vllogic/dalishen_pi_h7p20/docs/reference_schs/HME-H7P0P20N0L176-M2H1_Eth_EVB_1_4原理图.pdf

## input voltage range

5V-14V | P12V

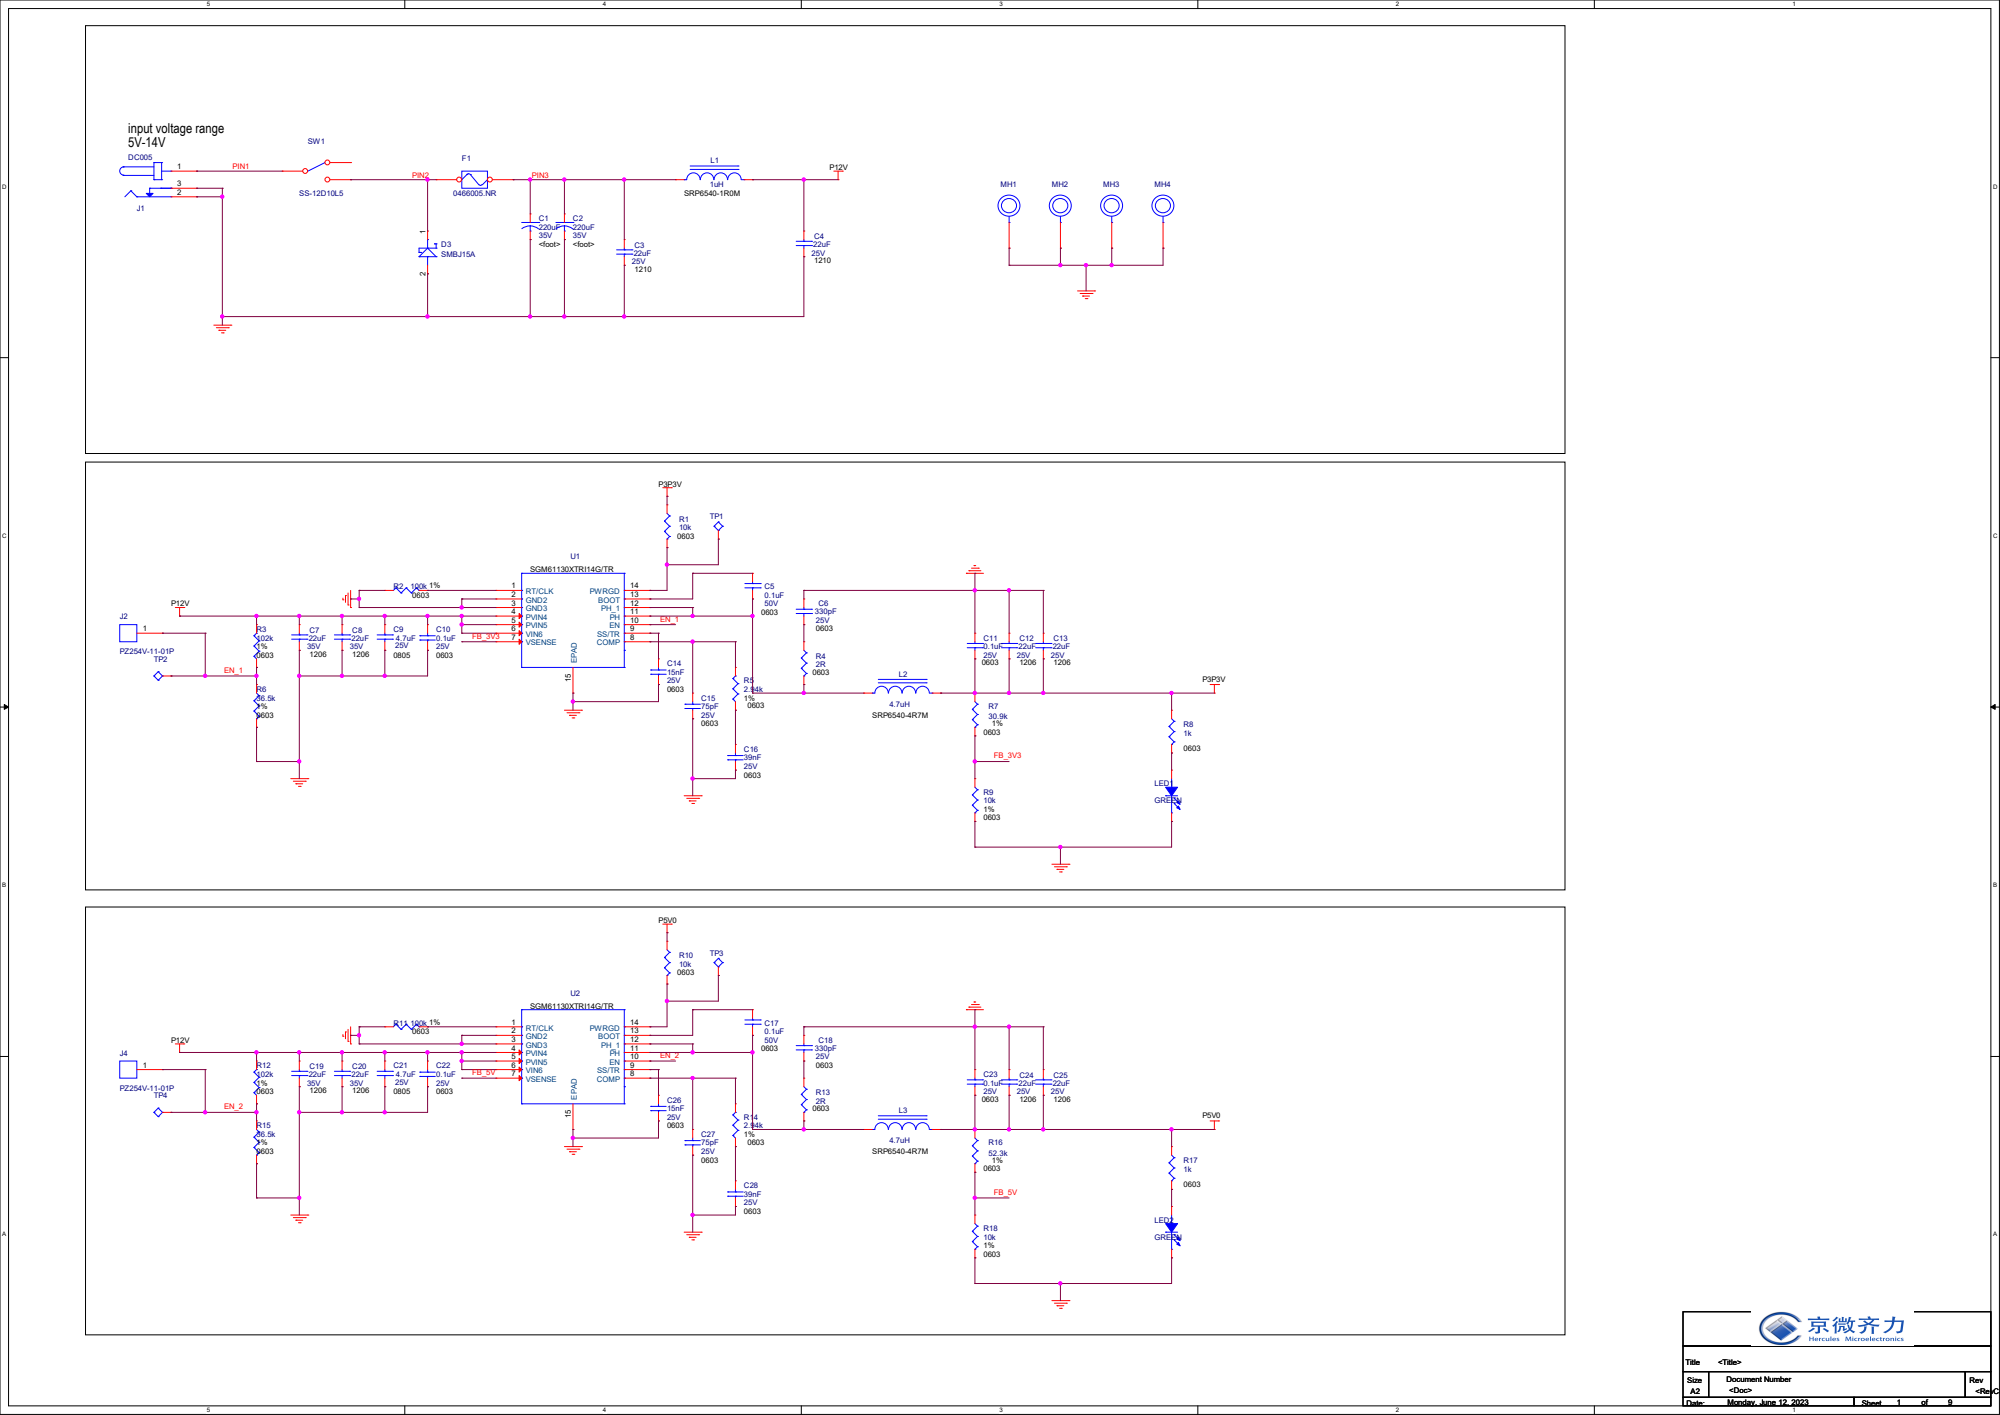
[picture p29: page 1]

# RXC_B RXDV_B RXD_B0 RXD_B3 GTXCLK_B

# TXD_B0 TXD_B1 TXD_B2 TXD_B3 RXD_B1 RXD_B2

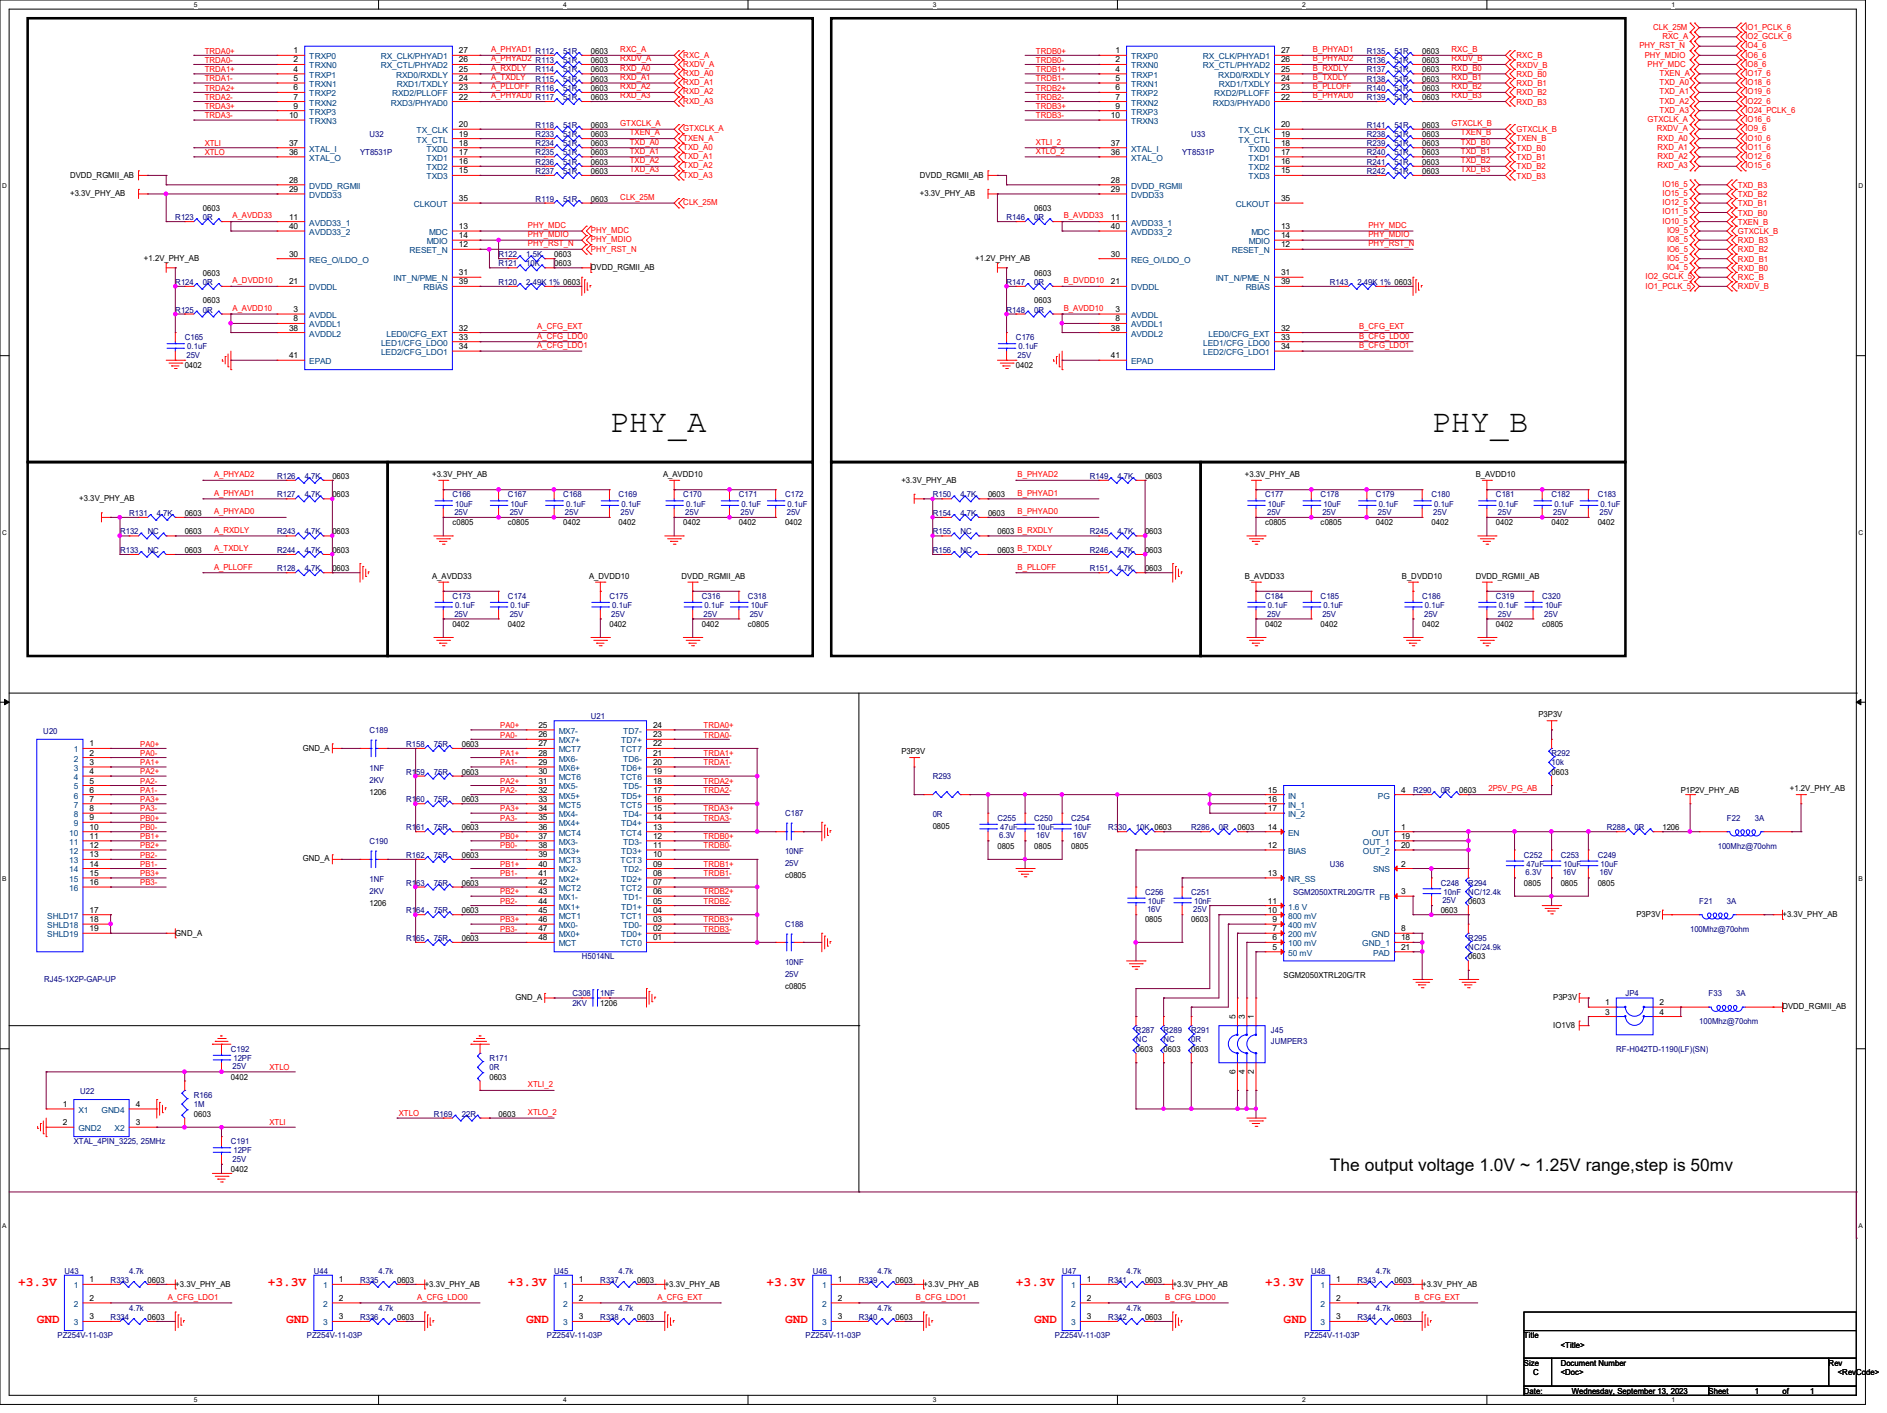
[picture p30: page 2]

The output voltage 1.0V ~ 1.25V range,step is 50mv

D D

# VCC5V_3

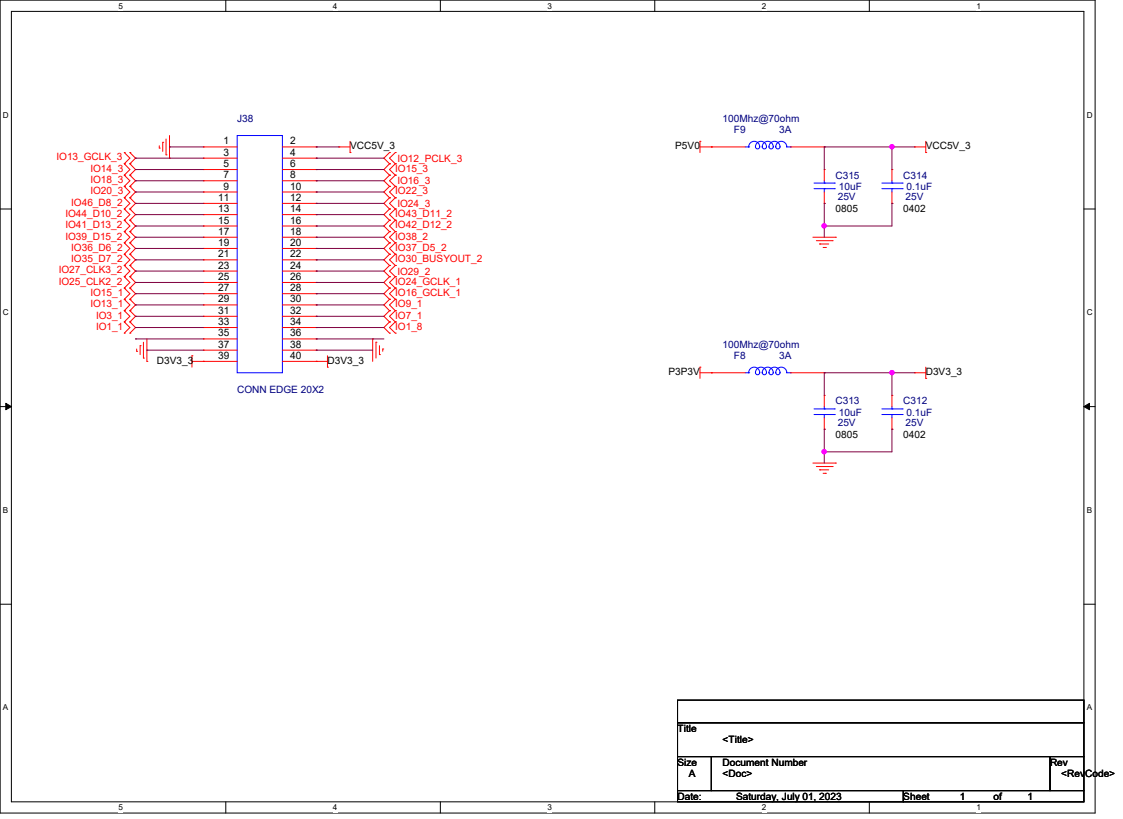
[picture p31: page 3]
VCC5V_3; IO16_GCLK_1; IO25_CLK2_2; IO30_BUSYOUT_2; IO13_GCLK_3; IO12_PCLK_3; IO27_CLK3_2; IO24_GCLK_1; Title; Size; Document Number; Rev; Date:; Sheet; <Doc>; <RevCode>; <Title>; Saturday, July 01, 2023; 100Mhz@70ohm 3A; CONN EDGE 20X2

DC005

# input voltage range

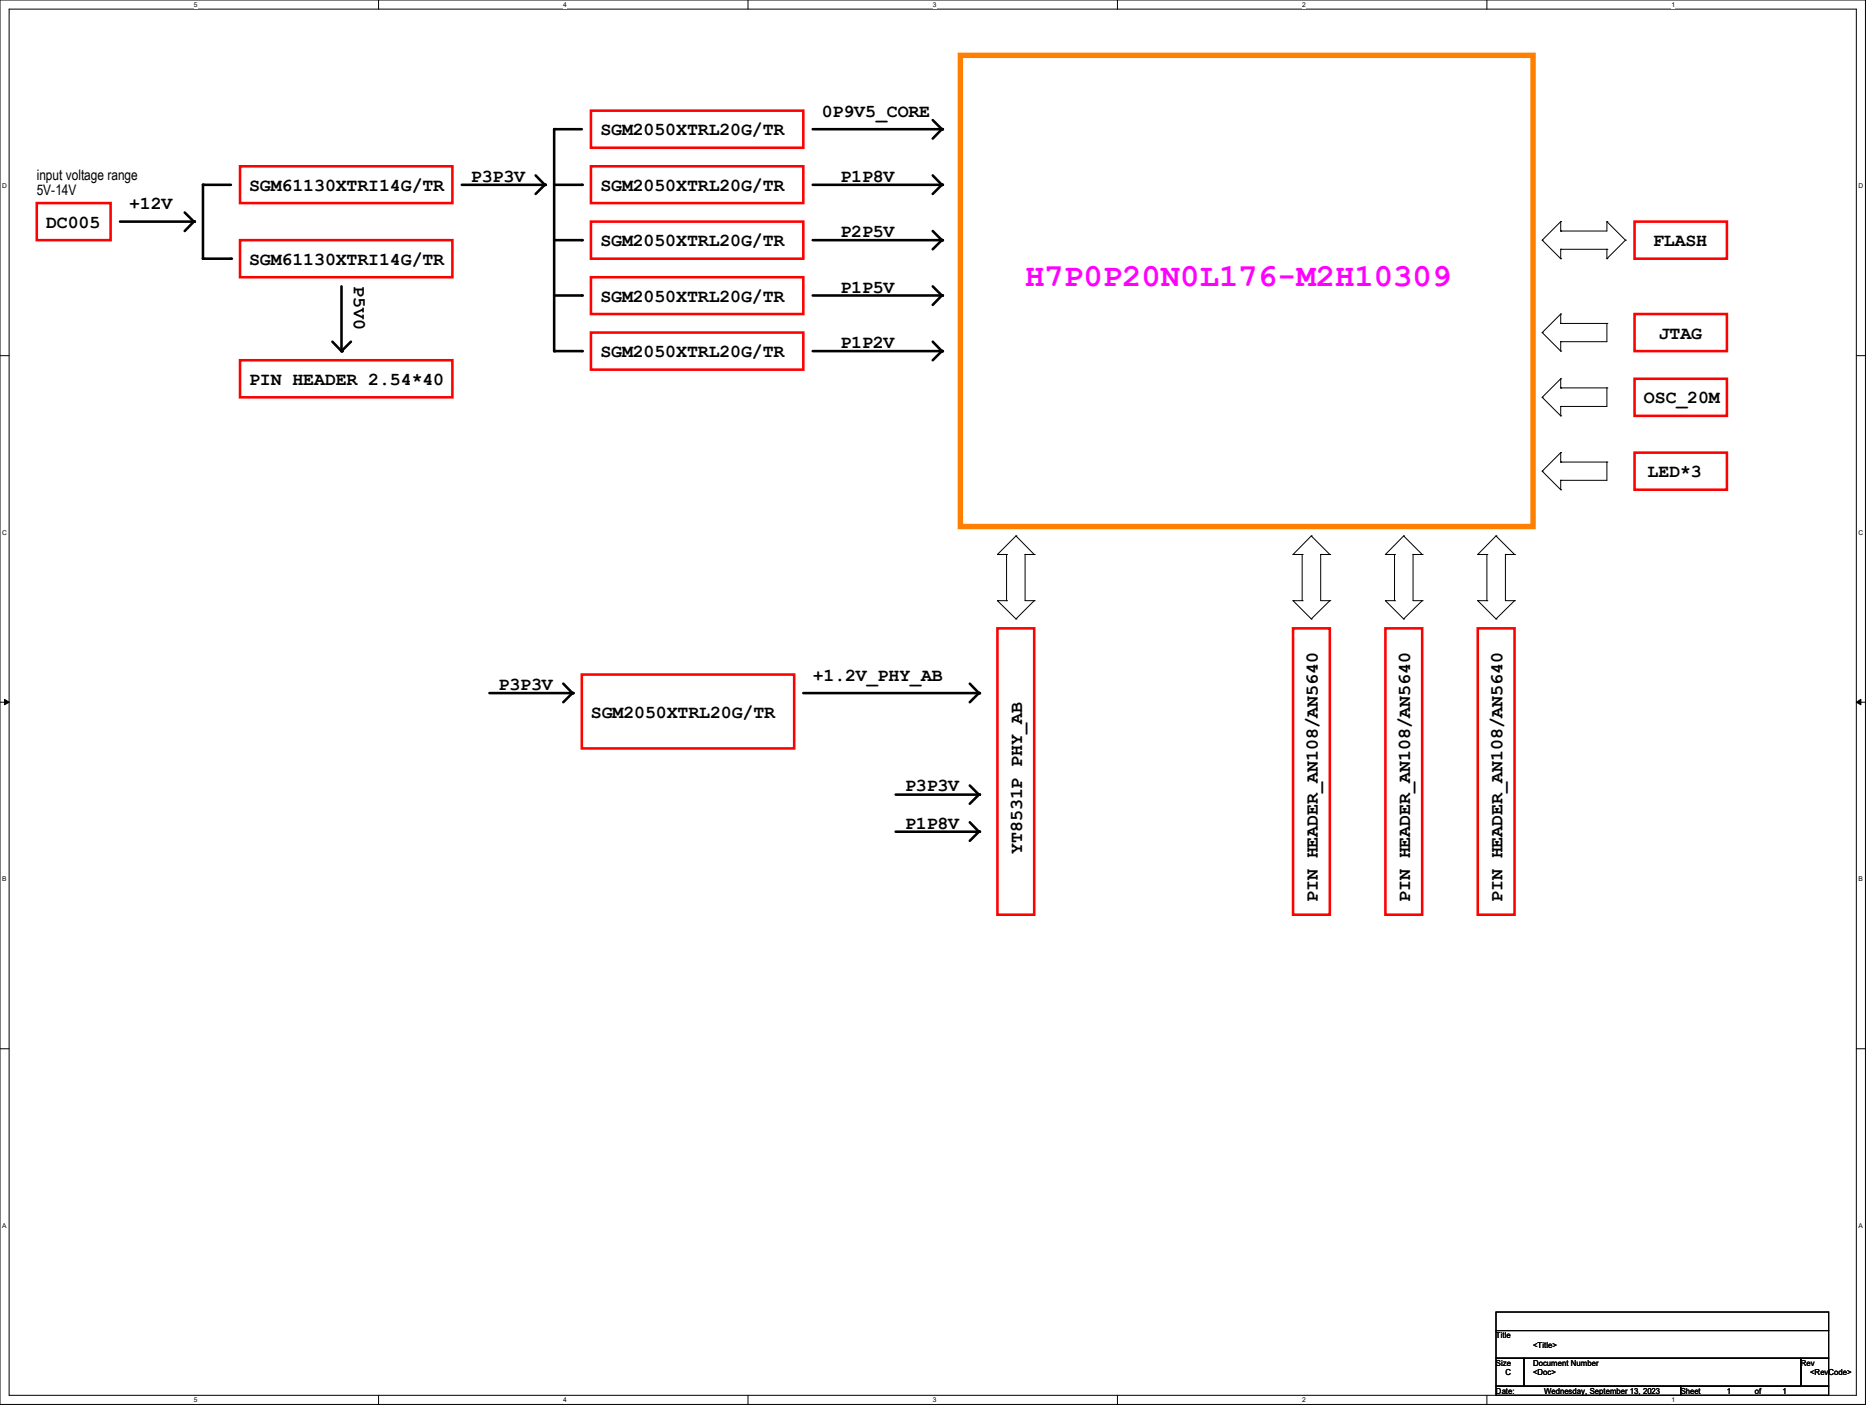
[picture p32: page 4]
SGM61130XTRI14G/TR; LED*3; FLASH; OSC_20M; JTAG YT8531P PHY_AB; PIN HEADER_AN108/AN5640; SGM2050XTRL20G/TR; 0P9V5_CORE; PIN HEADER 2.54*40; +1.2V_PHY_AB; Title Size; Document Number; Rev Date:; Sheet; of <Doc>; <RevCode>; <Title> C; Wednesday, September 13, 2023; 1 Title Size

### The output voltage 0.8V ~ 1.0V range,step is 50mv

# 2 S D3 R331

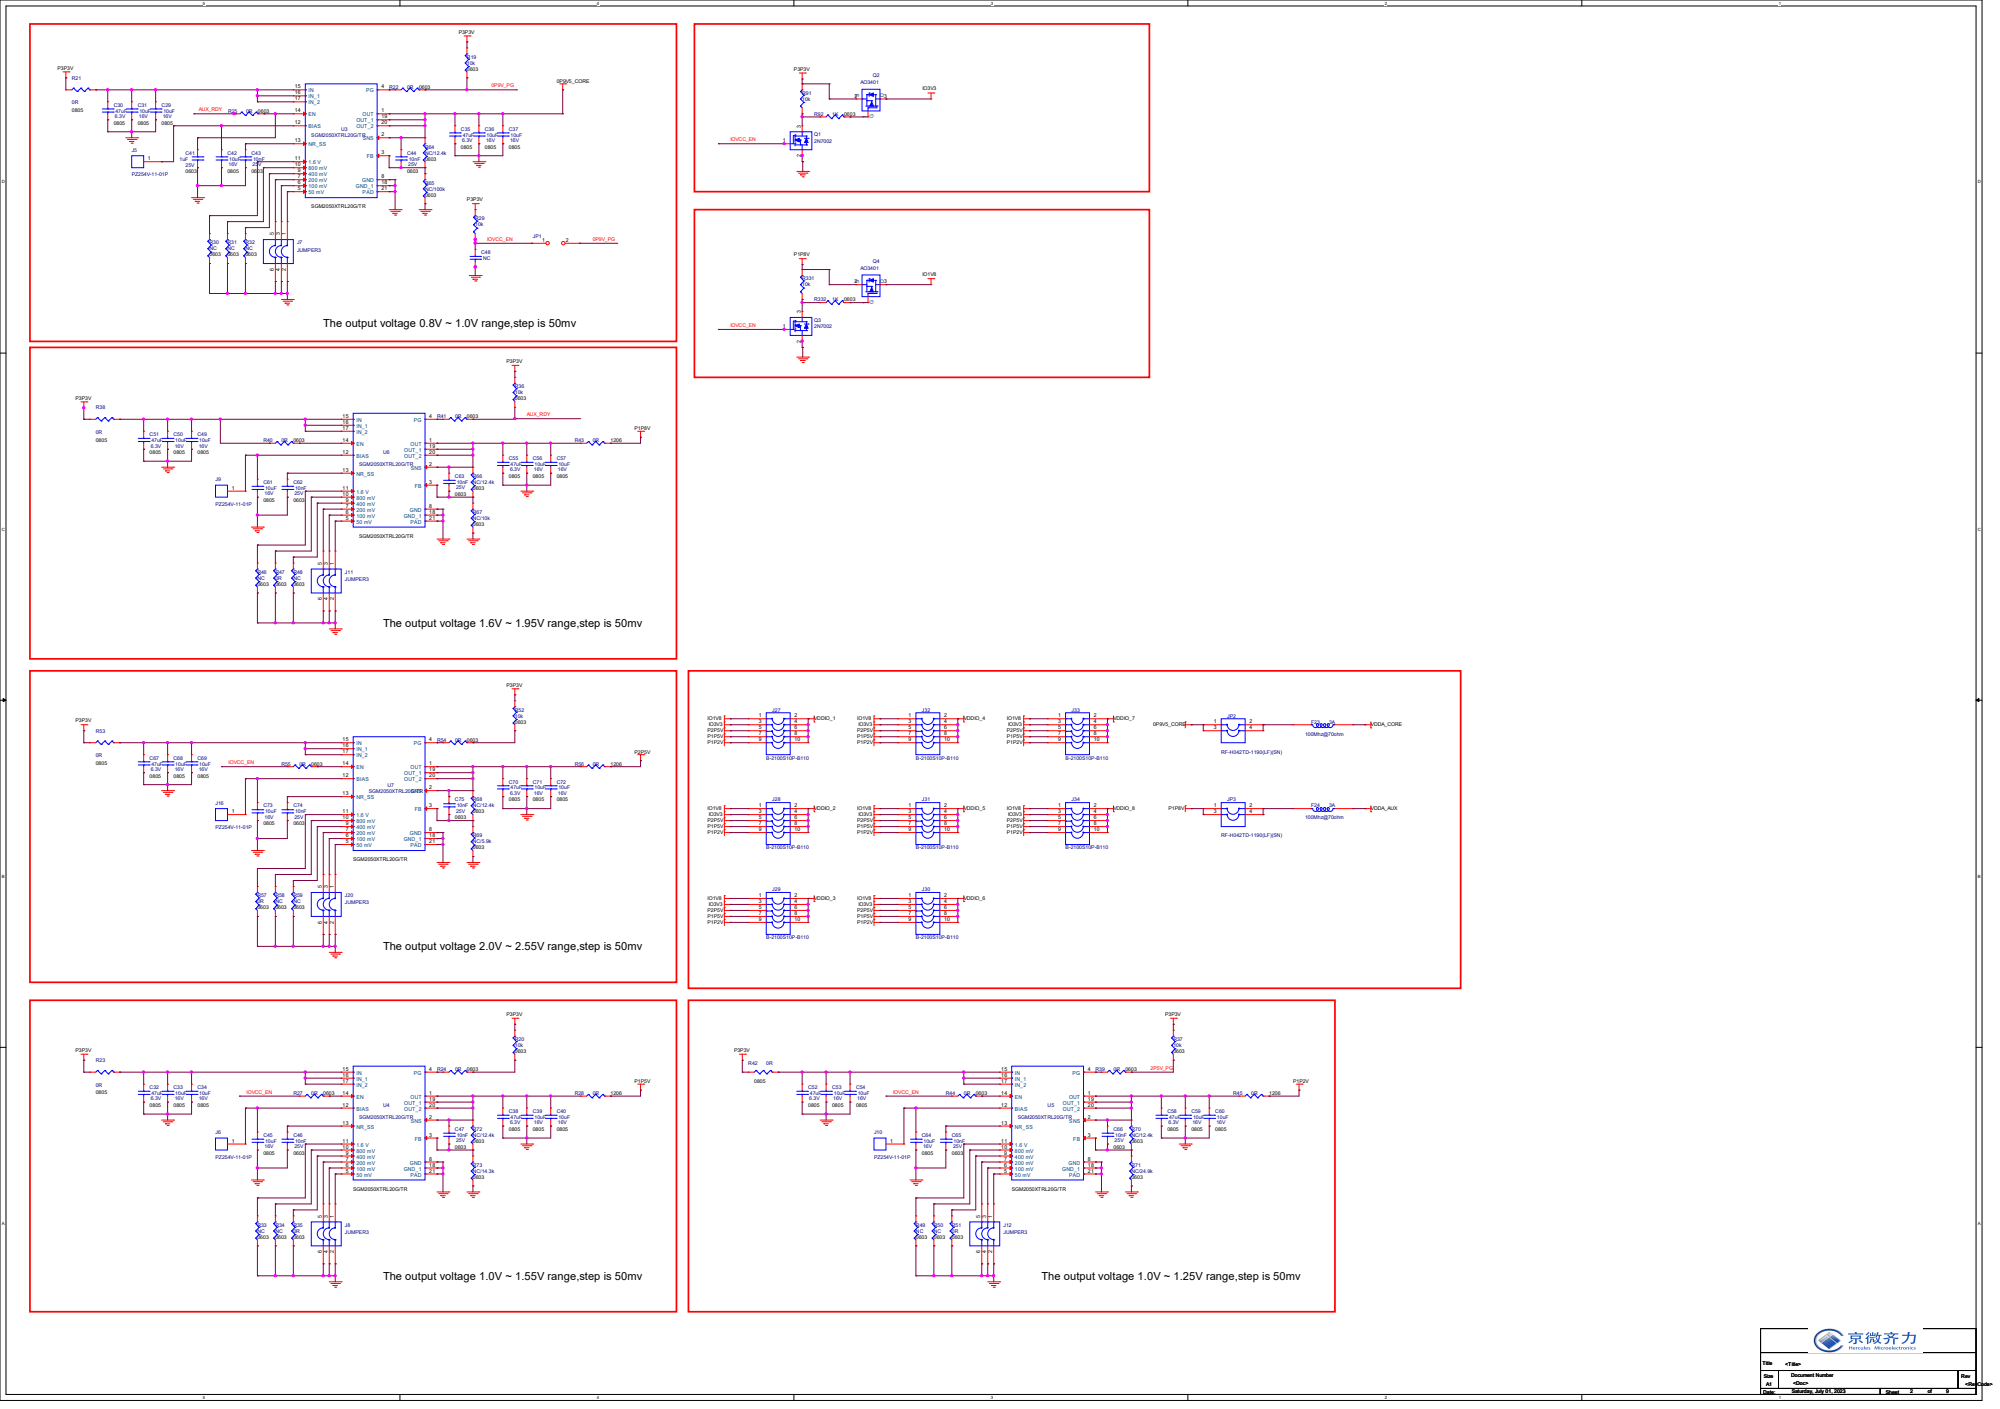
[picture p33: page 5]

The output voltage 1.6V ~ 1.95V range,step is 50mv

The output voltage 2.0V ~ 2.55V range,step is 50mv

D D

VDDA_AUX | VDDA_CORE

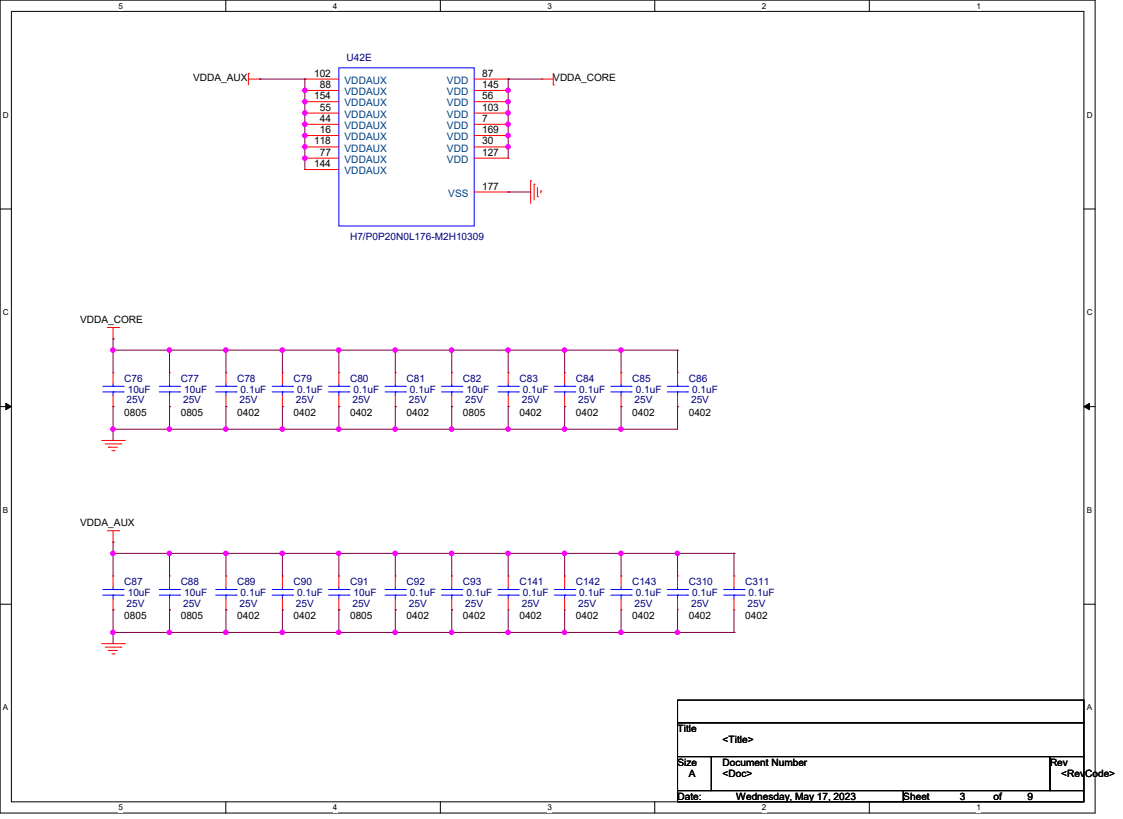
[picture p34: page 6]

# VDDIO1 VDDIO2 VDDIO_1

# BANK_1 BANK_2 U42A H7/P0P20N0L176-M2H10309

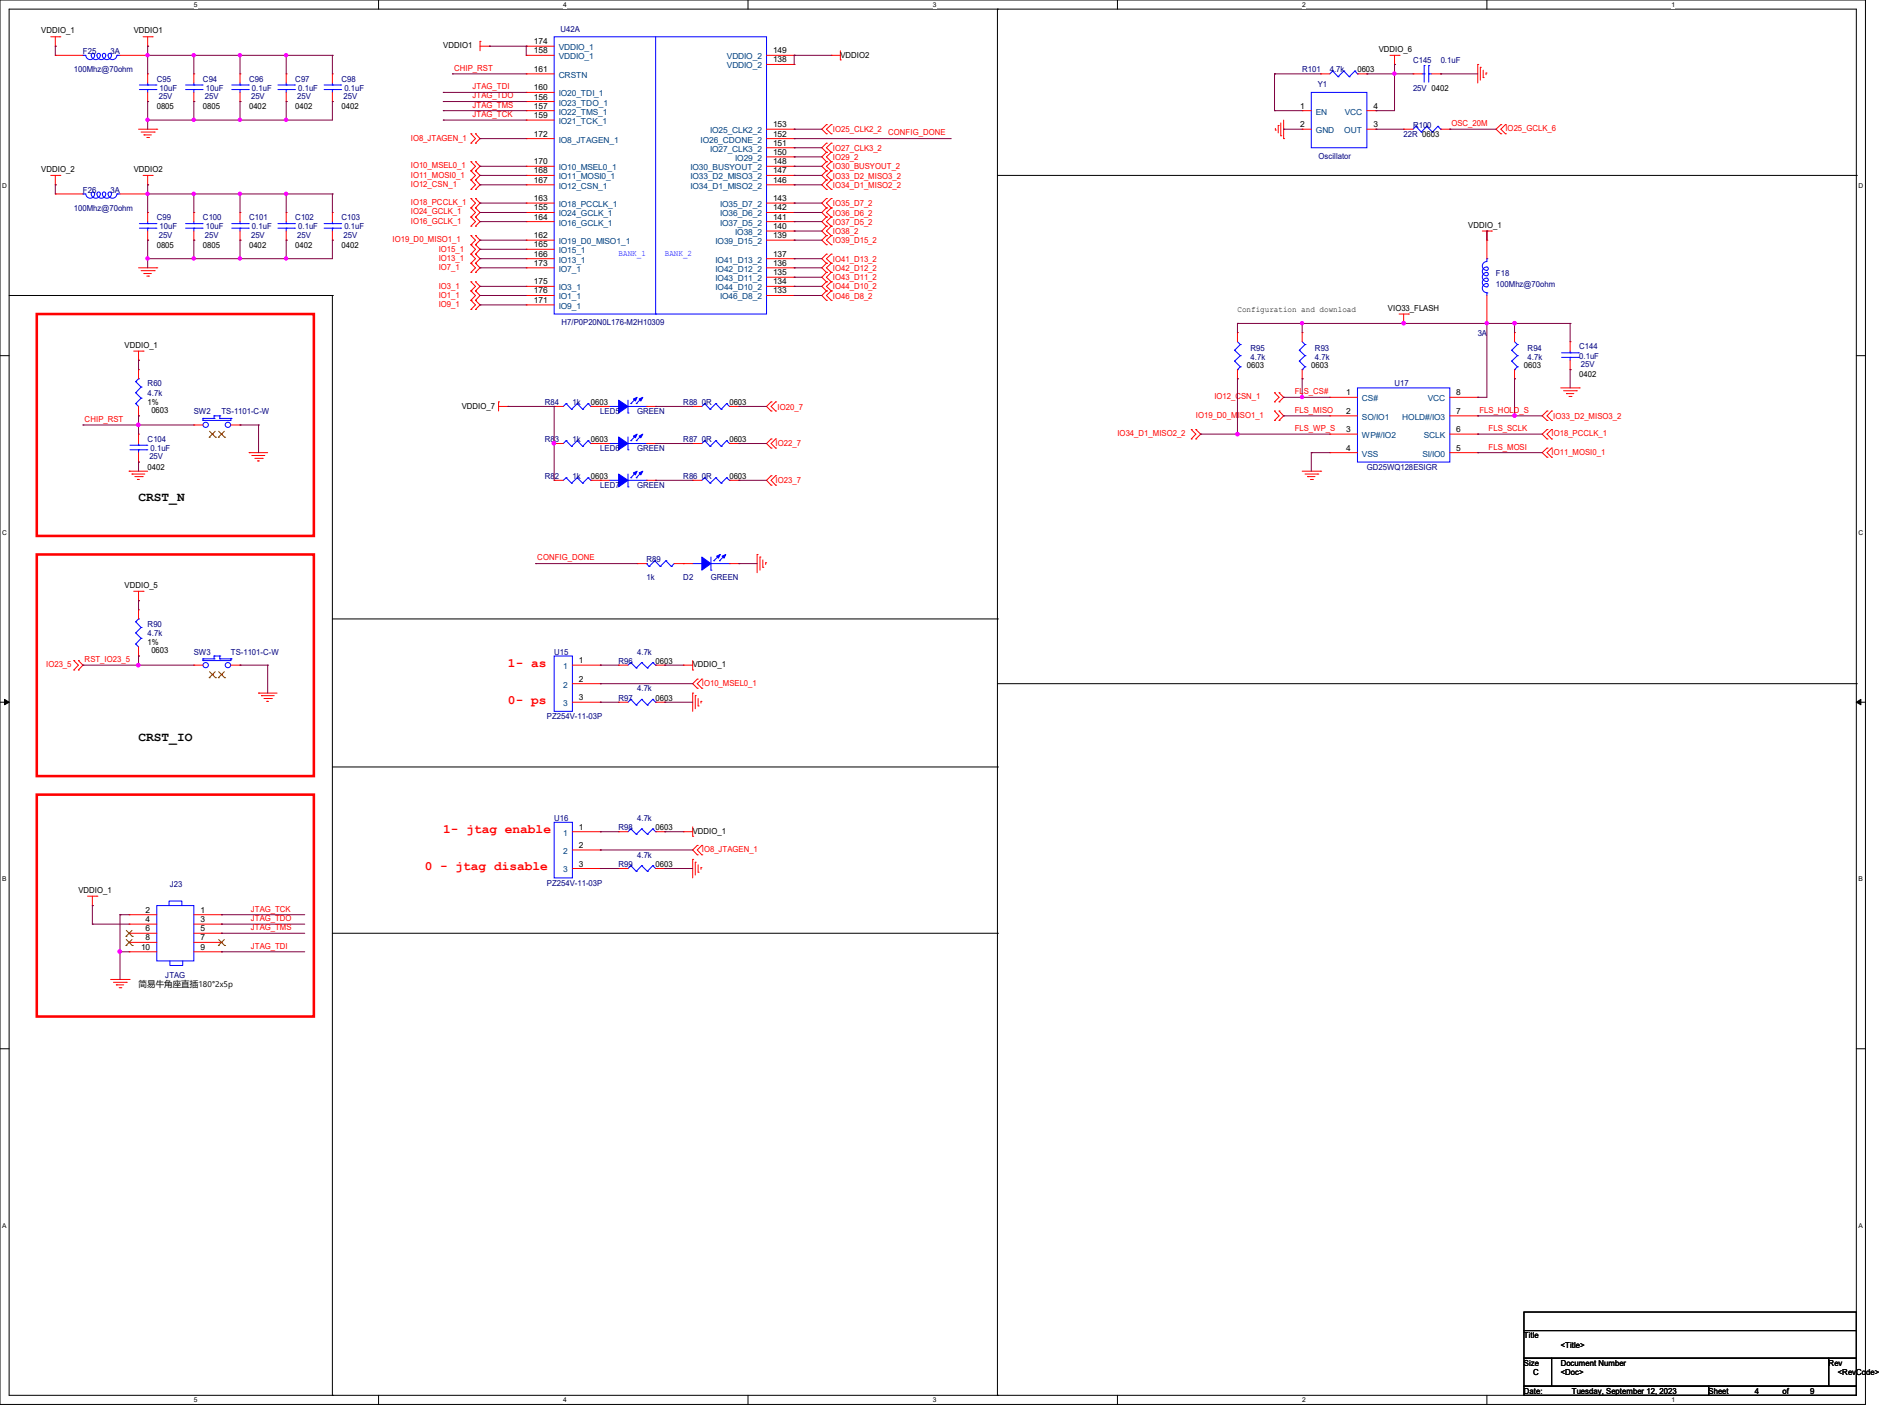
[picture p35: page 7]

VDDIO_1 | 100Mhz@70ohm

# VDDIO4 VDDIO3 VDDIO6 VDDIO5 VDDIO8 VDDIO7

# VDDIO_4 VDDIO_3 VDDIO_6 VDDIO_5 VDDIO_8 VDDIO_7

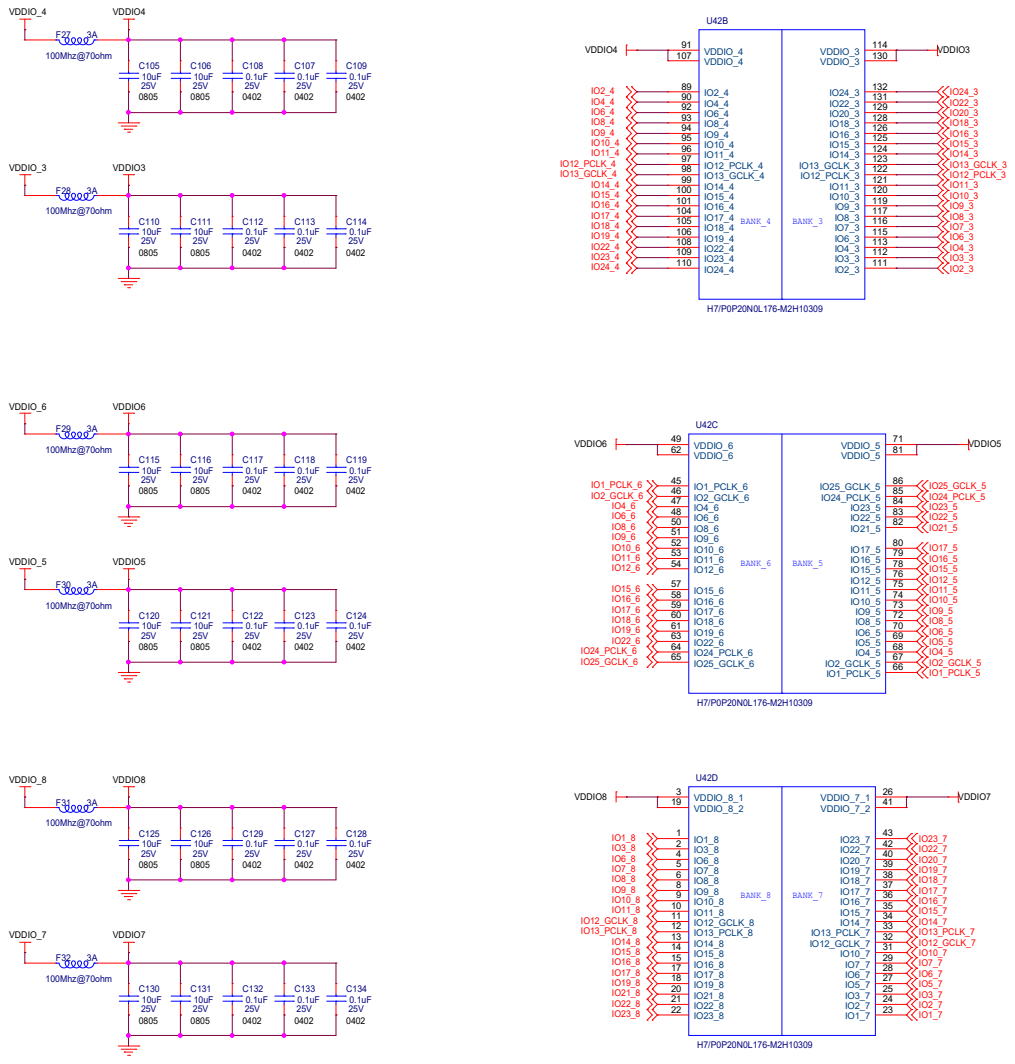
[picture p36: page 8]

D D

P5V0 | VCC5V_2

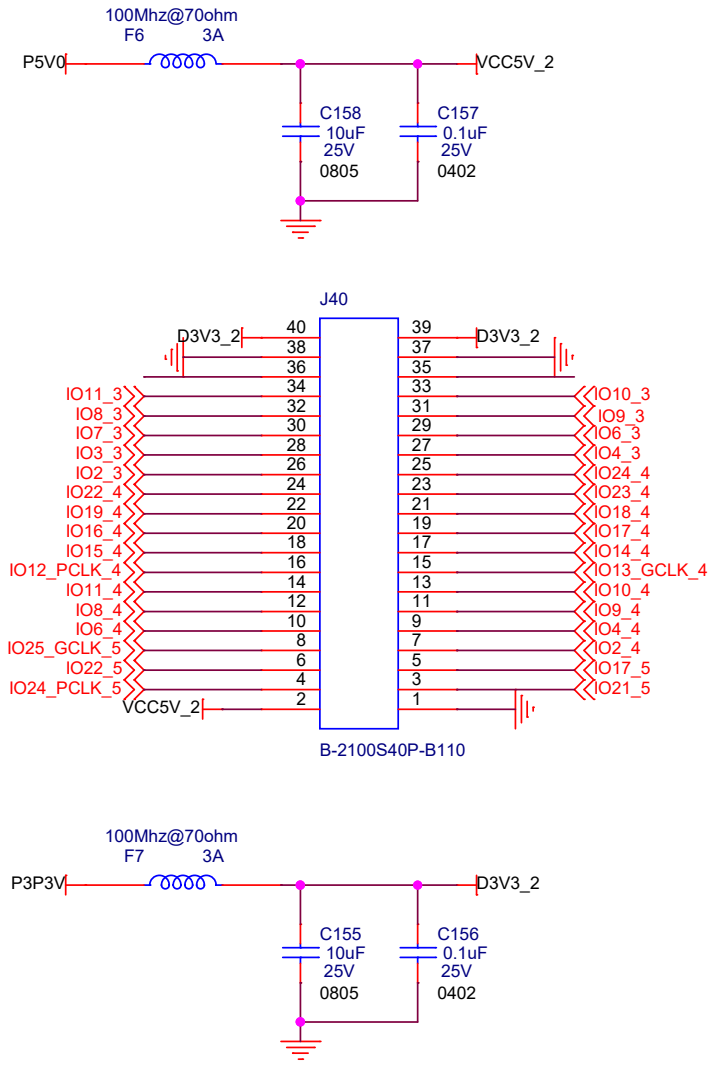
[picture p37: page 9]
VCC5V_2; IO13_GCLK_4; IO24_PCLK_5; IO25_GCLK_5; IO12_PCLK_4; Title; Size; Document Number; Rev; Date:; Sheet; <Doc>; <RevCode>; <Title>; Thursday, June 29, 2023; 100Mhz@70ohm 3A

# 3:LCD_R0/P1_DATA13/OS1/AD1DB11/VW_I2C_SCLK

# 1:GND

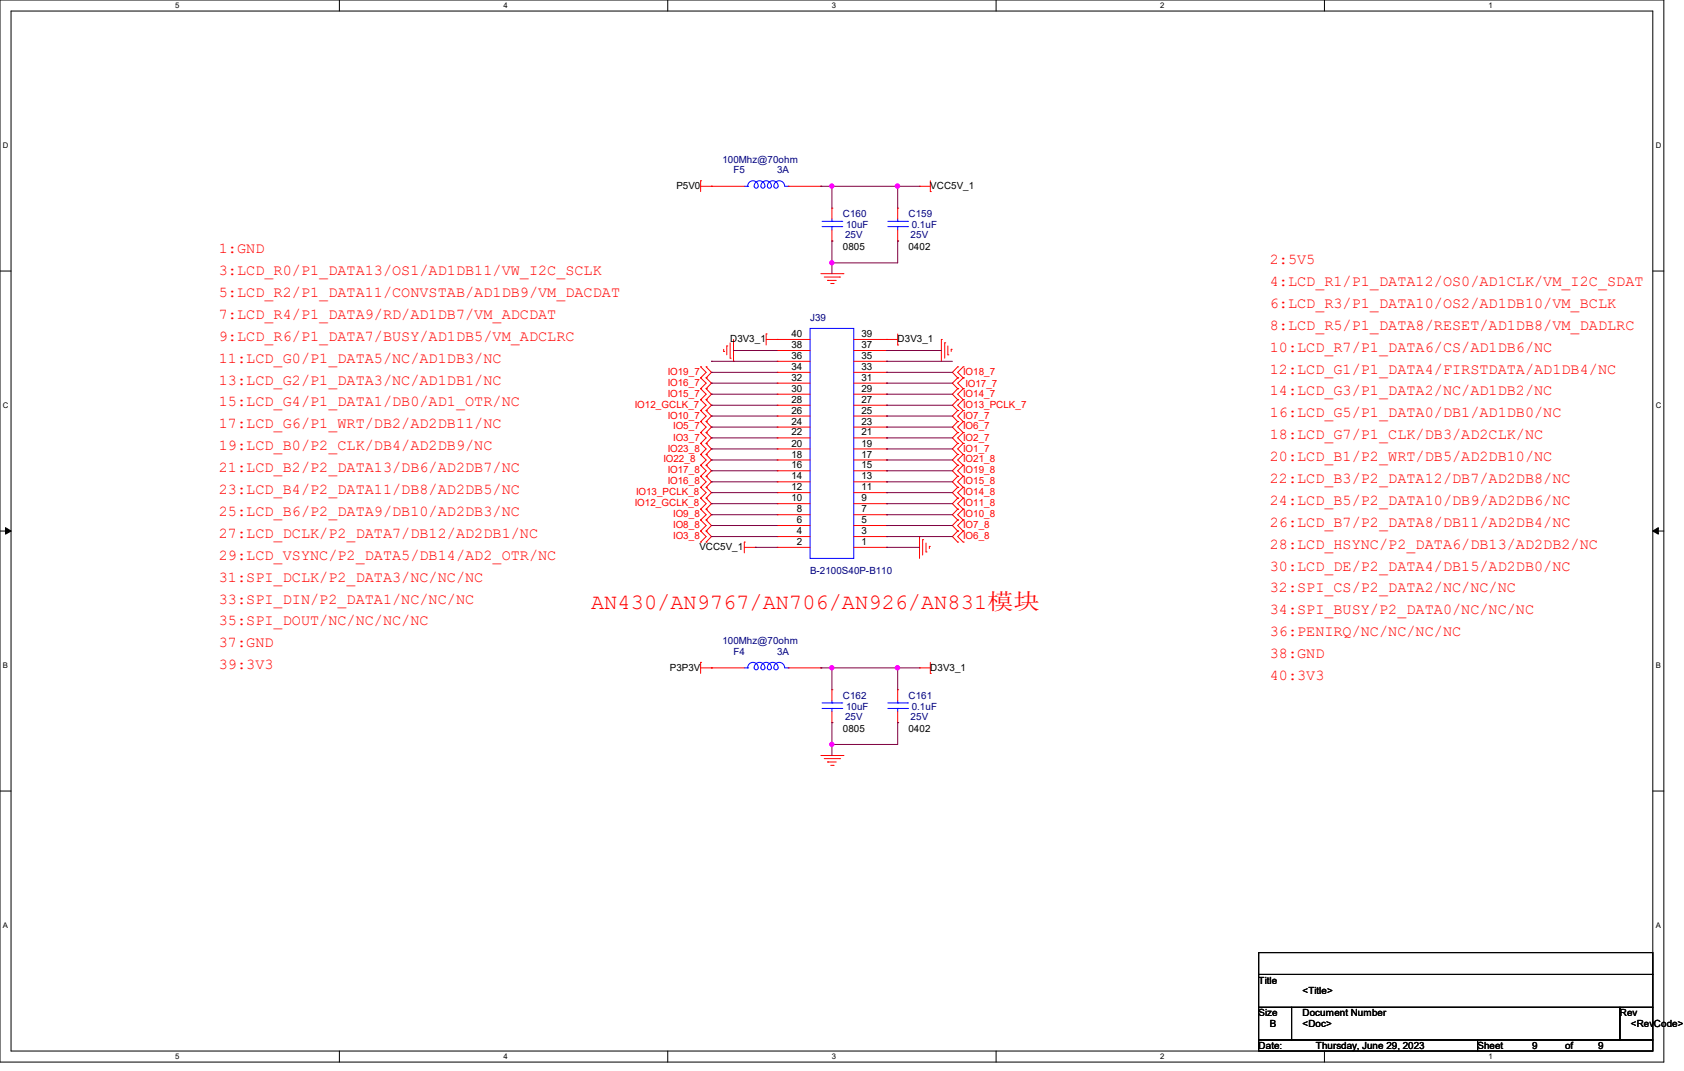
[picture p38: page 10]
11:LCD_G0/P1_DATA5/NC/AD1DB3/NC; 9:LCD_R6/P1_DATA7/BUSY/AD1DB5/VM_ADCLRC; 7:LCD_R4/P1_DATA9/RD/AD1DB7/VM_ADCDAT; 5:LCD_R2/P1_DATA11/CONVSTAB/AD1DB9/VM_DACDAT; 19:LCD_B0/P2_CLK/DB4/AD2DB9/NC; 17:LCD_G6/P1_WRT/DB2/AD2DB11/NC; 15:LCD_G4/P1_DATA1/DB0/AD1_OTR/NC; 13:LCD_G2/P1_DATA3/NC/AD1DB1/NC; 27:LCD_DCLK/P2_DATA7/DB12/AD2DB1/NC; 25:LCD_B6/P2_DATA9/DB10/AD2DB3/NC; 23:LCD_B4/P2_DATA11/DB8/AD2DB5/NC; 21:LCD_B2/P2_DATA13/DB6/AD2DB7/NC; 35:SPI_DOUT/NC/NC/NC/NC; 33:SPI_DIN/P2_DATA1/NC/NC/NC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
