vllogic/dalishen_pi_h7p20/docs/reference_schs/MLK-S301-20230721.pdf

# 2 S D3 C⁶ 22uF/25V

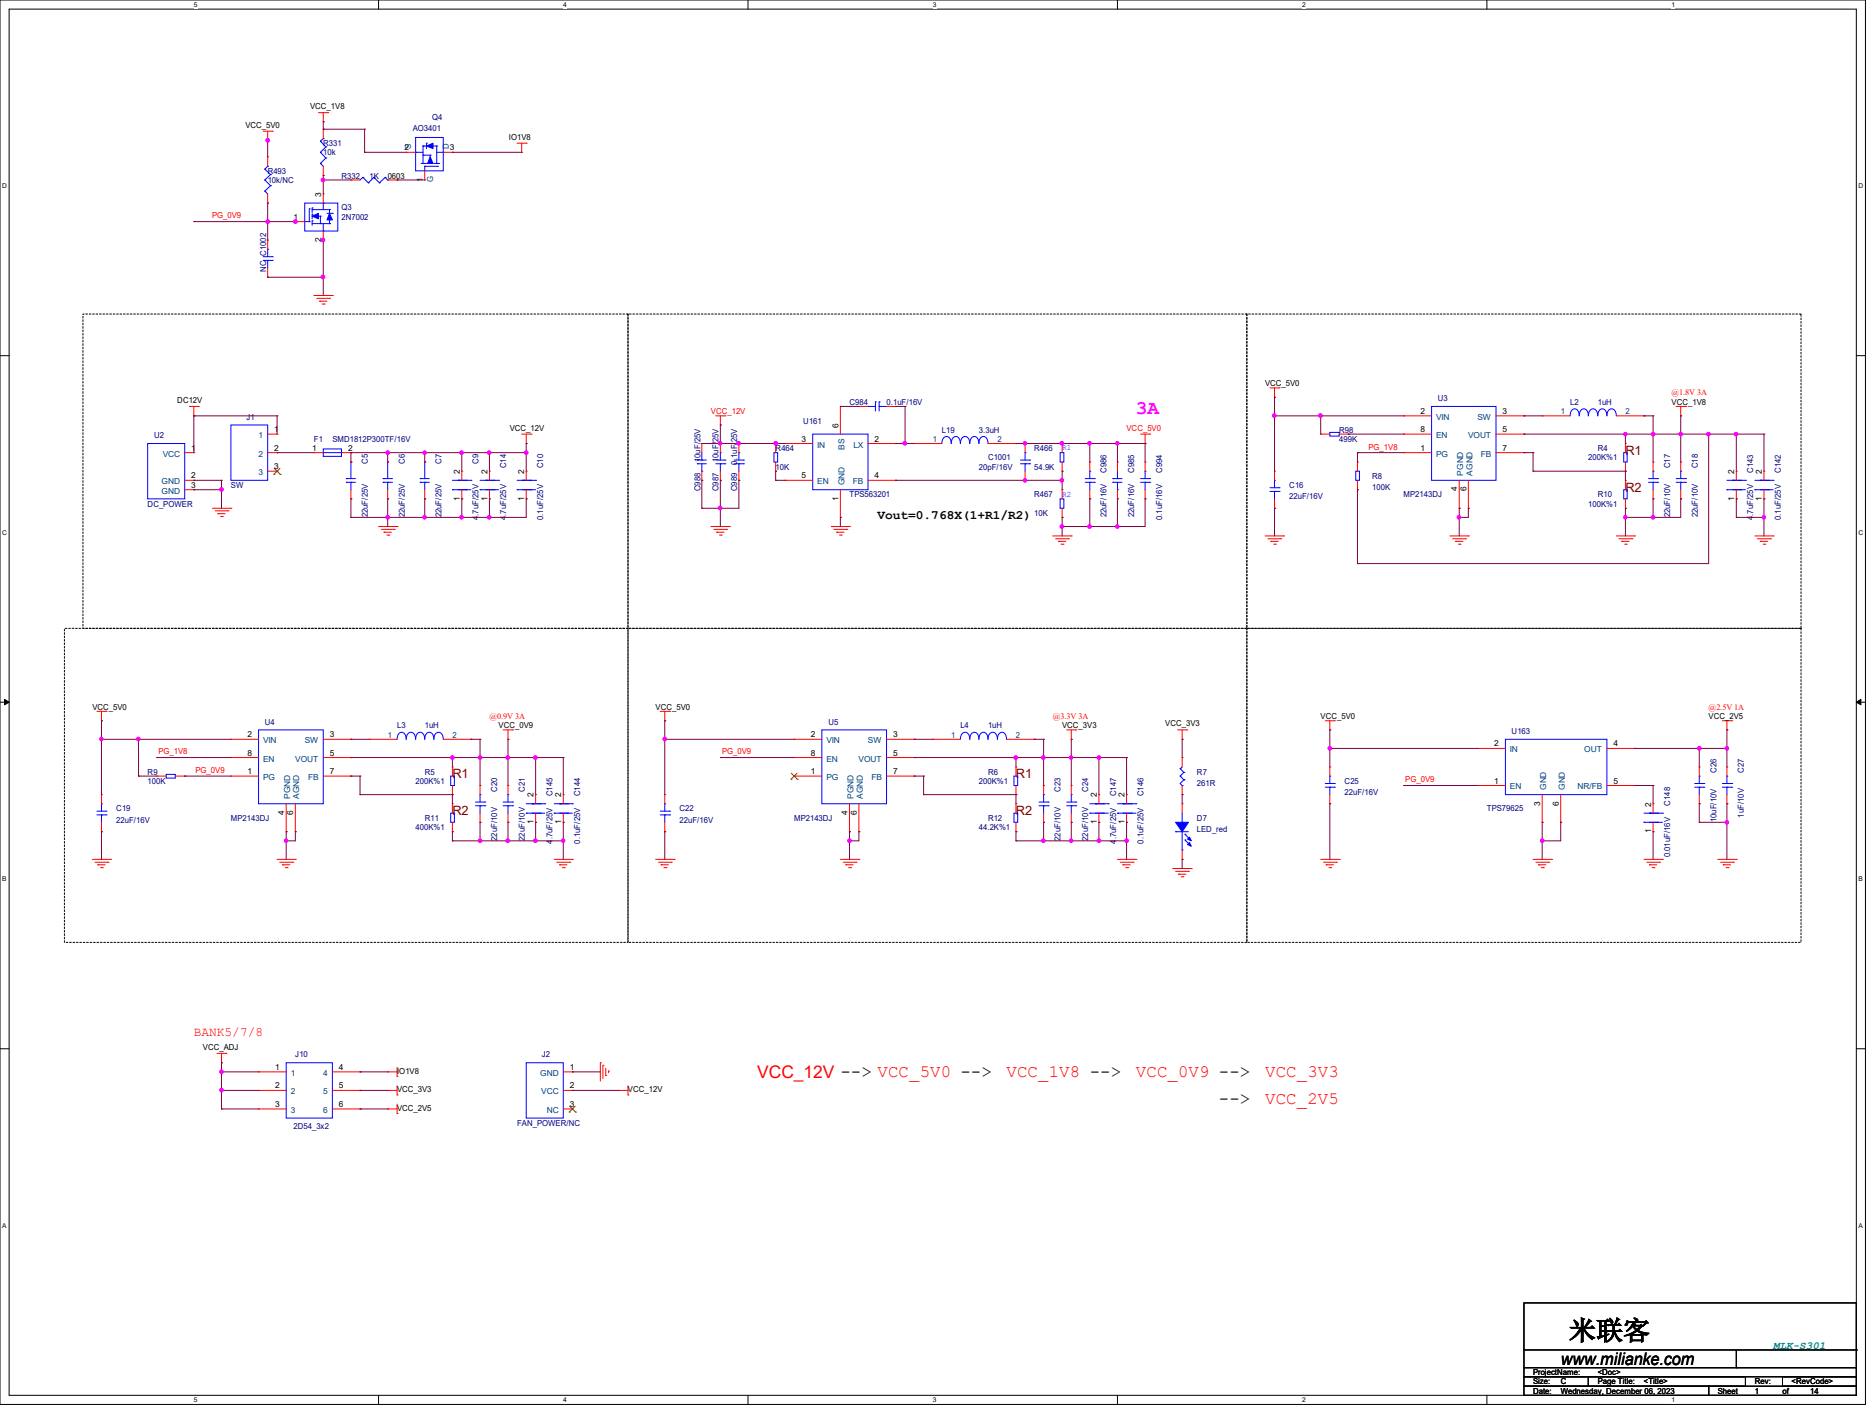
[picture p39: page 1]

3 OUT 4 NR/FB 5 GND

VDDA_AUX | VDDA_CORE
VCC_1V8 | VCC_0V9

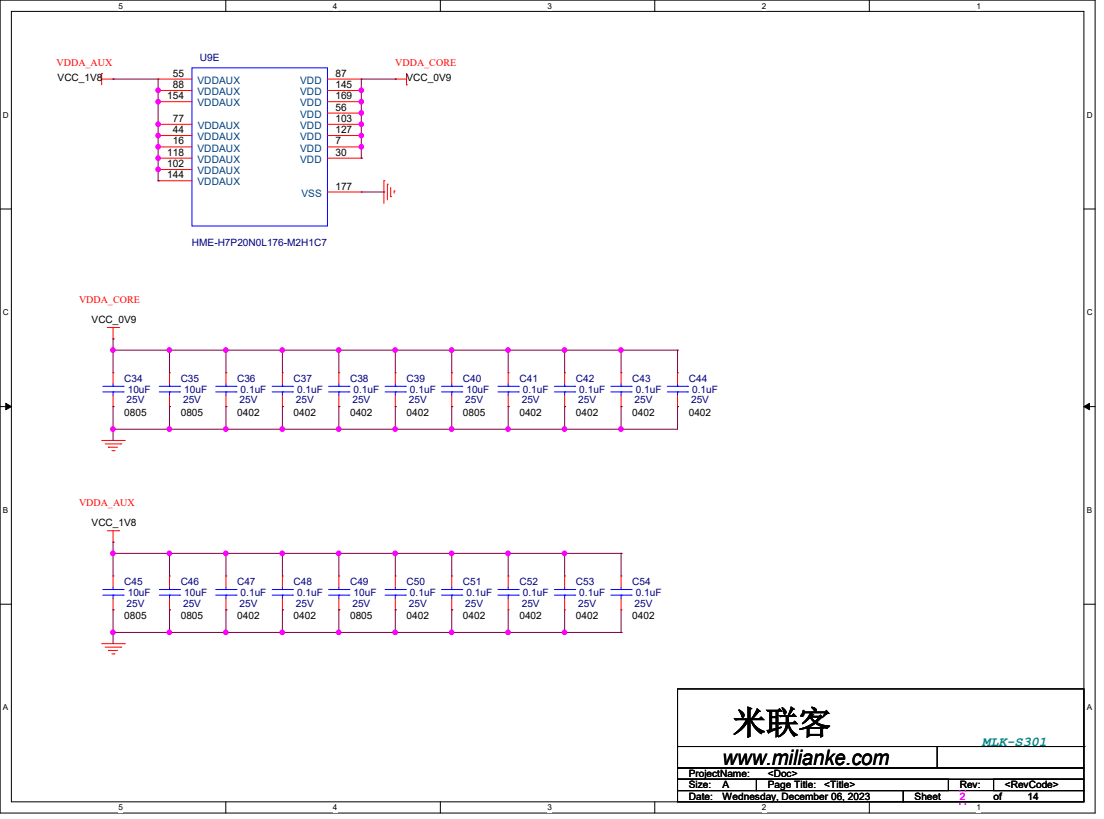
[picture p40: page 2]

### VDDIO_1

### VDDIO_2

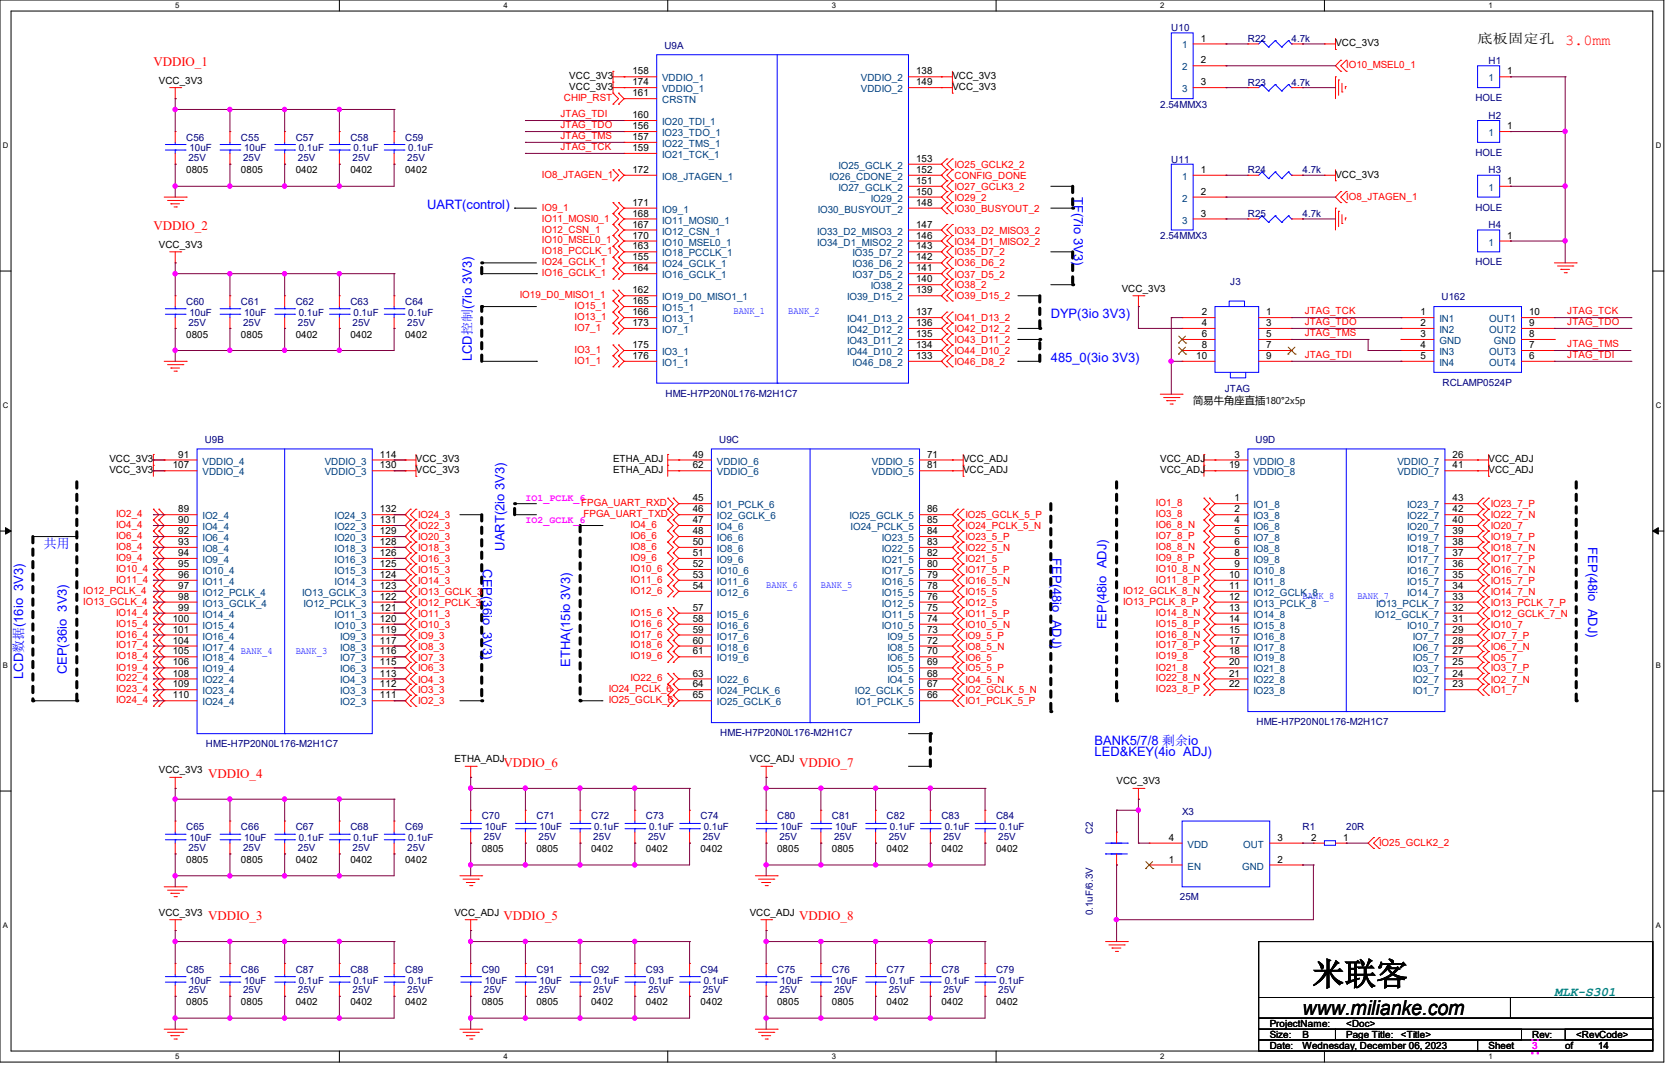
[picture p41: page 3]

底板固定孔 3.0mm FEP(48io ADJ)FEP⁽⁴⁸io ADJ⁾ FEP(48io ADJ)
U9A HME-H7P20N0L176-M2H1C7

## VCC_3V3

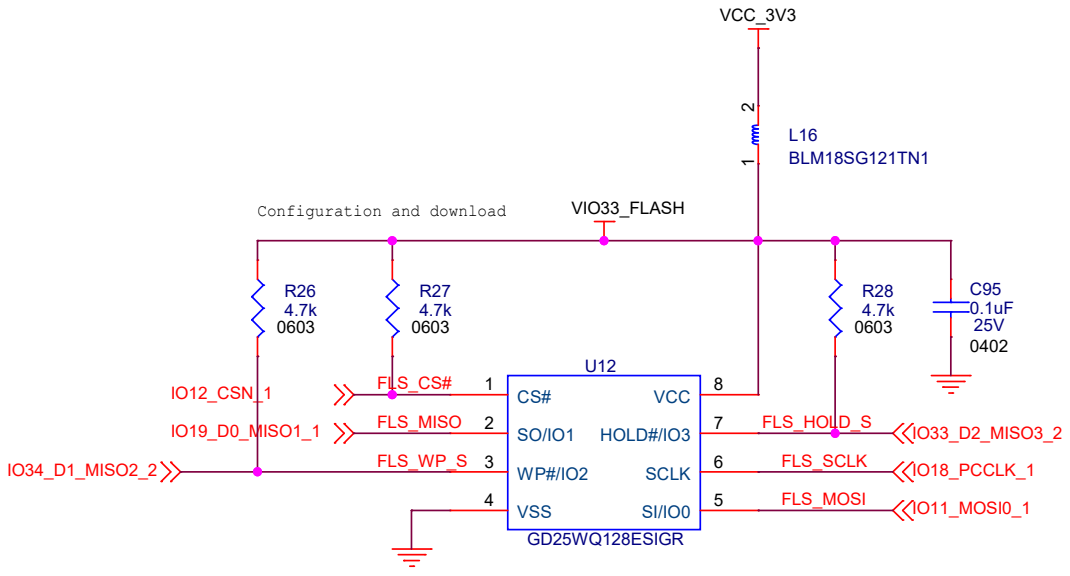
[picture p42: page 4]
MLK-S301; VIO33_FLASH; IO33_D2_MISO3_2; IO34_D1_MISO2_2; IO11_MOSI0_1; IO12_CSN_1; IO18_PCCLK_1; IO19_D0_MISO1_1; Date:; Sheet Wednesday, December 06, 2023; Wednesday, December 06, 2023; L16 1BLM18SG121TN1; GD25WQ128ESIGR; VSS 4; SCLK 6; HOLD#/IO3 7; VCC 8; FLS_WP_S; FLS_MISO; FLS_HOLD_S; FLS_SCLK; FLS_CS#; FLS_MOSI

Configuration and download

米联客
www.milianke.com

## VCC_3V3 VCC_3V3

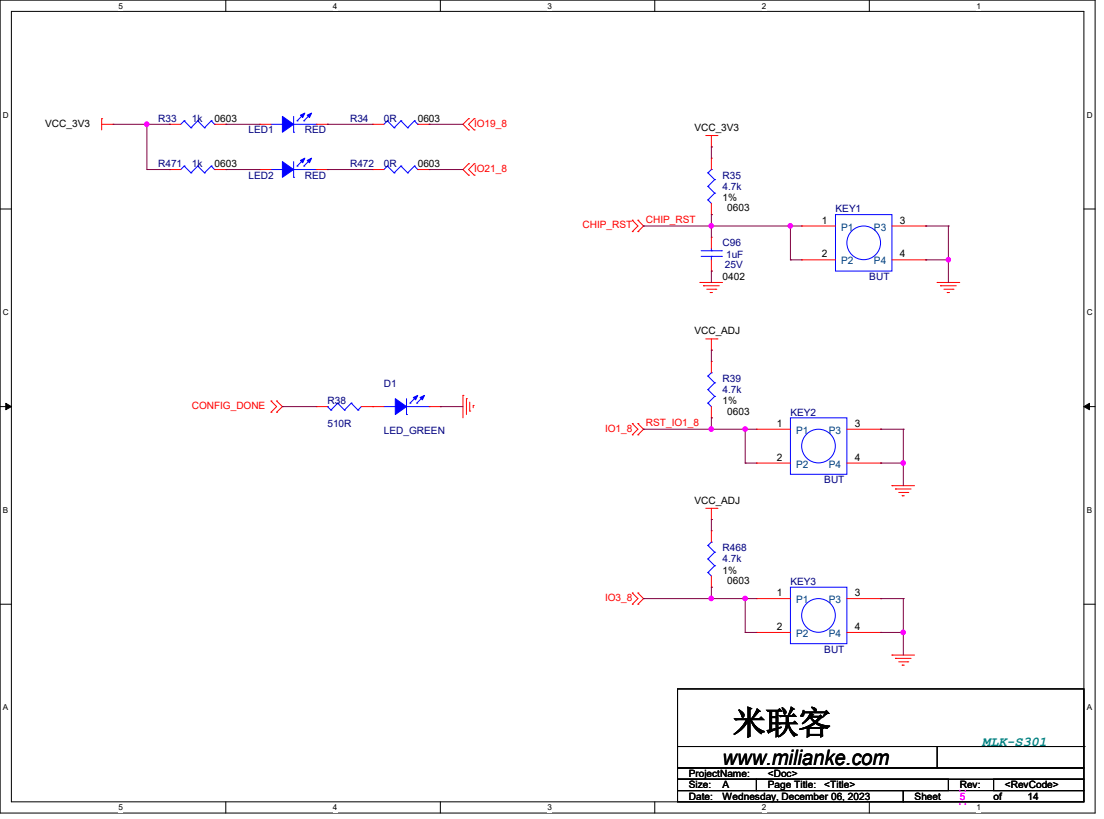
[picture p43: page 5]

## VBUS0_3V3

C97 | 100nF/25V

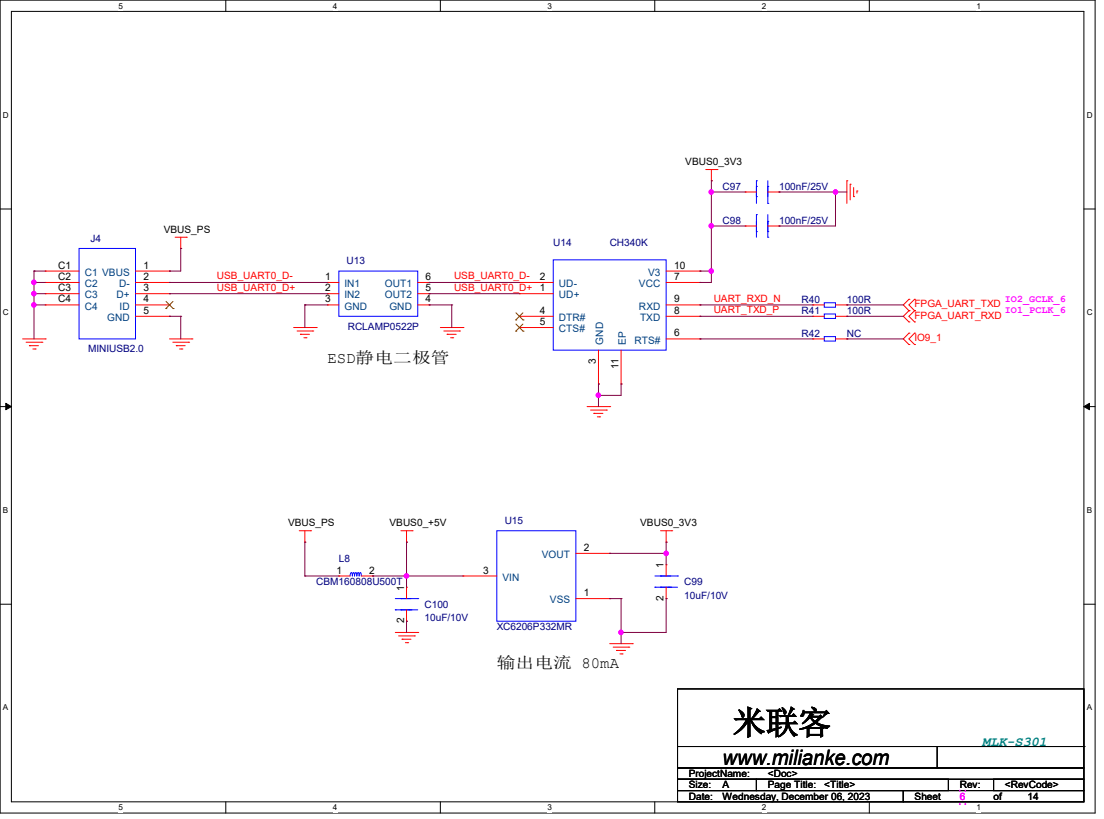
[picture p44: page 6]

HDI0+ 2 | HDI0- 3 | HDI1+ 4 | HDI1- 7 | HDI2+ 5 | HDI2- 6 | HDIO3+ 8 | HDIO3- 9 | TCT 1 | GND 10
VDD 4 | EN 1 | OUT | 3 GND | 2 C¹⁰⁴ 0.1uF/16V

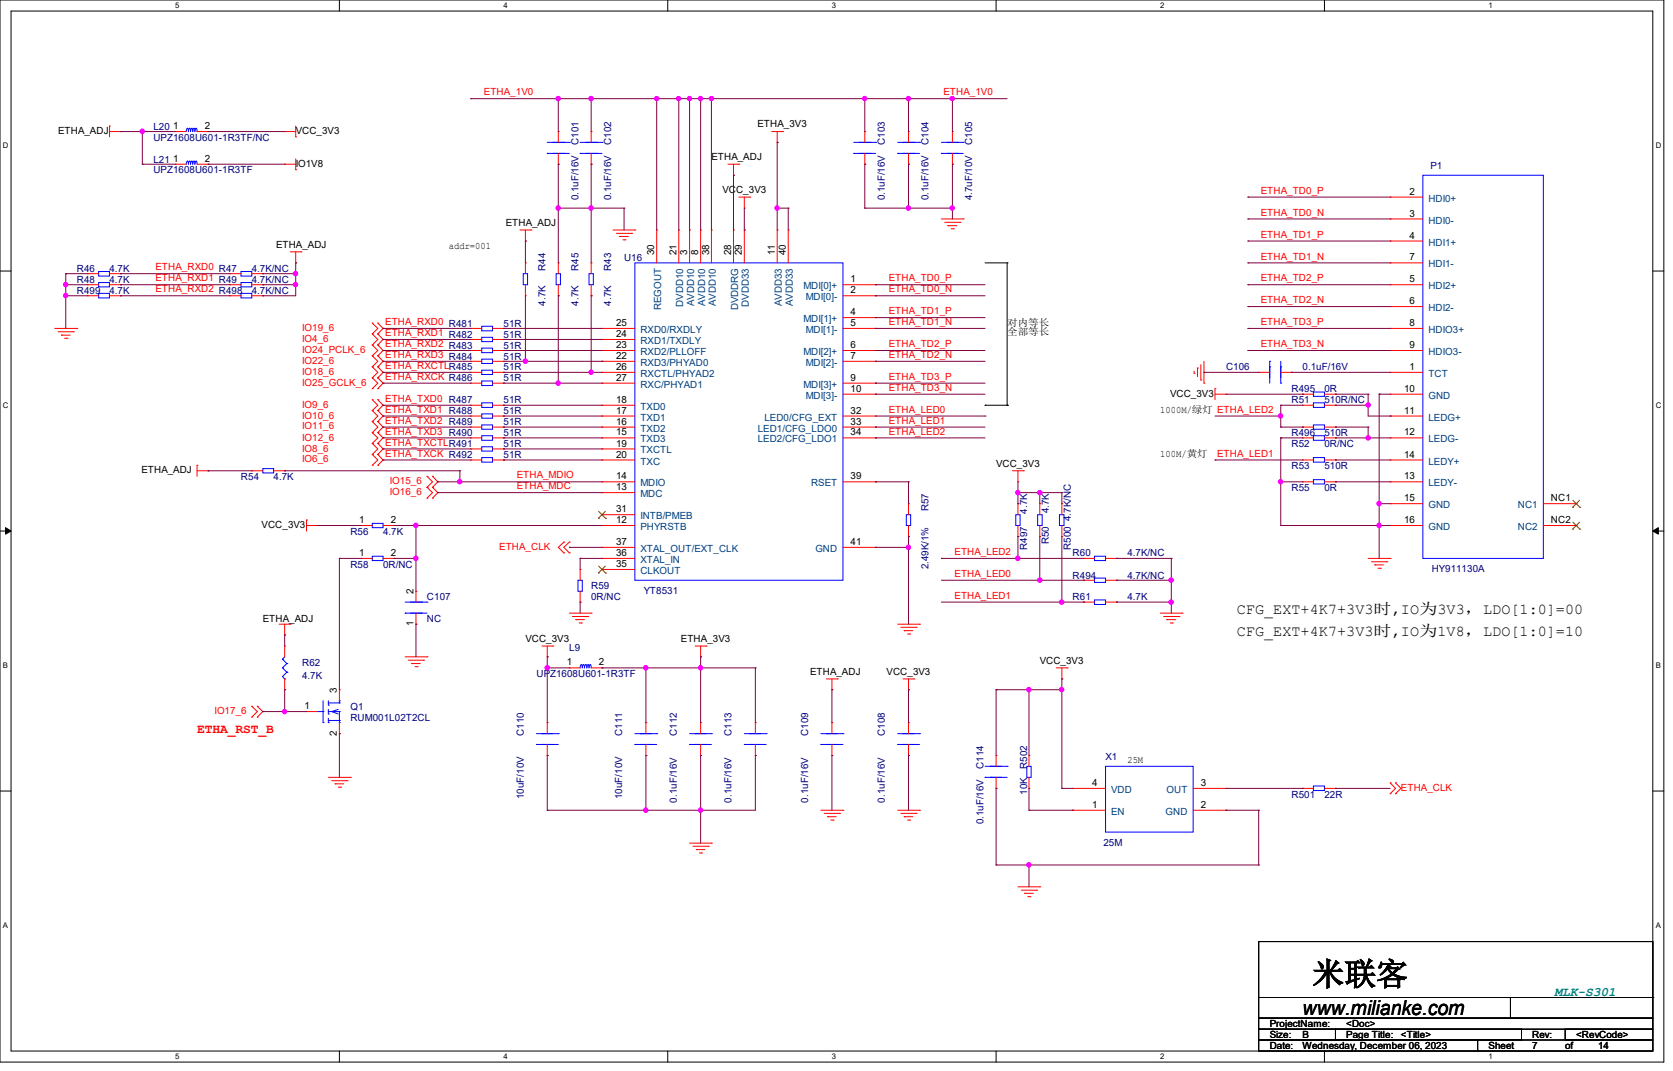
[picture p45: page 7]

### FEP(伪差分)

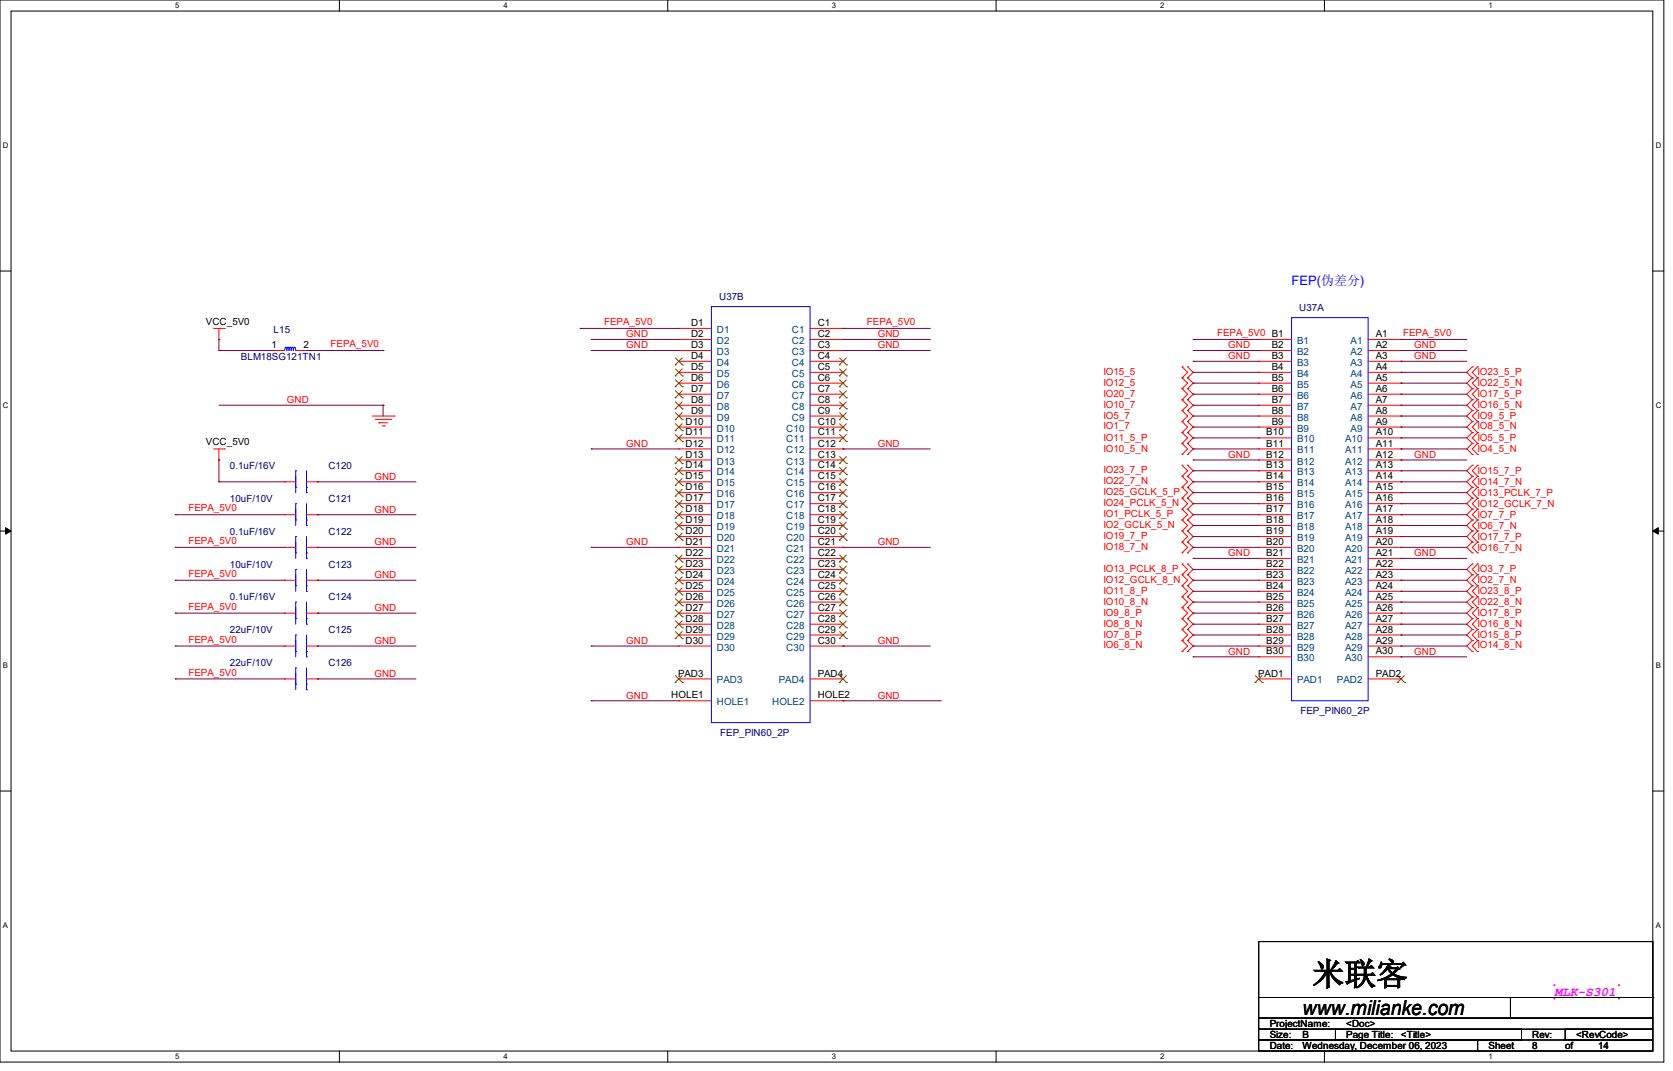
[picture p46: page 8]

GND GND

U19 RCLAMP0524P D1+ 1 | D1- 2 | GND 3 | D2+ 4 | D2- 5 | NC_6 | 6 NC_7 | 7 GND | 8 NC_9 | 9 NC_10 | 10 U21 RCLAMP0524P D1+ 1 | D1- 2 | GND 3 | D2+ 4 | D2- 5 | NC_6 | 6 NC_7 | 7 GND | 8 NC_9 | 9 NC_10 | 10 U23 RCLAMP0524P D1+ 1 | D1- 2 | GND 3 | D2+ 4 | D2- 5 | NC_6 | 6 NC_7 | 7 GND | 8 NC_9 | 9 NC_10 | 10

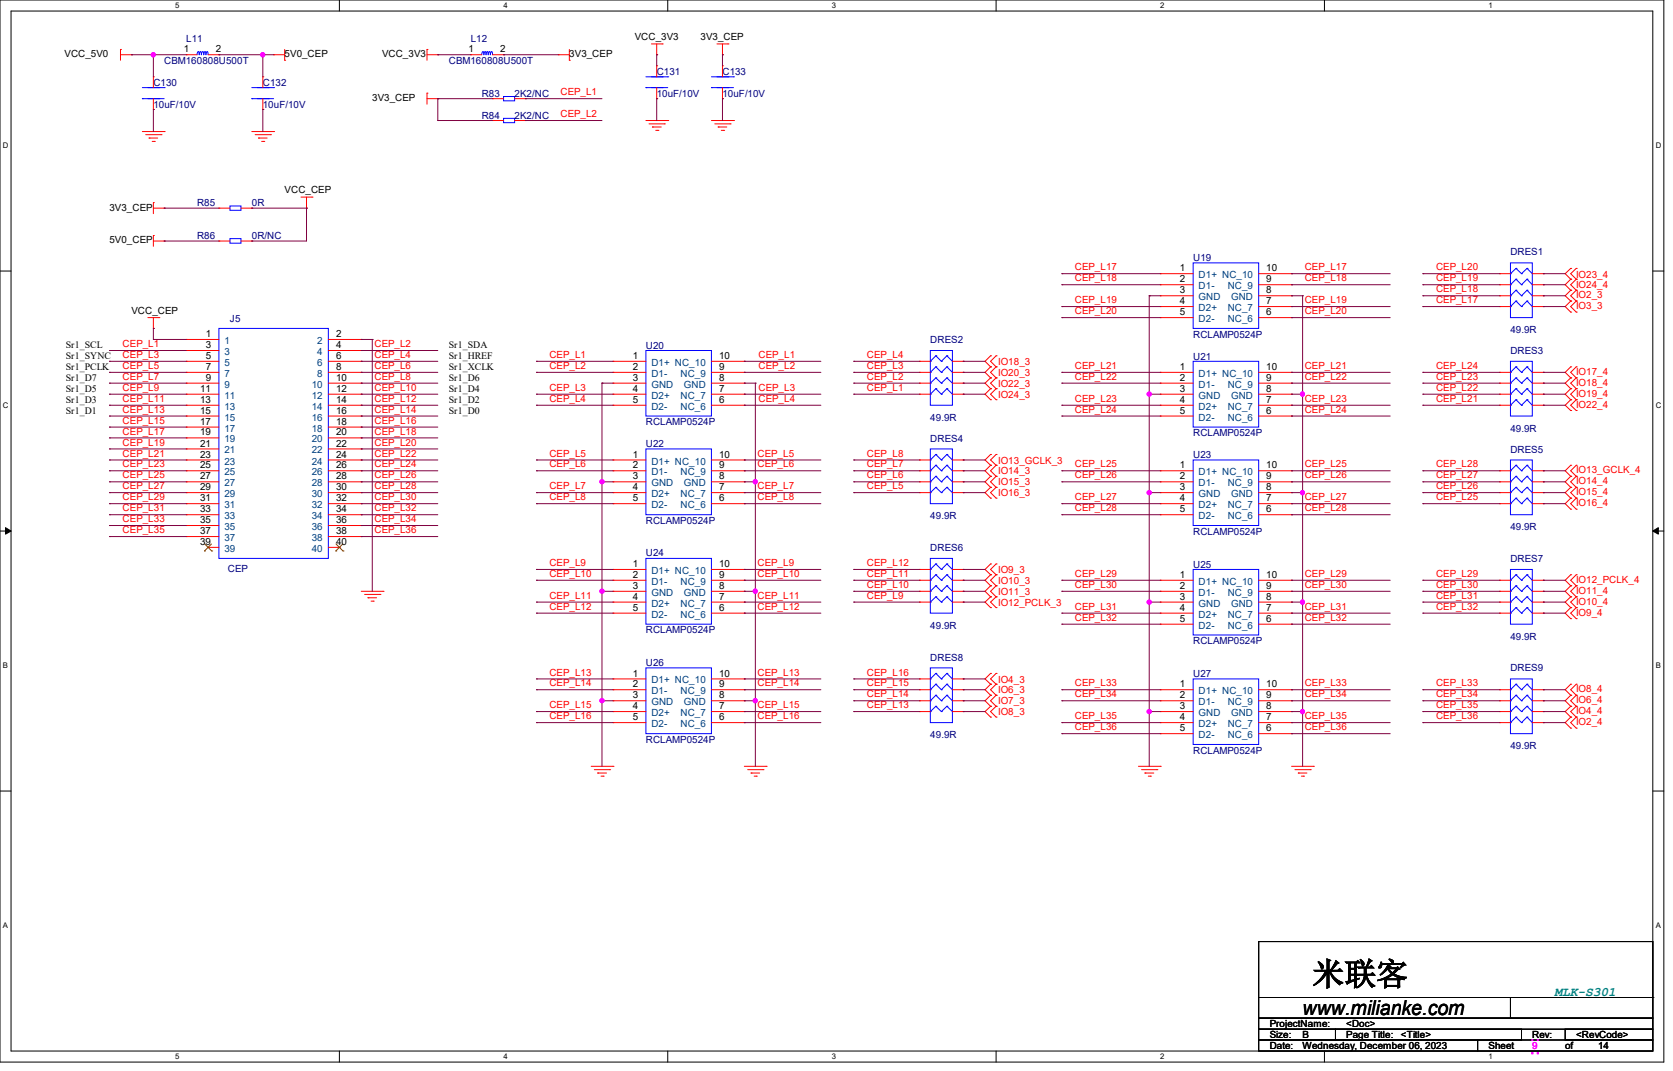
[picture p47: page 9]

VCC_5V0 | BL_VDD

## IO13_1

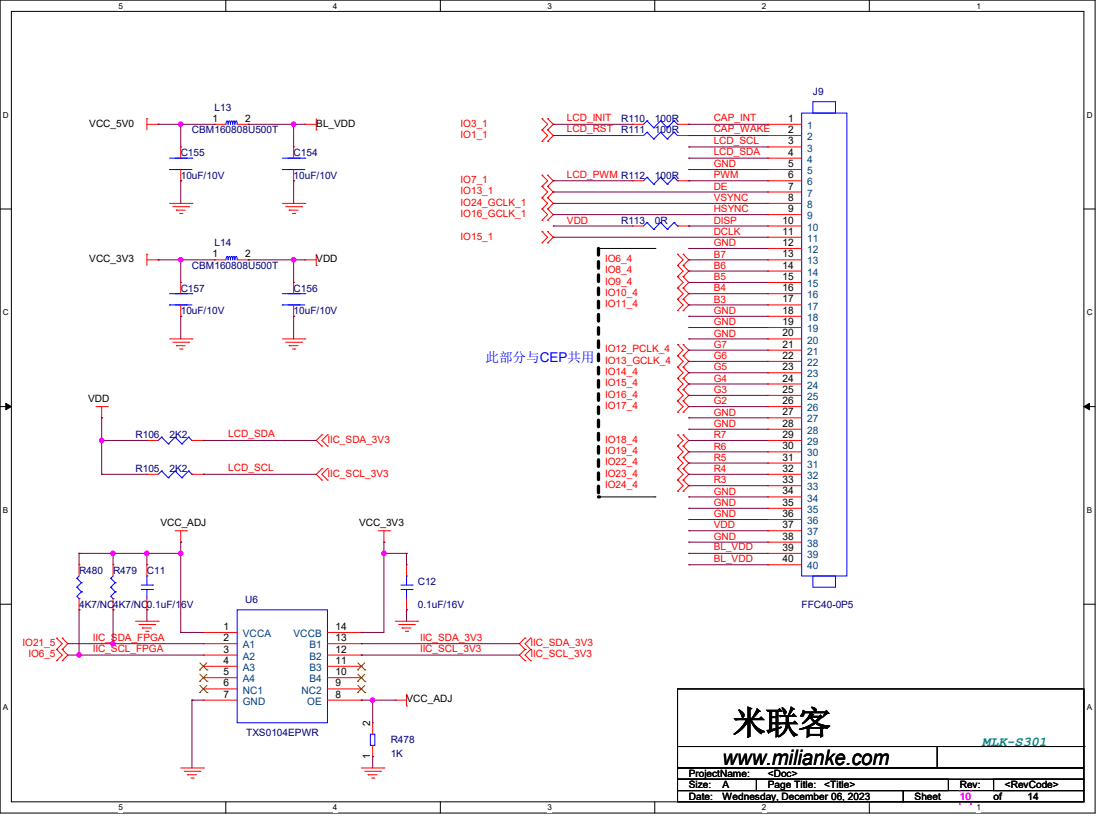
[picture p48: page 10]

## VCC_3V3 VCC_3V3

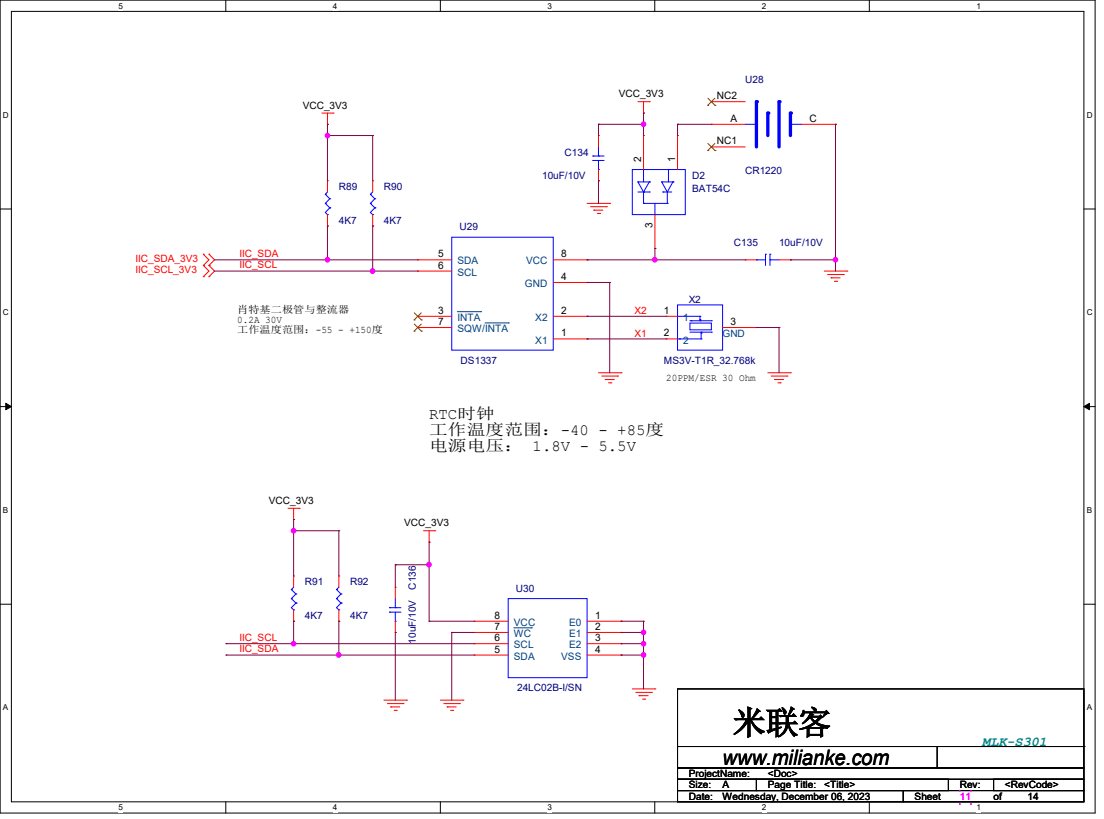
[picture p49: page 11]

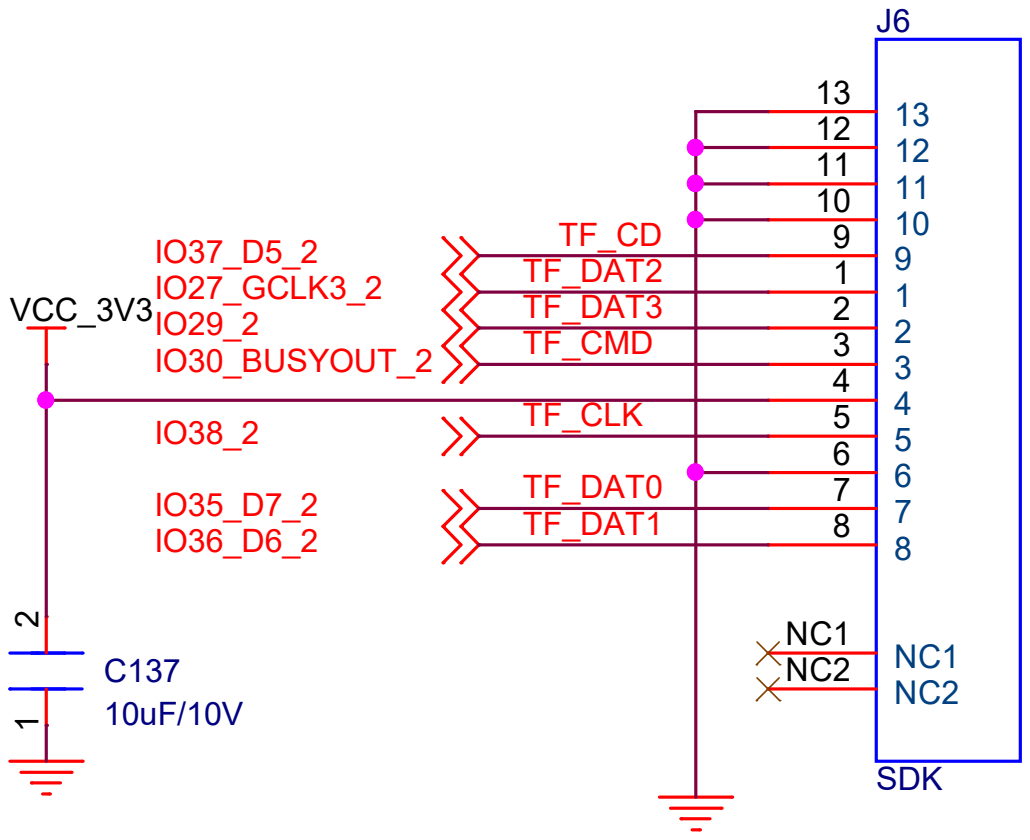
[picture p50: page 12]
MLK-S301; VCC_3V3IO27_GCLK3_2 IO29_2 IO30_BUSYOUT_2; Date:; Sheet Wednesday, December 06, 2023; Wednesday, December 06, 2023; SDK; TF_CD TF_DAT2 TF_DAT3 TF_CMD; TF_CLK; TF_DAT0 TF_DAT1

米联客
www.milianke.com

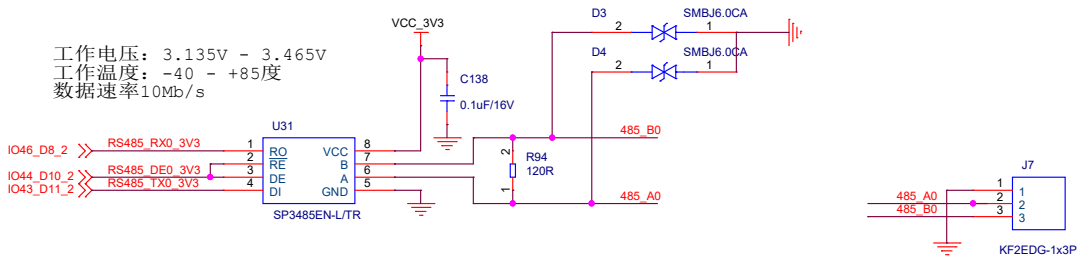
[picture p51: page 13]
工作电压：3.135V - 3.465V 工作温度：-40 - +85度 数据速率10Mb/s; MLK-S301; VCC_3V3; Date:; Sheet Wednesday, December 06, 2023; Wednesday, December 06, 2023; SMBJ6.0CA; KF2EDG-1x3P; GND 5 A; 7 VCC 8

米联客
www.milianke.com

## f g b

e

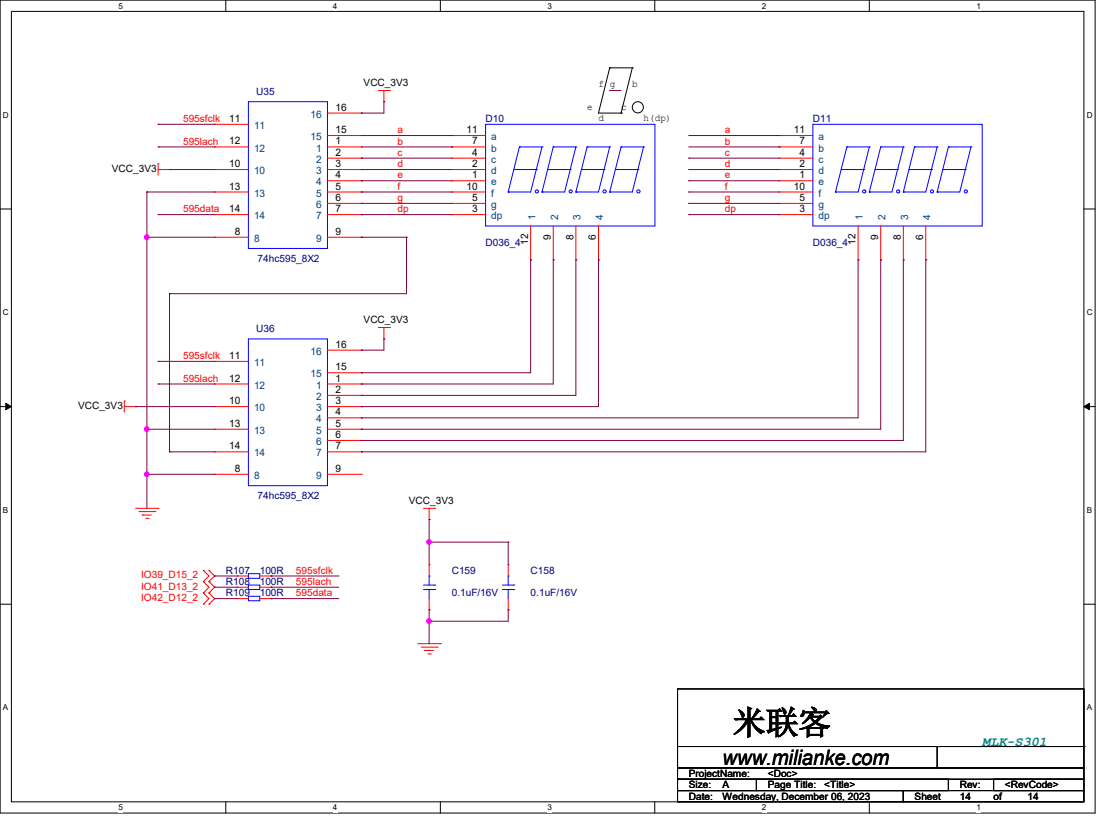
[picture p52: page 14]
