vllogic/dalishen_pi_h7p20/docs/reference_schs/ataradov.usb-sniffer.pdf

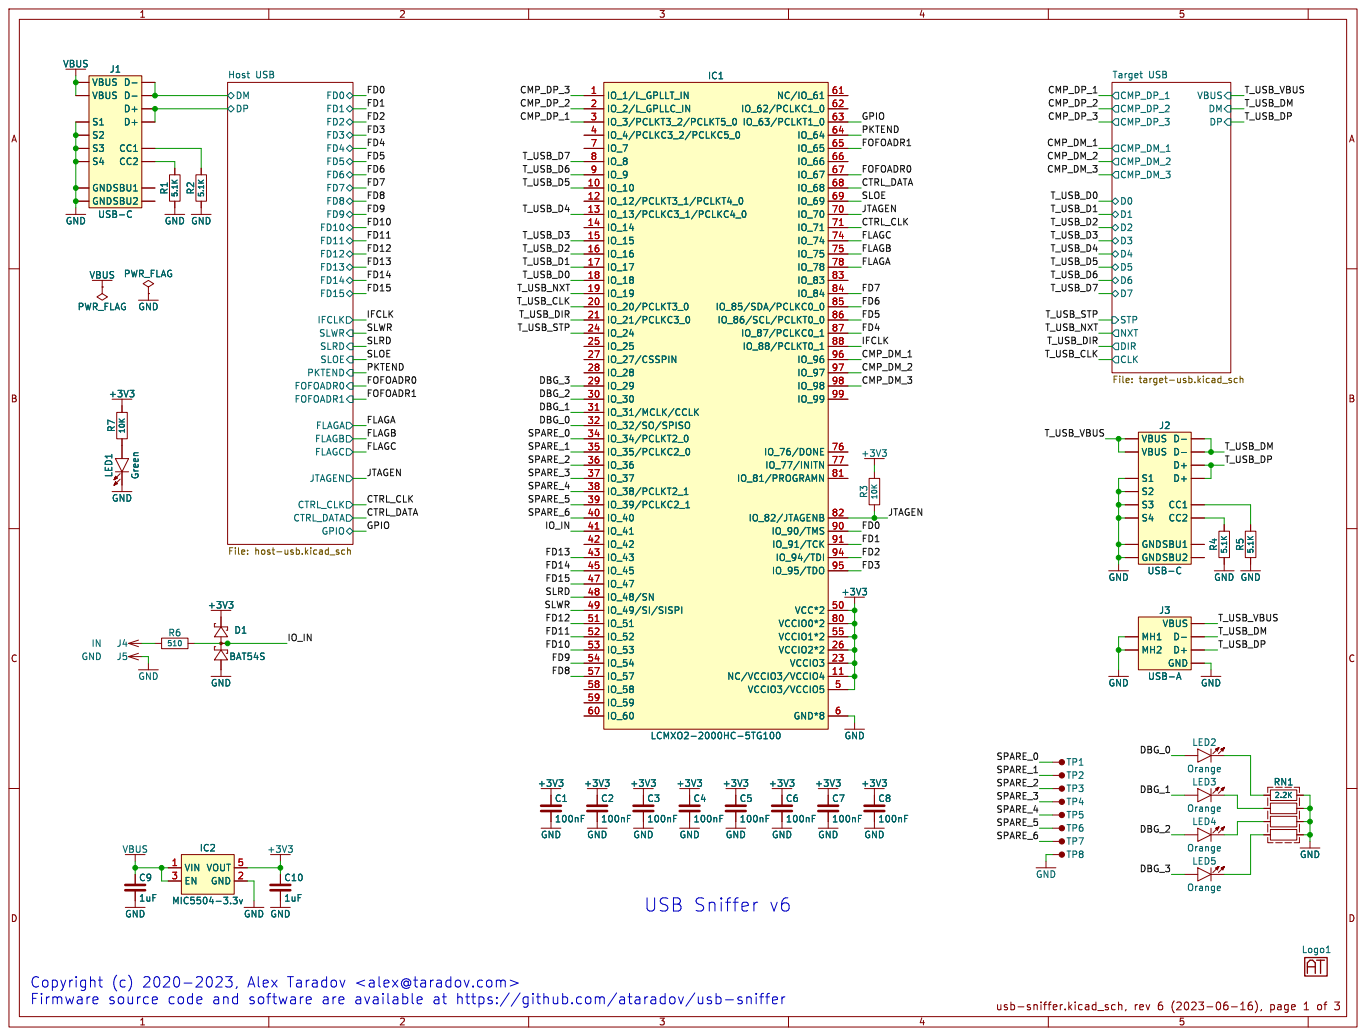
[picture p58: page 1]

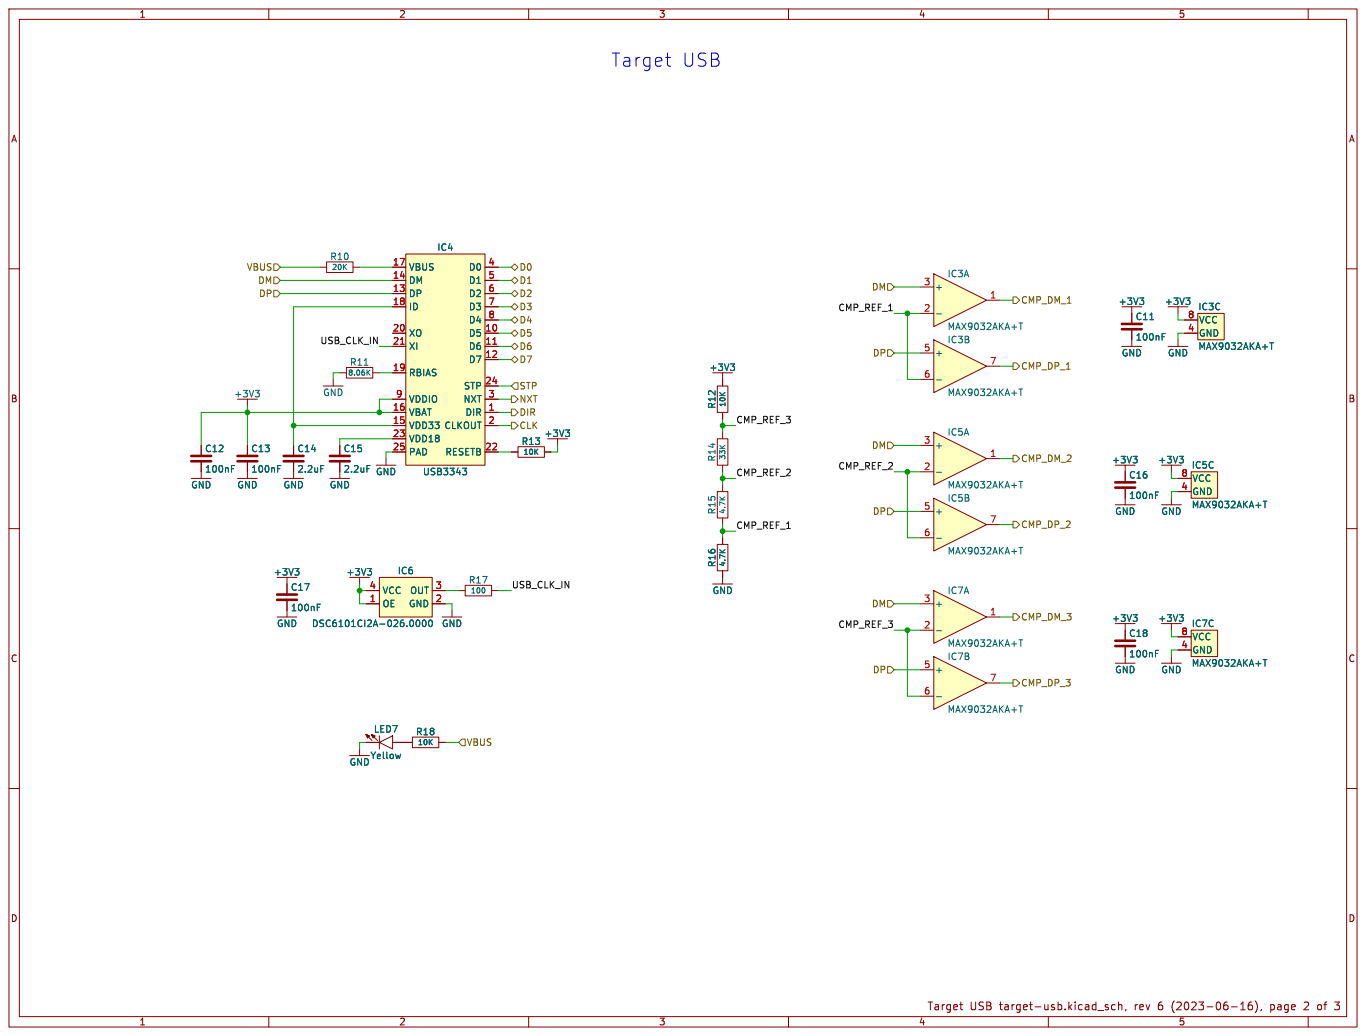
[picture p59: page 2]

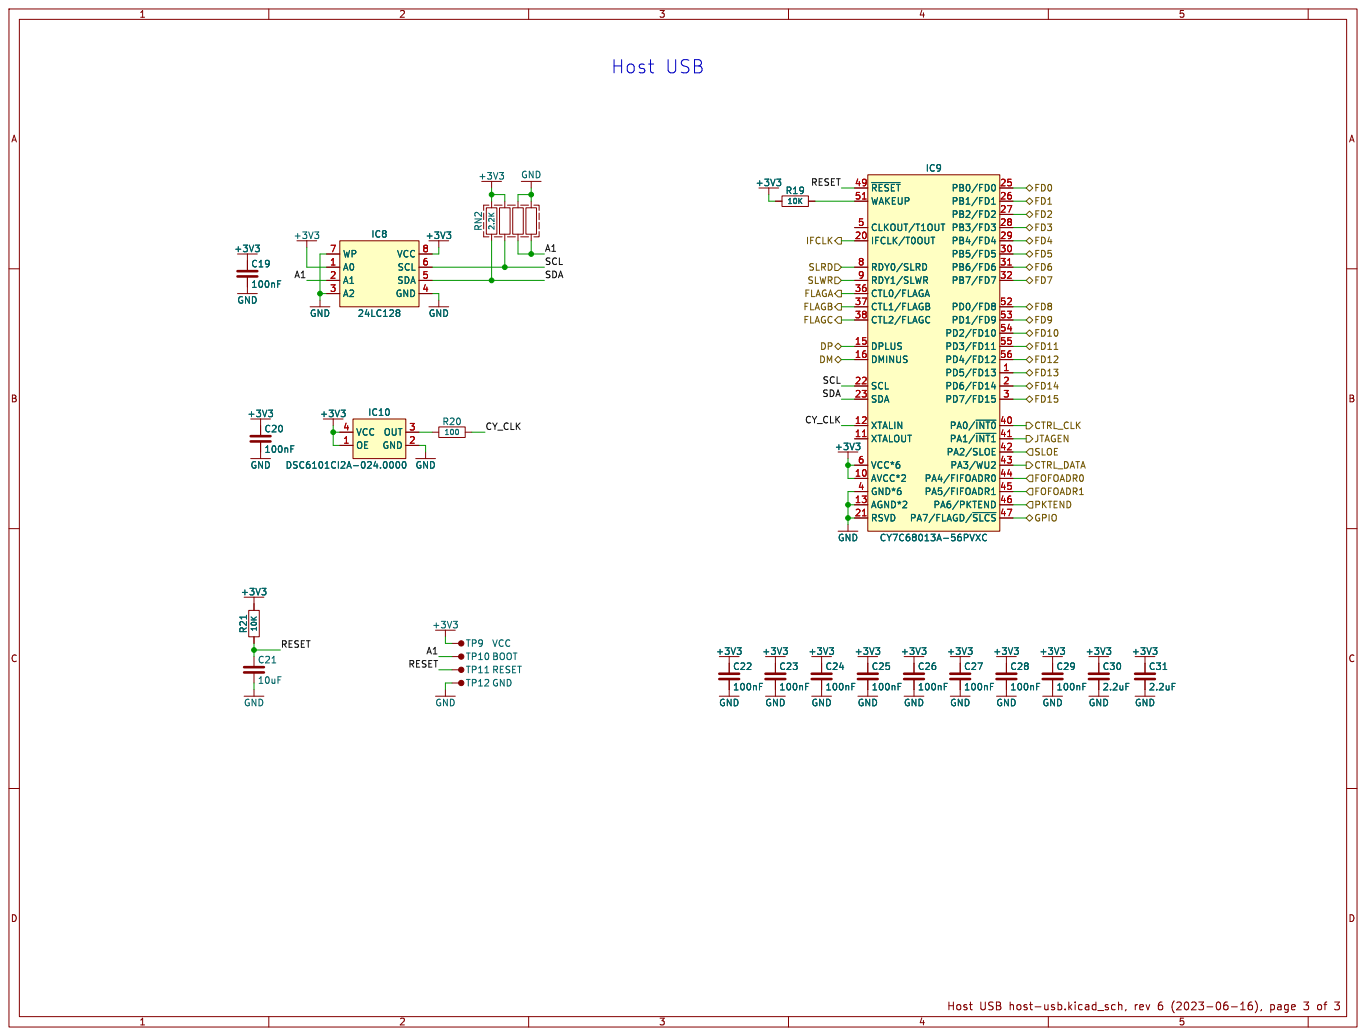
[picture p60: page 3]
