vllogic/dalishen_pi_h7p20/hardware/usb_sniffer_h7p20/production_files.2025620/usb_sniffer_h7p20.pdf

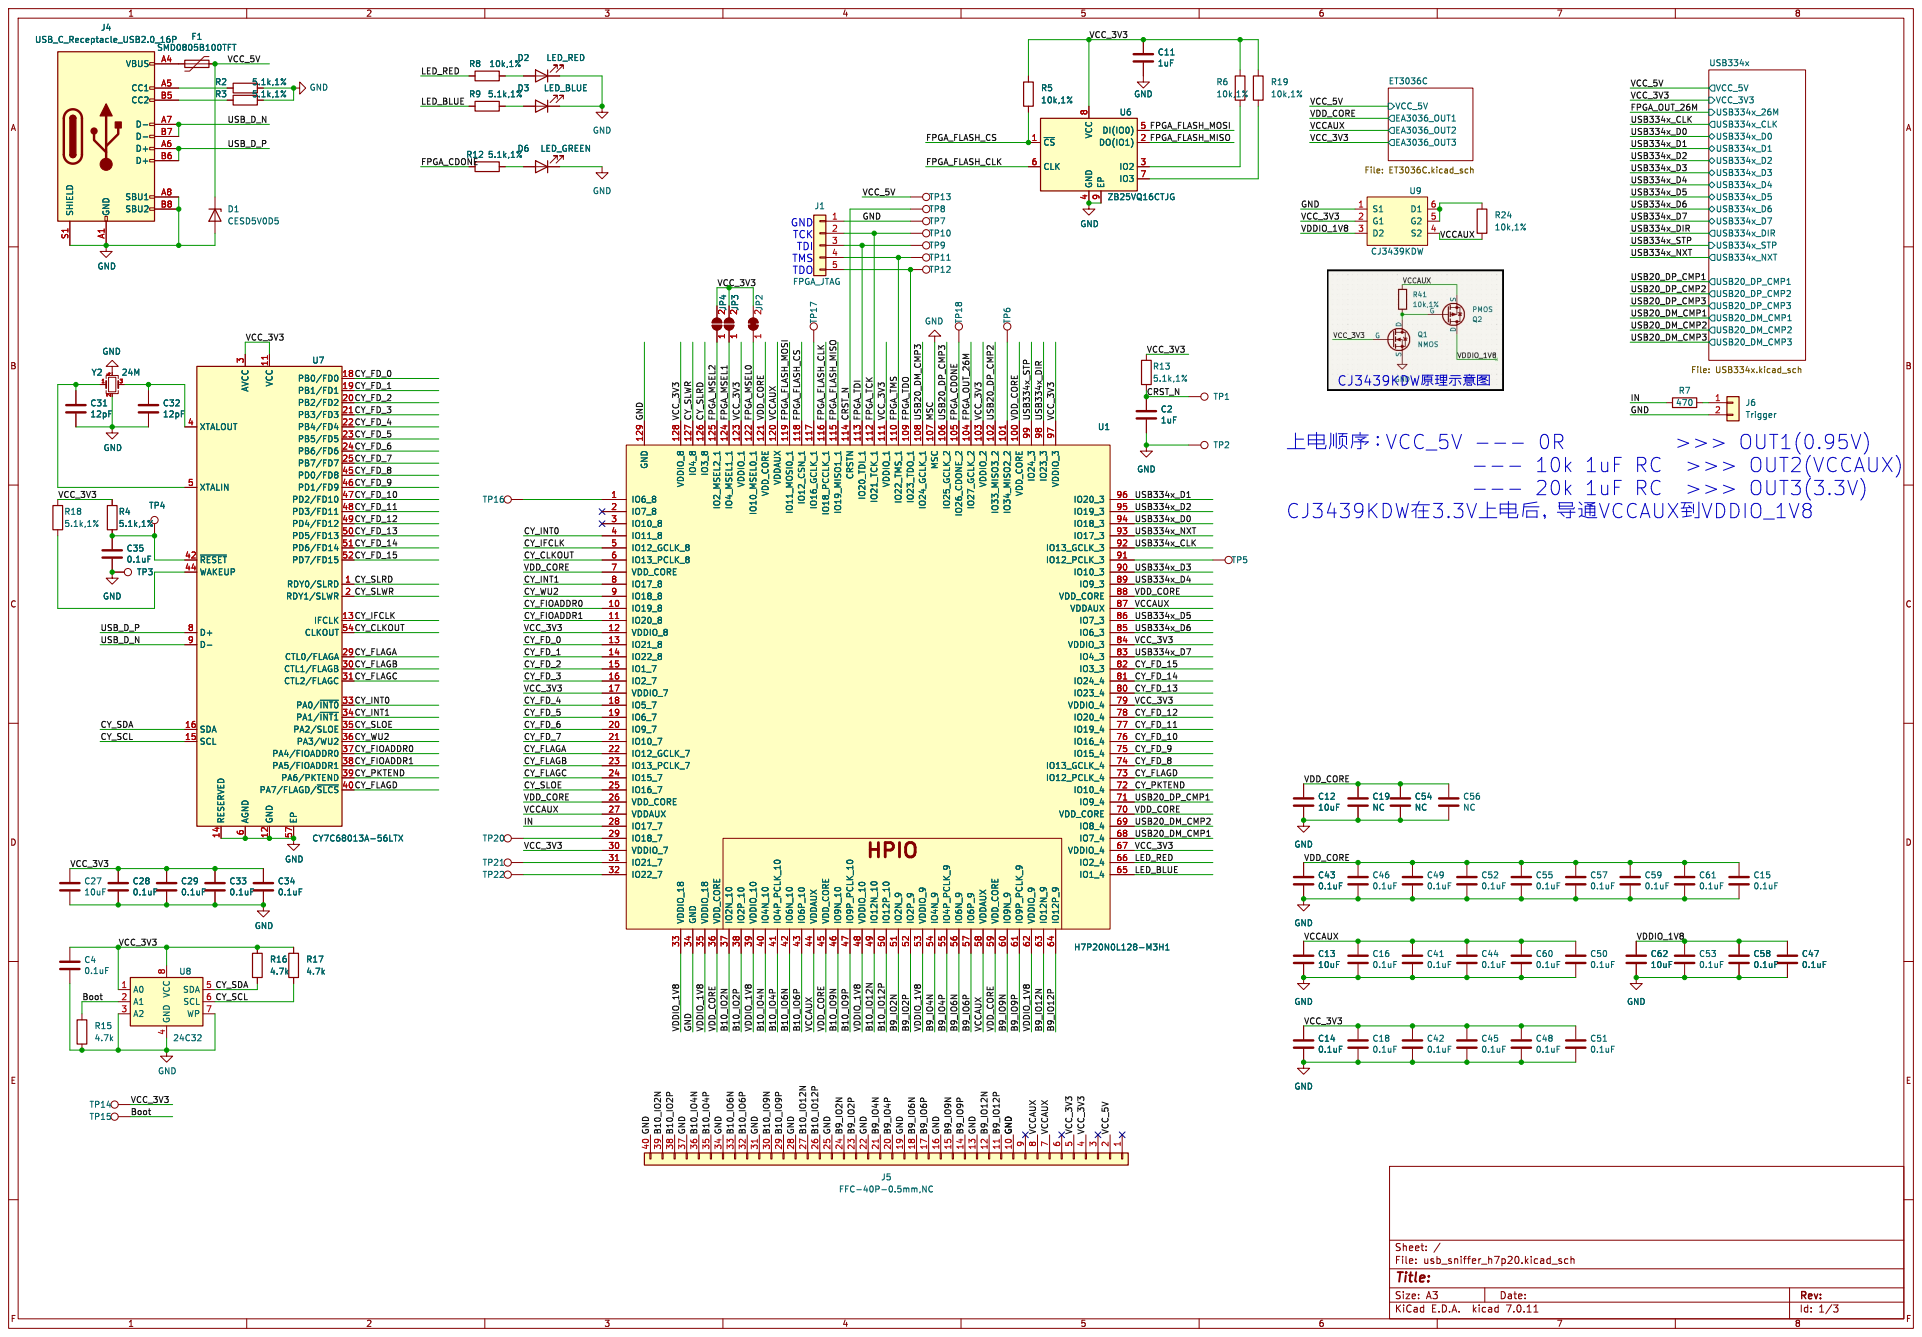
[picture p61: page 1]

3 CTL1/FLAGB 30 CTL2/FLAGC 31 PA0/~{INT0}33 PA1/~{INT1}34 PA2/SLOE 35 PA3/WU2 36 PA4/FIOADDR0 37 PA5/FIOADDR1 38 PA6/PKTEND 39 XTALOUT 4 PA7/FLAGD/~{SLCS} 40 ~{RESET} 42 WAKEUP 44 PD0/FD8 45 PD1/FD9 46 PD2/FD10 47 PD3/FD11 48 PD4/FD12 49 XTALIN 5 PD5/FD13 50 PD6/FD14 51 PD7/FD15 52 CLKOUT 54 EP 57 AGND

4 SDA 5 SCL 6 WP 7 VCC

Id: 1/3 Title: File: usb_sniffer_h7p20.kicad_sch Sheet: /

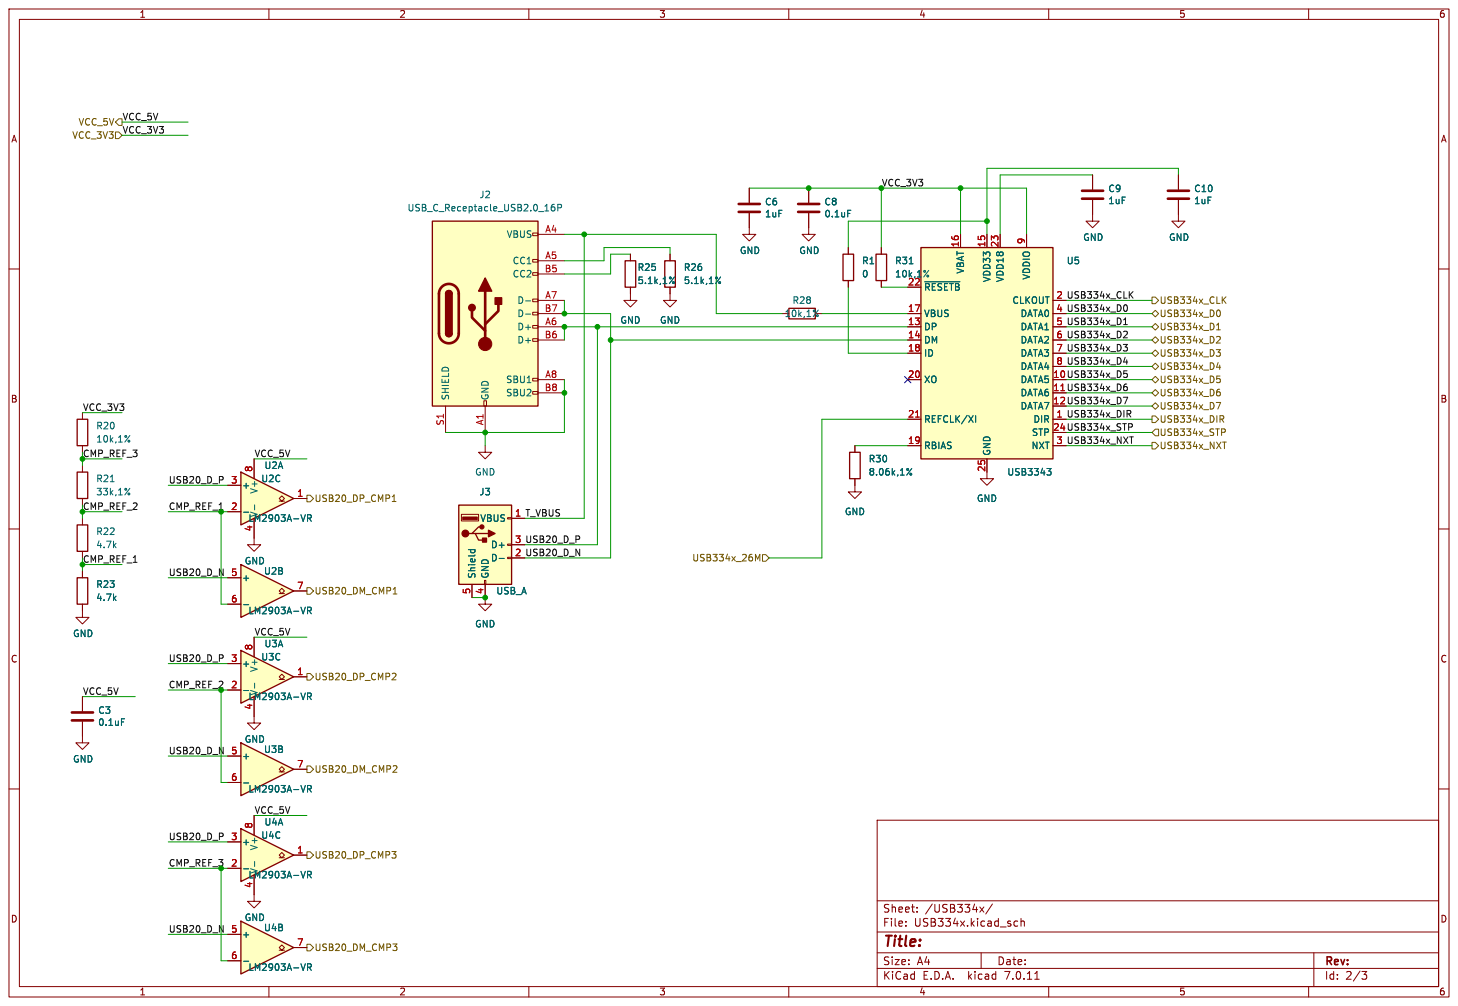
[picture p62: page 2]

Id: 2/3 Title: File: USB334x.kicad_sch Sheet: /USB334x/ R30

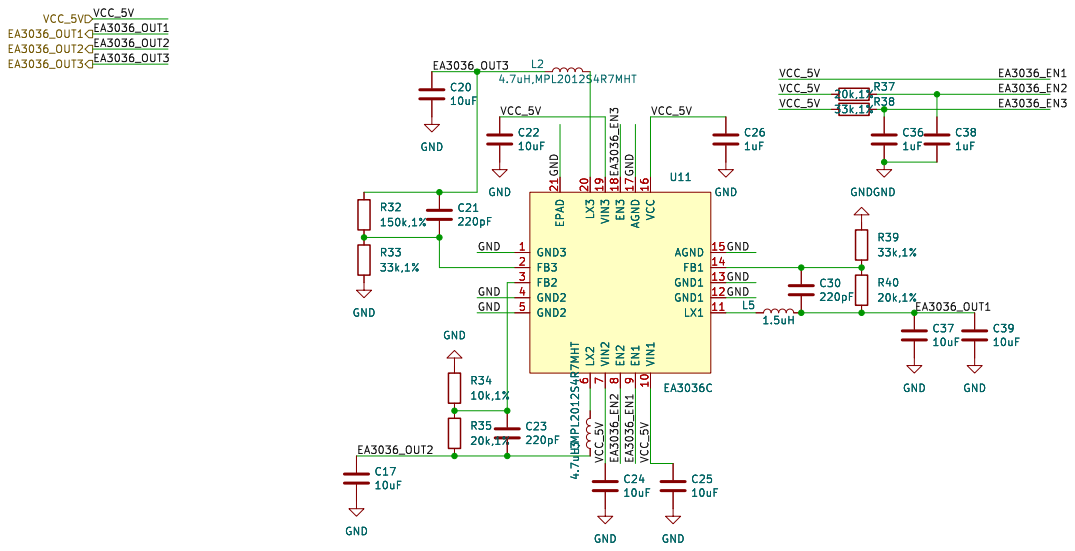
[picture p63: page 3]

Id: 3/3 Title: File: ET3036C.kicad_sch Sheet: /ET3036C/ GND
