vllogic/dalishen_pi_h7p20/examples/dalishen_pi_h7p20.arm_rgmii/fpga/ip_core/ethernet_mac_v3/src/P0_P2/hme_ip_eth_mac_top_ahb_f_1k_v3.v

//================================================================================
// Copyright (c) 2013 Capital-micro, Inc.(Beijing)  All rights reserved.
//
// Capital-micro, Inc.(Beijing) Confidential.
//
// No part of this code may be reproduced, distributed, transmitted,
// transcribed, stored in a retrieval system, or translated into any
// human or computer language, in any form or by any means, electronic,
// mechanical, magnetic, manual, or otherwise, without the express
// written permission of Capital-micro, Inc.
//
//================================================================================
// Module Description: Top Module of Ethernet MAC IP core
//================================================================================
// Revision History :
//     V1.0   2013-03-18  FPGA IP Grp, first created
//     V2.0   2014-04-25  FPGA IP Grp, support EMIF/AHB bus, modify TX/RX
//     memory management 
//     V3.0   2014-12-18  FPGA IP Grp, add eth_mac_core_f_1k.v to support
//     1000M mode
//================================================================================
module hme_ip_eth_mac_top_ahb_f_1k_v3 (
    clk_tx_i,
    clk_rx_i,
    clk_app_i,
    rst_clk_tx_n,
    rst_clk_rx_n,
    rst_clk_app_n,
    
	gmii_mdc_o,
    gmii_mdi_i,
    gmii_mdo_o,
    gmii_mdo_o_e,
    phy_txen_o,
    phy_txer_o,
    phy_txd_o,
    phy_crs_i,
    phy_col_i,
    phy_rxdv_i,
    phy_rxer_i,
    phy_rxd_i,
//----- interface to directly access internal data path -----
    tx_valid_i,
    tx_data_i,
    tx_start_i,
    tx_end_i,
    tx_bytesel_i,
    tx_ready_o,
    tx_status_o,
    tx_status_valid_o,
    rx_valid_o,
    rx_data_o,
    rx_start_o,
    rx_end_o,
    rx_bytesel_o,
    rx_status_o,   
//-------------------------- end ----------------------------	
    s_ahb_sel,
    s_ahb_addr,
    s_ahb_write,
    s_ahb_trans,
    s_ahb_wdata,
    s_ahb_readyout,
    s_ahb_rdata,	

	irq
);

parameter BASE_ADDR = 32'ha000_0000;
parameter DATA_ACCESS_USE_MCU = 1; 
//---------------------------------------------------------------
// system interface
//---------------------------------------------------------------
input                  clk_tx_i;              // GMII/MII transmit reference
                                              // from PHY (2.5/25/125)Mhz.
input                  clk_rx_i;              // GMII/MII receive clock 
                                              // from PHY (2.5/25/125)Mhz.
input                  rst_clk_tx_n;          // Active Low reset synch to clk_tx_i.
input                  rst_clk_rx_n;          // Active Low reset synchronous to clk_rx_i.
input                  clk_app_i;             // clock for user application
input                  rst_clk_app_n;         // Active low reset for user application
//---------------------------------------------------------------
// MII Management Interface.
//---------------------------------------------------------------
output           gmii_mdc_o;       // GMII/MII management clock.
input            gmii_mdi_i;       // GMII/MII mgmt data input. 
output           gmii_mdo_o;       // GMII/MII mgmt data output.
output           gmii_mdo_o_e;     // GMII/MII mgmt data o/p enable.

//---------------------------------------------------------------
// Transmit PHY Interface.
//---------------------------------------------------------------
output           phy_txen_o;        // Transmit data Enable - GMII/MII, 
output           phy_txer_o;        // Transmit Error - GMII.
output [7:0]     phy_txd_o;         // Transmit Data[7:0] - GMII
                                    // Transmit Data[3:0] - MII.
//---------------------------------------------------------------
// PHY Receive Interface 
//---------------------------------------------------------------
input            phy_rxdv_i;        // Receive data valid signal - GMII/MII.
input            phy_rxer_i;        // Receive error-GMII/MII.
input  [7:0]     phy_rxd_i;         // Receive Data [7:0] in GMII.
                                    // Receive Data [3:0] in MII.
input            phy_crs_i;         // Carrier Sense in GMII/MII
input            phy_col_i;         // Collision Detect in GMII/MII.

//---------------------------------------------------------------
// Interface for directly accessing data path
//---------------------------------------------------------------
input            tx_valid_i;
input  [31:0]    tx_data_i;
input            tx_start_i;
input            tx_end_i;
input  [1:0]     tx_bytesel_i;
output           tx_ready_o;
output [7:0]     tx_status_o;
output           tx_status_valid_o;
output           rx_valid_o;
output [31:0]    rx_data_o;
output           rx_start_o;
output           rx_end_o;
output [1:0]     rx_bytesel_o;
output [7:0]     rx_status_o;

//---------------------------------------------------------------
// ARM Cortex-M3 AHB Bus
//---------------------------------------------------------------
input         s_ahb_sel;
input  [31:0] s_ahb_addr;
input         s_ahb_write;
input  [1:0]  s_ahb_trans;
input  [31:0] s_ahb_wdata;
output        s_ahb_readyout;
output [31:0] s_ahb_rdata;
output        irq;

`pragma protect begin_protected
`pragma protect version=4
`pragma protect vendor="Hercules Microelectronics"
`pragma protect email="supports@hercules-micro.com"
`pragma protect data_method="AES128-CBC"
`pragma protect data_encode="Base64"
`pragma protect key_method="RSA"
`pragma protect key_encode="Base64"
`pragma protect data_line_size=96
`pragma protect key_block
cLKDOzILQ/y7Xm1Ot833DGev2X5hbfdXtTh89L2TNZjmVfRWuZQ049VTaKKVTSw7NfQZdjL96+M3ttZ2/LueWtBbwjtERh2EvFO0Lv+O3Xhgqlt6AY7eu6XsHIWZ3YmQCQHEUNVQSeApMk8PhfB1pM1miy7c6PslTHh2e3+OoIc=
`pragma protect data_block
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
`pragma protect end_protected
endmodule
