vllogic/dalishen_pi_h7p20/examples/dalishen_pi_h7p20.arm_rgmii/fpga/ip_core/ethernet_mac_v3/src/P0_P2/hme_ip_ahb2mci_ahb_v3.v

//================================================================================
// Copyright (c) 2013 Capital-micro, Inc.(Beijing)  All rights reserved.
//
// Capital-micro, Inc.(Beijing) Confidential.
//
// No part of this code may be reproduced, distributed, transmitted,
// transcribed, stored in a retrieval system, or translated into any
// human or computer language, in any form or by any means, electronic,
// mechanical, magnetic, manual, or otherwise, without the express
// written permission of Capital-micro, Inc.
//
//================================================================================
// Module Description: 
// This is address mapping module for Ethernet MAC IP control interface
// 1. Address mapping for MAC control interface(MCI)
// 2. Address mapping for MAC transmit/receive memory access (Optional)
// 3. Address mapping for MAC transmit/receive memory control (Optional)
//================================================================================
// Revision History :
//     V1.0   2013-03-18  FPGA IP Grp, first created
//     V2.0   2014-04-25  FPGA IP Grp, support EMIF/AHB bus, modify TX/RX
//     memory management   
//     V3.0   2014-12-18  FPGA IP Grp, add eth_mac_core_f_1k.v to support
//     1000M mode
//================================================================================

module hme_ip_ahb2mci_ahb_v3 (
   clk_app_i,
   rst_clk_app_n,
	
   fp0_s_ahb_sel,
   fp0_s_ahb_addr,
   fp0_s_ahb_write,
   fp0_s_ahb_trans,
   fp0_s_ahb_wdata,
   fp0_s_ahb_readyout,
   fp0_s_ahb_rdata,

   irq,            //interrupt
   // MAC Control Interface(MCI)
   mci_val_o,
   mci_addr_o,
   mci_rdwrn_o,
   mci_wdata_o,
   mci_be_o,
   mci_ack_i,
   mci_rdata_i,
   mci_intr_i,
   
   //interface with tr_mem_ctrl      
   rx_len,
   rx_stat,

   clr_rx_mem_empty_stat,
   rx_mem_rd_data,
   rx_mem_rd_ack,
   tx_stat,
   tx_stat_val_i,
   

   tx_mem_0_clr,
   tx_mem_1_clr,

   mci_ctrl,
   tx_mem_wr,
   tx_mem_wr_addr,
   tx_mem_wr_data,
   
   rcv_new_frame_en_rx,
   rcv_new_frame_en_clr_app,
   rx_mem_rd,
   rx_mem_rd_addr,
   frame_rd_over_en_pedge
);

`pragma protect begin_protected
`pragma protect version=4
`pragma protect vendor="Hercules Microelectronics"
`pragma protect email="supports@hercules-micro.com"
`pragma protect data_method="AES128-CBC"
`pragma protect data_encode="Base64"
`pragma protect key_method="RSA"
`pragma protect key_encode="Base64"
`pragma protect data_line_size=96
`pragma protect key_block
C6aFK2zKQeXwDCX2qf2ZjU/7YrGHyvMzm9DNW1Nh0x+Y+FSps+S5Z0bQy6HvABMh5epxuDJVaxc6OUEcl+WH008rVqeslRKB7/lvkQjRreS6uVPLKzUaHnvlG1EfSP5af/Azg4tOUYcDhh3xVQuPYr608u4a97Xp7nZ8y2K9gNw=
`pragma protect data_block
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
`pragma protect end_protected

endmodule
