vllogic/dalishen_pi_h7p20/examples/dalishen_pi_h7p20.arm_rgmii/fpga/ip_core/ethernet_mac_v3/src/eth_mac_core_f.v

//protect_encode_begin
`pragma protect begin_protected
`pragma protect version=1
`pragma protect data_block
ajgefg!EX`NPEFM`NJTTBNQMFT
!!!avoefg!EX`NPEFM`NJTTBNQMFT
afoejg
ajgefg!VTF`EQSBN`NPEFM
!!!avoefg!VTF`EQSBN`NPEFM
afoejg
ajgefg!VTF`EXNN
!!!avoefg!VTF`EXNN
afoejg
ajgefg!DPEFDPW
!!!avoefg!DPEFDPW
afoejg
ajgefg!SDF`TJN
!!!avoefg!SDF`TJN
afoejg
ajgefg!VTF`GPVOEBUJPO
!!!avoefg!VTF`GPVOEBUJPO
afoejg
ajgefg!DNF`HNBD`GBTU`TJN
!!!avoefg!DNF`HNBD`GBTU`TJN
afoejg
ajgefg!HNBD
!!!avoefg!HNBD
afoejg
ajgefg!HNBD`DPSF
!!!avoefg!HNBD`DPSF
afoejg
ajgefg!HNBD`NUM`TVCTZT
!!!avoefg!HNBD`NUM`TVCTZT
afoejg
ajgefg!HNBD`BIC`TVCTZT
!!!avoefg!HNBD`BIC`TVCTZT
afoejg
ajgefg!HNBD`ENB`TVCTZT
!!!avoefg!HNBD`ENB`TVCTZT
afoejg
ajgefg!HNBD`BYJ`TVCTZT
!!!avoefg!HNBD`BYJ`TVCTZT
afoejg
ajgefg!EBUBXJEUI
!!!avoefg!EBUBXJEUI
afoejg
ajgefg!EBUBXJEUI`43
!!!avoefg!EBUBXJEUI`43
afoejg
ajgefg!EBUBXJEUI`75
!!!avoefg!EBUBXJEUI`75
afoejg
ajgefg!EBUBXJEUI`239
!!!avoefg!EBUBXJEUI`239
afoejg
ajgefg!FOEJBO`OFTT
!!!avoefg!FOEJBO`OFTT
afoejg
ajgefg!EBUB`FOEJBO`OFTT`CPUI
!!!avoefg!EBUB`FOEJBO`OFTT`CPUI
afoejg
ajgefg!EBUB`FOEJBO`OFTT`IJ
!!!avoefg!EBUB`FOEJBO`OFTT`IJ
afoejg
ajgefg!FOEJBO`MP
!!!avoefg!FOEJBO`MP
afoejg
ajgefg!FOEJBO`IJ
!!!avoefg!FOEJBO`IJ
afoejg
ajgefg!BYJ`FOEJBO`IJ
!!!avoefg!BYJ`FOEJBO`IJ
afoejg
ajgefg!BYJ`FOEJBO`MP
!!!avoefg!BYJ`FOEJBO`MP
afoejg
ajgefg!BIC`FOEJBO`IJ
!!!avoefg!BIC`FOEJBO`IJ
afoejg
ajgefg!BIC`FOEJBO`MP
!!!avoefg!BIC`FOEJBO`MP
afoejg
ajgefg!NED`FOEJBO`IJ
!!!avoefg!NED`FOEJBO`IJ
afoejg
ajgefg!NED`FOEJBO`MP
!!!avoefg!NED`FOEJBO`MP
afoejg
ajgefg!EFTD`FOEJBO`OFTT
!!!avoefg!EFTD`FOEJBO`OFTT
afoejg
ajgefg!EFTD`FOEJBO`OFTT`CPUI
!!!avoefg!EFTD`FOEJBO`OFTT`CPUI
afoejg
ajgefg!EFTD`FOEJBO`OFTT`SFW
!!!avoefg!EFTD`FOEJBO`OFTT`SFW
afoejg
ajgefg!DTS`QPSU
!!!avoefg!DTS`QPSU
afoejg
ajgefg!BQC`TMBWF
!!!avoefg!BQC`TMBWF
afoejg
ajgefg!BIC`TMBWF
!!!avoefg!BIC`TMBWF
afoejg
ajgefg!HNBD`BYJ`TMBWF
!!!avoefg!HNBD`BYJ`TMBWF
afoejg
ajgefg!BQC4`TMBWF
!!!avoefg!BQC4`TMBWF
afoejg
ajgefg!DTS`TMW`DML
!!!avoefg!DTS`TMW`DML
afoejg
ajgefg!DTS`EBUBXJEUI
!!!avoefg!DTS`EBUBXJEUI
afoejg
ajgefg!DTS`EBUBXJEUI`43
!!!avoefg!DTS`EBUBXJEUI`43
afoejg
ajgefg!DTS`EBUBXJEUI`75
!!!avoefg!DTS`EBUBXJEUI`75
afoejg
ajgefg!DTS`EBUBXJEUI`239
!!!avoefg!DTS`EBUBXJEUI`239
afoejg
ajgefg!TCE`GD`FO
!!!avoefg!TCE`GD`FO
afoejg
ajgefg!BEE`UYSY`EJT`JP
!!!avoefg!BEE`UYSY`EJT`JP
afoejg
ajgefg!BEE`UYGJGP`GMVTI`JP
!!!avoefg!BEE`UYGJGP`GMVTI`JP
afoejg
ajgefg!HQJP`FO
!!!avoefg!HQJP`FO
afoejg
ajgefg!HJX
!!!avoefg!HJX
afoejg
ajgefg!HPX
!!!avoefg!HPX
afoejg
ajgefg!BYJ`CM
!!!avoefg!BYJ`CM
afoejg
ajgefg!CMX
!!!avoefg!CMX
afoejg
ajgefg!CM43
!!!avoefg!CM43
afoejg
ajgefg!CM75
!!!avoefg!CM75
afoejg
ajgefg!CM239
!!!avoefg!CM239
afoejg
ajgefg!CM367
!!!avoefg!CM367
afoejg
ajgefg!BYJ`HN`TUPSF`BOE`GPSXBSE
!!!avoefg!BYJ`HN`TUPSF`BOE`GPSXBSE
afoejg
ajgefg!BYJ`HN`XSJUF`JOUFSMFBWJOH
!!!avoefg!BYJ`HN`XSJUF`JOUFSMFBWJOH
afoejg
ajgefg!BYJ`HN`XSJUF`SFPSEFSJOH
!!!avoefg!BYJ`HN`XSJUF`SFPSEFSJOH
afoejg
ajgefg!PQ`NPEF
!!!avoefg!PQ`NPEF
afoejg
ajgefg!GEVQMY`POMZ
!!!avoefg!GEVQMY`POMZ
afoejg
ajgefg!N221`POMZ
!!!avoefg!N221`POMZ
afoejg
ajgefg!N2111`POMZ
!!!avoefg!N2111`POMZ
afoejg
ajgefg!VTFS`WFS
!!!avoefg!VTFS`WFS
afoejg
ajgefg!BTZOD`STU
!!!avoefg!BTZOD`STU
afoejg
ajgefg!SYGJGP`TJ[F
!!!avoefg!SYGJGP`TJ[F
afoejg
ajgefg!UYGJGP`TJ[F
!!!avoefg!UYGJGP`TJ[F
afoejg
ajgefg!NBY`GSBNF`JO`UYGJGP
!!!avoefg!NBY`GSBNF`JO`UYGJGP
afoejg
ajgefg!BTZOD`SBN
!!!avoefg!BTZOD`SBN
afoejg
ajgefg!SY`GSBNF`MFO`JG
!!!avoefg!SY`GSBNF`MFO`JG
afoejg
ajgefg!TUT`QUS`XJEUI
!!!avoefg!TUT`QUS`XJEUI
afoejg
ajgefg!NBY`GSBNF`JO`UYGJGP`3
!!!avoefg!NBY`GSBNF`JO`UYGJGP`3
afoejg
ajgefg!SY`GJGP`QUS`XJEUI
!!!avoefg!SY`GJGP`QUS`XJEUI
afoejg
ajgefg!BSJ`QCM`XJEUI
!!!avoefg!BSJ`QCM`XJEUI
afoejg
ajgefg!GJGP`EBUB`XJEUI
!!!avoefg!GJGP`EBUB`XJEUI
afoejg
ajgefg!UY`GJGP`QUS`XJEUI
!!!avoefg!UY`GJGP`QUS`XJEUI
afoejg
ajgefg!BUJ`QCM`XJEUI
!!!avoefg!BUJ`QCM`XJEUI
afoejg
ajgefg!BEES`PGGTFU`NTC
!!!avoefg!BEES`PGGTFU`NTC
afoejg
ajgefg!NJO`GSBNF`TJ[F
!!!avoefg!NJO`GSBNF`TJ[F
afoejg
ajgefg!NBY`GSBNF`DOU`XJEUI
!!!avoefg!NBY`GSBNF`DOU`XJEUI
afoejg
ajgefg!GSBNF`MFO`GJGP`XJEUI
!!!avoefg!GSBNF`MFO`GJGP`XJEUI
afoejg
ajgefg!GBTU`GMVTI`PO`BCU
!!!avoefg!GBTU`GMVTI`PO`BCU
afoejg
ajgefg!BEES`CBTF`MTC
!!!avoefg!BEES`CBTF`MTC
afoejg
ajgefg!BEES`CBTF`TJ[F
!!!avoefg!BEES`CBTF`TJ[F
afoejg
ajgefg!BEES`PGGTFU`TJ[F
!!!avoefg!BEES`PGGTFU`TJ[F
afoejg
ajgefg!EFTD`BEES`NTC
!!!avoefg!EFTD`BEES`NTC
afoejg
ajgefg!SY`CVG`TJ[F`NTC
!!!avoefg!SY`CVG`TJ[F`NTC
afoejg
ajgefg!BIC`TJ[F
!!!avoefg!BIC`TJ[F
afoejg
ajgefg!UCV`OP`PG`TUBUFT
!!!avoefg!UCV`OP`PG`TUBUFT
afoejg
ajgefg!BMM`NBD`BEES`FO
!!!avoefg!BMM`NBD`BEES`FO
afoejg
ajgefg!NBD`BEES2
!!!avoefg!NBD`BEES2
afoejg
ajgefg!NBD`BEES3
!!!avoefg!NBD`BEES3
afoejg
ajgefg!NBD`BEES4
!!!avoefg!NBD`BEES4
afoejg
ajgefg!NBD`BEES5
!!!avoefg!NBD`BEES5
afoejg
ajgefg!NBD`BEES6
!!!avoefg!NBD`BEES6
afoejg
ajgefg!NBD`BEES7
!!!avoefg!NBD`BEES7
afoejg
ajgefg!NBD`BEES8
!!!avoefg!NBD`BEES8
afoejg
ajgefg!NBD`BEES9
!!!avoefg!NBD`BEES9
afoejg
ajgefg!NBD`BEES:
!!!avoefg!NBD`BEES:
afoejg
ajgefg!NBD`BEES21
!!!avoefg!NBD`BEES21
afoejg
ajgefg!NBD`BEES22
!!!avoefg!NBD`BEES22
afoejg
ajgefg!NBD`BEES23
!!!avoefg!NBD`BEES23
afoejg
ajgefg!NBD`BEES24
!!!avoefg!NBD`BEES24
afoejg
ajgefg!NBD`BEES25
!!!avoefg!NBD`BEES25
afoejg
ajgefg!NBD`BEES26
!!!avoefg!NBD`BEES26
afoejg
ajgefg!NBD`BEES27
!!!avoefg!NBD`BEES27
afoejg
ajgefg!NBD`BEES28
!!!avoefg!NBD`BEES28
afoejg
ajgefg!NBD`BEES29
!!!avoefg!NBD`BEES29
afoejg
ajgefg!NBD`BEES2:
!!!avoefg!NBD`BEES2:
afoejg
ajgefg!NBD`BEES31
!!!avoefg!NBD`BEES31
afoejg
ajgefg!NBD`BEES32
!!!avoefg!NBD`BEES32
afoejg
ajgefg!NBD`BEES33
!!!avoefg!NBD`BEES33
afoejg
ajgefg!NBD`BEES34
!!!avoefg!NBD`BEES34
afoejg
ajgefg!NBD`BEES35
!!!avoefg!NBD`BEES35
afoejg
ajgefg!NBD`BEES36
!!!avoefg!NBD`BEES36
afoejg
ajgefg!NBD`BEES37
!!!avoefg!NBD`BEES37
afoejg
ajgefg!NBD`BEES38
!!!avoefg!NBD`BEES38
afoejg
ajgefg!NBD`BEES39
!!!avoefg!NBD`BEES39
afoejg
ajgefg!NBD`BEES3:
!!!avoefg!NBD`BEES3:
afoejg
ajgefg!NBD`BEES41
!!!avoefg!NBD`BEES41
afoejg
ajgefg!NBD`BEES42
!!!avoefg!NBD`BEES42
afoejg
ajgefg!FYUSB`NBD`BEES`SFH
!!!avoefg!FYUSB`NBD`BEES`SFH
afoejg
ajgefg!BEE43`NBD`BEES`SFH
!!!avoefg!BEE43`NBD`BEES`SFH
afoejg
ajgefg!BEE75`NBD`BEES`SFH
!!!avoefg!BEE75`NBD`BEES`SFH
afoejg
ajgefg!IBTI`EJT
!!!avoefg!IBTI`EJT
afoejg
ajgefg!DNF`HNBD`IBTI`UBCMF
!!!avoefg!DNF`HNBD`IBTI`UBCMF
afoejg
ajgefg!DNF`HNBD`IBTI`UCM`TJ[F`75
!!!avoefg!DNF`HNBD`IBTI`UCM`TJ[F`75
afoejg
ajgefg!DNF`HNBD`IBTI`UCM`TJ[F`239
!!!avoefg!DNF`HNBD`IBTI`UCM`TJ[F`239
afoejg
ajgefg!DNF`HNBD`IBTI`UCM`TJ[F`367
!!!avoefg!DNF`HNBD`IBTI`UCM`TJ[F`367
afoejg
ajgefg!DNF`HNBD`M4`M5`GJMUFS`FO
!!!avoefg!DNF`HNBD`M4`M5`GJMUFS`FO
afoejg
ajgefg!DNF`HNBD`M4`M5`GJMUFS`OVN
!!!avoefg!DNF`HNBD`M4`M5`GJMUFS`OVN
afoejg
ajgefg!DNF`HNBD`M4`M5`GJMUFS`OVN`2
!!!avoefg!DNF`HNBD`M4`M5`GJMUFS`OVN`2
afoejg
ajgefg!DNF`HNBD`M4`M5`GJMUFS`OVN`3
!!!avoefg!DNF`HNBD`M4`M5`GJMUFS`OVN`3
afoejg
ajgefg!DNF`HNBD`M4`M5`GJMUFS`OVN`4
!!!avoefg!DNF`HNBD`M4`M5`GJMUFS`OVN`4
afoejg
ajgefg!TZOD`NBDBEES
!!!avoefg!TZOD`NBDBEES
afoejg
ajgefg!TZOD`QBVTFUJNF
!!!avoefg!TZOD`QBVTFUJNF
afoejg
ajgefg!TZOD`WMBOUBH
!!!avoefg!TZOD`WMBOUBH
afoejg
ajgefg!TZOD`IBTIUBCMF
!!!avoefg!TZOD`IBTIUBCMF
afoejg
ajgefg!DNF`HNBD`TZOD`M4`M5`BEES
!!!avoefg!DNF`HNBD`TZOD`M4`M5`BEES
afoejg
ajgefg!DNF`HNBD`WMBO`IBTI`FO
!!!avoefg!DNF`HNBD`WMBO`IBTI`FO
afoejg
ajgefg!DNF`HNBD`TWB
!!!avoefg!DNF`HNBD`TWB
afoejg
ajgefg!DNF`HNBD`NED`TWB
!!!avoefg!DNF`HNBD`NED`TWB
afoejg
ajgefg!DNF`HNBD`BYJ`TWB
!!!avoefg!DNF`HNBD`BYJ`TWB
afoejg
ajgefg!DNF`HNBD`NUM`TWB
!!!avoefg!DNF`HNBD`NUM`TWB
afoejg
ajgefg!SFH`ENB`JOUG
!!!avoefg!SFH`ENB`JOUG
afoejg
ajgefg!SGD`GEFQUI
!!!avoefg!SGD`GEFQUI
afoejg
ajgefg!SGD`GQUSXJEUI
!!!avoefg!SGD`GQUSXJEUI
afoejg
ajgefg!SHNJJ`FO
!!!avoefg!SHNJJ`FO
afoejg
ajgefg!SNJJ`FO
!!!avoefg!SNJJ`FO
afoejg
ajgefg!TNJJ`FO
!!!avoefg!TNJJ`FO
afoejg
ajgefg!SFWNJJ`FO
!!!avoefg!SFWNJJ`FO
afoejg
ajgefg!THNJJ`FO
!!!avoefg!THNJJ`FO
afoejg
ajgefg!UCJ`FO
!!!avoefg!UCJ`FO
afoejg
ajgefg!SUCJ`FO
!!!avoefg!SUCJ`FO
afoejg
ajgefg!SHNJJ`PS`THNJJ
!!!avoefg!SHNJJ`PS`THNJJ
afoejg
ajgefg!SHNJJ`PS`SUCJ
!!!avoefg!SHNJJ`PS`SUCJ
afoejg
ajgefg!SHNJJ`THNJJ`FO
!!!avoefg!SHNJJ`THNJJ`FO
afoejg
ajgefg!QDT`FO
!!!avoefg!QDT`FO
afoejg
ajgefg!UCJ`THNJJ`FO
!!!avoefg!UCJ`THNJJ`FO
afoejg
ajgefg!YMOY`3W
!!!avoefg!YMOY`3W
afoejg
ajgefg!HNBD`QIZ`EFMBZ
!!!avoefg!HNBD`QIZ`EFMBZ
afoejg
ajgefg!SHNJJ`EFMBZ
!!!avoefg!SHNJJ`EFMBZ
afoejg
ajgefg!SUCJ`EFMBZ
!!!avoefg!SUCJ`EFMBZ
afoejg
ajgefg!TJOHMF`QIZ`JOUG
!!!avoefg!TJOHMF`QIZ`JOUG
afoejg
ajgefg!TTTNJJ`FO
!!!avoefg!TTTNJJ`FO
afoejg
ajgefg!TTTNJJ`UYTZOD`JO
!!!avoefg!TTTNJJ`UYTZOD`JO
afoejg
ajgefg!SHNJJ`JOUG`POMZ
!!!avoefg!SHNJJ`JOUG`POMZ
afoejg
ajgefg!THNJJ`JOUG`POMZ
!!!avoefg!THNJJ`JOUG`POMZ
afoejg
ajgefg!SNJJ`JOUG`POMZ
!!!avoefg!SNJJ`JOUG`POMZ
afoejg
ajgefg!TNJJ`JOUG`POMZ
!!!avoefg!TNJJ`JOUG`POMZ
afoejg
ajgefg!SFWNJJ`JOUG`POMZ
!!!avoefg!SFWNJJ`JOUG`POMZ
afoejg
ajgefg!UCJ`JOUG`POMZ
!!!avoefg!UCJ`JOUG`POMZ
afoejg
ajgefg!SUCJ`JOUG`POMZ
!!!avoefg!SUCJ`JOUG`POMZ
afoejg
ajgefg!HNJJ`JOUG`POMZ
!!!avoefg!HNJJ`JOUG`POMZ
afoejg
ajgefg!TQFFE`TFMFDU
!!!avoefg!TQFFE`TFMFDU
afoejg
ajgefg!FFF`FO
!!!avoefg!FFF`FO
afoejg
ajgefg!BW`FOBCMF
!!!avoefg!BW`FOBCMF
afoejg
ajgefg!BW`UY`DIBOOFM
!!!avoefg!BW`UY`DIBOOFM
afoejg
ajgefg!BW`SY`DIBOOFM
!!!avoefg!BW`SY`DIBOOFM
afoejg
ajgefg!BW`UY`DIBOOFM`2`FO
!!!avoefg!BW`UY`DIBOOFM`2`FO
afoejg
ajgefg!BW`UY`DIBOOFM`3`FO
!!!avoefg!BW`UY`DIBOOFM`3`FO
afoejg
ajgefg!BW`SY`DIBOOFM`2`FO
!!!avoefg!BW`SY`DIBOOFM`2`FO
afoejg
ajgefg!BW`SY`DIBOOFM`3`FO
!!!avoefg!BW`SY`DIBOOFM`3`FO
afoejg
ajgefg!BW`TMPU`FO
!!!avoefg!BW`TMPU`FO
afoejg
ajgefg!BYJ`HN`BYJ`JE`XJEUI
!!!avoefg!BYJ`HN`BYJ`JE`XJEUI
afoejg
ajgefg!HT`JE
!!!avoefg!HT`JE
afoejg
ajgefg!BYJ`HN`NBY`SE`SFRVFTUT
!!!avoefg!BYJ`HN`NBY`SE`SFRVFTUT
afoejg
ajgefg!BYJ`HN`NBY`XS`SFRVFTUT
!!!avoefg!BYJ`HN`NBY`XS`SFRVFTUT
afoejg
ajgefg!UJNF`TUBNQJOH
!!!avoefg!UJNF`TUBNQJOH
afoejg
ajgefg!FYU`UJNF`TUBNQJOH
!!!avoefg!FYU`UJNF`TUBNQJOH
afoejg
ajgefg!DPBSTF`GJOF`DPSSFDUJPO
!!!avoefg!DPBSTF`GJOF`DPSSFDUJPO
afoejg
ajgefg!BEW`UJNF`TUBNQJOH
!!!avoefg!BEW`UJNF`TUBNQJOH
afoejg
ajgefg!BEW`UJNF`IJHI`XPSE
!!!avoefg!BEW`UJNF`IJHI`XPSE
afoejg
ajgefg!BEW`UJNF`BVY`TOBQ
!!!avoefg!BEW`UJNF`BVY`TOBQ
afoejg
ajgefg!DNF`HNBD`BVY`TOBQ`JO`OVN
!!!avoefg!DNF`HNBD`BVY`TOBQ`JO`OVN
afoejg
ajgefg!DNF`HNBD`BVY`TOBQ`2`FO
!!!avoefg!DNF`HNBD`BVY`TOBQ`2`FO
afoejg
ajgefg!DNF`HNBD`BVY`TOBQ`3`FO
!!!avoefg!DNF`HNBD`BVY`TOBQ`3`FO
afoejg
ajgefg!DNF`HNBD`BVY`TOBQ`4`FO
!!!avoefg!DNF`HNBD`BVY`TOBQ`4`FO
afoejg
ajgefg!DNF`HNBD`BVY`GJGP`EFQUI
!!!avoefg!DNF`HNBD`BVY`GJGP`EFQUI
afoejg
ajgefg!GMFYJ`QQT`PVU`FO
!!!avoefg!GMFYJ`QQT`PVU`FO
afoejg
ajgefg!DNF`HNBD`QQT`PVU`OVN
!!!avoefg!DNF`HNBD`QQT`PVU`OVN
afoejg
ajgefg!DNF`HNBD`QQT`PVU`2`FO
!!!avoefg!DNF`HNBD`QQT`PVU`2`FO
afoejg
ajgefg!DNF`HNBD`QQT`PVU`3`FO
!!!avoefg!DNF`HNBD`QQT`PVU`3`FO
afoejg
ajgefg!DNF`HNBD`QQT`PVU`4`FO
!!!avoefg!DNF`HNBD`QQT`PVU`4`FO
afoejg
ajgefg!EFTD`FOIBODFE`GPSNBU
!!!avoefg!EFTD`FOIBODFE`GPSNBU
afoejg
ajgefg!DNF`HNBD`TB`WMBO`DSD`DUSM`FO
!!!avoefg!DNF`HNBD`TB`WMBO`DSD`DUSM`FO
afoejg
ajgefg!JQDILTVN`FO
!!!avoefg!JQDILTVN`FO
afoejg
ajgefg!JQD`GVMM`PGGMPBE
!!!avoefg!JQD`GVMM`PGGMPBE
afoejg
ajgefg!FYUFOEFE`TUBUVT
!!!avoefg!FYUFOEFE`TUBUVT
afoejg
ajgefg!UY`DPF
!!!avoefg!UY`DPF
afoejg
ajgefg!DILTVN`GJGP`XJEUI
!!!avoefg!DILTVN`GJGP`XJEUI
afoejg
ajgefg!DILTVN`QUS`XJEUI
!!!avoefg!DILTVN`QUS`XJEUI
afoejg
ajgefg!NND`FO
!!!avoefg!NND`FO
afoejg
ajgefg!NND`FO`UY`BMM
!!!avoefg!NND`FO`UY`BMM
afoejg
ajgefg!NND`UYBEES`SOH`DOU`FO
!!!avoefg!NND`UYBEES`SOH`DOU`FO
afoejg
ajgefg!NND`UYBEES`SOH`DOU`27CJU`FO
!!!avoefg!NND`UYBEES`SOH`DOU`27CJU`FO
afoejg
ajgefg!NND`UYPDUHC`DOU`FO
!!!avoefg!NND`UYPDUHC`DOU`FO
afoejg
ajgefg!NND`UYPDUHC`DOU`27CJU`FO
!!!avoefg!NND`UYPDUHC`DOU`27CJU`FO
afoejg
ajgefg!NND`UYGSNHC`DOU`FO
!!!avoefg!NND`UYGSNHC`DOU`FO
afoejg
ajgefg!NND`UYGSNHC`DOU`27CJU`FO
!!!avoefg!NND`UYGSNHC`DOU`27CJU`FO
afoejg
ajgefg!NND`UYCDBTUH`DOU`FO
!!!avoefg!NND`UYCDBTUH`DOU`FO
afoejg
ajgefg!NND`UYCDBTUH`DOU`27CJU`FO
!!!avoefg!NND`UYCDBTUH`DOU`27CJU`FO
afoejg
ajgefg!NND`UYNDBTUH`DOU`FO
!!!avoefg!NND`UYNDBTUH`DOU`FO
afoejg
ajgefg!NND`UYNDBTUH`DOU`27CJU`FO
!!!avoefg!NND`UYNDBTUH`DOU`27CJU`FO
afoejg
ajgefg!NND`UYVDBTUHC`DOU`FO
!!!avoefg!NND`UYVDBTUHC`DOU`FO
afoejg
ajgefg!NND`UYVDBTUHC`DOU`27CJU`FO
!!!avoefg!NND`UYVDBTUHC`DOU`27CJU`FO
afoejg
ajgefg!NND`UYNDBTUHC`DOU`FO
!!!avoefg!NND`UYNDBTUHC`DOU`FO
afoejg
ajgefg!NND`UYNDBTUHC`DOU`27CJU`FO
!!!avoefg!NND`UYNDBTUHC`DOU`27CJU`FO
afoejg
ajgefg!NND`UYCDBTUHC`DOU`FO
!!!avoefg!NND`UYCDBTUHC`DOU`FO
afoejg
ajgefg!NND`UYCDBTUHC`DOU`27CJU`FO
!!!avoefg!NND`UYCDBTUHC`DOU`27CJU`FO
afoejg
ajgefg!NND`UYVOESGMX`DOU`FO
!!!avoefg!NND`UYVOESGMX`DOU`FO
afoejg
ajgefg!NND`UYVOESGMX`DOU`27CJU`FO
!!!avoefg!NND`UYVOESGMX`DOU`27CJU`FO
afoejg
ajgefg!NND`UYTOHMDPMH`DOU`FO
!!!avoefg!NND`UYTOHMDPMH`DOU`FO
afoejg
ajgefg!NND`UYTOHMDPMH`DOU`27CJU`FO
!!!avoefg!NND`UYTOHMDPMH`DOU`27CJU`FO
afoejg
ajgefg!NND`UYNVMUDPMH`DOU`FO
!!!avoefg!NND`UYNVMUDPMH`DOU`FO
afoejg
ajgefg!NND`UYNVMUDPMH`DOU`27CJU`FO
!!!avoefg!NND`UYNVMUDPMH`DOU`27CJU`FO
afoejg
ajgefg!NND`UYEFGSE`DOU`FO
!!!avoefg!NND`UYEFGSE`DOU`FO
afoejg
ajgefg!NND`UYEFGSE`DOU`27CJU`FO
!!!avoefg!NND`UYEFGSE`DOU`27CJU`FO
afoejg
ajgefg!NND`UYMBUFDPM`DOU`FO
!!!avoefg!NND`UYMBUFDPM`DOU`FO
afoejg
ajgefg!NND`UYMBUFDPM`DOU`27CJU`FO
!!!avoefg!NND`UYMBUFDPM`DOU`27CJU`FO
afoejg
ajgefg!NND`UYFYTDPM`DOU`FO
!!!avoefg!NND`UYFYTDPM`DOU`FO
afoejg
ajgefg!NND`UYFYTDPM`DOU`27CJU`FO
!!!avoefg!NND`UYFYTDPM`DOU`27CJU`FO
afoejg
ajgefg!NND`UYDBSS`DOU`FO
!!!avoefg!NND`UYDBSS`DOU`FO
afoejg
ajgefg!NND`UYDBSS`DOU`27CJU`FO
!!!avoefg!NND`UYDBSS`DOU`27CJU`FO
afoejg
ajgefg!NND`UYPDUH`DOU`FO
!!!avoefg!NND`UYPDUH`DOU`FO
afoejg
ajgefg!NND`UYPDUH`DOU`27CJU`FO
!!!avoefg!NND`UYPDUH`DOU`27CJU`FO
afoejg
ajgefg!NND`UYGSNH`DOU`FO
!!!avoefg!NND`UYGSNH`DOU`FO
afoejg
ajgefg!NND`UYGSNH`DOU`27CJU`FO
!!!avoefg!NND`UYGSNH`DOU`27CJU`FO
afoejg
ajgefg!NND`UYFYTEFG`DOU`FO
!!!avoefg!NND`UYFYTEFG`DOU`FO
afoejg
ajgefg!NND`UYFYTEFG`DOU`27CJU`FO
!!!avoefg!NND`UYFYTEFG`DOU`27CJU`FO
afoejg
ajgefg!NND`UYQBVTF`DOU`FO
!!!avoefg!NND`UYQBVTF`DOU`FO
afoejg
ajgefg!NND`UYQBVTF`DOU`27CJU`FO
!!!avoefg!NND`UYQBVTF`DOU`27CJU`FO
afoejg
ajgefg!NND`UYWMBO`DOU`FO
!!!avoefg!NND`UYWMBO`DOU`FO
afoejg
ajgefg!NND`UYWMBO`DOU`27CJU`FO
!!!avoefg!NND`UYWMBO`DOU`27CJU`FO
afoejg
ajgefg!DNF`HNBD`NND`UYPWFST[H`DOU`FO
!!!avoefg!DNF`HNBD`NND`UYPWFST[H`DOU`FO
afoejg
ajgefg!DNF`HNBD`NND`UYPWFST[H`DOU`27CJU`FO
!!!avoefg!DNF`HNBD`NND`UYPWFST[H`DOU`27CJU`FO
afoejg
ajgefg!NND`UY`FO`BUMFBTU`POF
!!!avoefg!NND`UY`FO`BUMFBTU`POF
afoejg
ajgefg!NND`FO`SY`BMM
!!!avoefg!NND`FO`SY`BMM
afoejg
ajgefg!NND`SYGSNHC`DOU`FO
!!!avoefg!NND`SYGSNHC`DOU`FO
afoejg
ajgefg!NND`SYGSNHC`DOU`27CJU`FO
!!!avoefg!NND`SYGSNHC`DOU`27CJU`FO
afoejg
ajgefg!NND`SYPDUH`DOU`FO
!!!avoefg!NND`SYPDUH`DOU`FO
afoejg
ajgefg!NND`SYPDUH`DOU`27CJU`FO
!!!avoefg!NND`SYPDUH`DOU`27CJU`FO
afoejg
ajgefg!NND`SYPDUHC`DOU`FO
!!!avoefg!NND`SYPDUHC`DOU`FO
afoejg
ajgefg!NND`SYPDUHC`DOU`27CJU`FO
!!!avoefg!NND`SYPDUHC`DOU`27CJU`FO
afoejg
ajgefg!NND`SYCDBTUH`DOU`FO
!!!avoefg!NND`SYCDBTUH`DOU`FO
afoejg
ajgefg!NND`SYCDBTUH`DOU`27CJU`FO
!!!avoefg!NND`SYCDBTUH`DOU`27CJU`FO
afoejg
ajgefg!NND`SYNDBTUH`DOU`FO
!!!avoefg!NND`SYNDBTUH`DOU`FO
afoejg
ajgefg!NND`SYNDBTUH`DOU`27CJU`FO
!!!avoefg!NND`SYNDBTUH`DOU`27CJU`FO
afoejg
ajgefg!NND`SYDSDFSS`DOU`FO
!!!avoefg!NND`SYDSDFSS`DOU`FO
afoejg
ajgefg!NND`SYDSDFSS`DOU`27CJU`FO
!!!avoefg!NND`SYDSDFSS`DOU`27CJU`FO
afoejg
ajgefg!NND`SYBMHOFSS`DOU`FO
!!!avoefg!NND`SYBMHOFSS`DOU`FO
afoejg
ajgefg!NND`SYBMHOFSS`DOU`27CJU`FO
!!!avoefg!NND`SYBMHOFSS`DOU`27CJU`FO
afoejg
ajgefg!NND`SYSVOUFSS`DOU`FO
!!!avoefg!NND`SYSVOUFSS`DOU`FO
afoejg
ajgefg!NND`SYSVOUFSS`DOU`27CJU`FO
!!!avoefg!NND`SYSVOUFSS`DOU`27CJU`FO
afoejg
ajgefg!NND`SYKBCFSS`DOU`FO
!!!avoefg!NND`SYKBCFSS`DOU`FO
afoejg
ajgefg!NND`SYKBCFSS`DOU`27CJU`FO
!!!avoefg!NND`SYKBCFSS`DOU`27CJU`FO
afoejg
ajgefg!NND`SYVOEFST[H`DOU`FO
!!!avoefg!NND`SYVOEFST[H`DOU`FO
afoejg
ajgefg!NND`SYVOEFST[H`DOU`27CJU`FO
!!!avoefg!NND`SYVOEFST[H`DOU`27CJU`FO
afoejg
ajgefg!NND`SYPWFST[H`DOU`FO
!!!avoefg!NND`SYPWFST[H`DOU`FO
afoejg
ajgefg!NND`SYPWFST[H`DOU`27CJU`FO
!!!avoefg!NND`SYPWFST[H`DOU`27CJU`FO
afoejg
ajgefg!NND`SYBEES`SOH`DOU`FO
!!!avoefg!NND`SYBEES`SOH`DOU`FO
afoejg
ajgefg!NND`SYBEES`SOH`DOU`27CJU`FO
!!!avoefg!NND`SYBEES`SOH`DOU`27CJU`FO
afoejg
ajgefg!NND`SYVDBTUH`DOU`FO
!!!avoefg!NND`SYVDBTUH`DOU`FO
afoejg
ajgefg!NND`SYVDBTUH`DOU`27CJU`FO
!!!avoefg!NND`SYVDBTUH`DOU`27CJU`FO
afoejg
ajgefg!NND`SYMFOFSS`DOU`FO
!!!avoefg!NND`SYMFOFSS`DOU`FO
afoejg
ajgefg!NND`SYMFOFSS`DOU`27CJU`FO
!!!avoefg!NND`SYMFOFSS`DOU`27CJU`FO
afoejg
ajgefg!NND`SYPVUPGSOH`UZQ`DOU`FO
!!!avoefg!NND`SYPVUPGSOH`UZQ`DOU`FO
afoejg
ajgefg!NND`SYPVUPGSOH`UZQ`DOU`27CJU`FO
!!!avoefg!NND`SYPVUPGSOH`UZQ`DOU`27CJU`FO
afoejg
ajgefg!NND`SYQBVTFGSN`DOU`FO
!!!avoefg!NND`SYQBVTFGSN`DOU`FO
afoejg
ajgefg!NND`SYQBVTFGSN`DOU`27CJU`FO
!!!avoefg!NND`SYQBVTFGSN`DOU`27CJU`FO
afoejg
ajgefg!NND`SYGJGPPWGM`DOU`FO
!!!avoefg!NND`SYGJGPPWGM`DOU`FO
afoejg
ajgefg!NND`SYGJGPPWGM`DOU`27CJU`FO
!!!avoefg!NND`SYGJGPPWGM`DOU`27CJU`FO
afoejg
ajgefg!NND`SYWMBOGSHC`DOU`FO
!!!avoefg!NND`SYWMBOGSHC`DOU`FO
afoejg
ajgefg!NND`SYWMBOGSHC`DOU`27CJU`FO
!!!avoefg!NND`SYWMBOGSHC`DOU`27CJU`FO
afoejg
ajgefg!NND`SYXEHFSS`DOU`FO
!!!avoefg!NND`SYXEHFSS`DOU`FO
afoejg
ajgefg!NND`SYXEHFSS`DOU`27CJU`FO
!!!avoefg!NND`SYXEHFSS`DOU`27CJU`FO
afoejg
ajgefg!DNF`HNBD`NND`SYSDWFSS`DOU`FO
!!!avoefg!DNF`HNBD`NND`SYSDWFSS`DOU`FO
afoejg
ajgefg!DNF`HNBD`NND`SYSDWFSS`DOU`27CJU`FO
!!!avoefg!DNF`HNBD`NND`SYSDWFSS`DOU`27CJU`FO
afoejg
ajgefg!DNF`HNBD`NND`SYDUSMGSN`DOU`FO
!!!avoefg!DNF`HNBD`NND`SYDUSMGSN`DOU`FO
afoejg
ajgefg!DNF`HNBD`NND`SYDUSMGSN`DOU`27CJU`FO
!!!avoefg!DNF`HNBD`NND`SYDUSMGSN`DOU`27CJU`FO
afoejg
ajgefg!NND`SY`FO`BUMFBTU`POF
!!!avoefg!NND`SY`FO`BUMFBTU`POF
afoejg
ajgefg!NND`JQD`FO
!!!avoefg!NND`JQD`FO
afoejg
ajgefg!NND`UYDPF`FO
!!!avoefg!NND`UYDPF`FO
afoejg
ajgefg!NND`UYDPF`FO`UY`BMM
!!!avoefg!NND`UYDPF`FO`UY`BMM
afoejg
ajgefg!NND`UY`JQW5`HE`GSNT`DOU`FO
!!!avoefg!NND`UY`JQW5`HE`GSNT`DOU`FO
afoejg
ajgefg!NND`UY`JQW5`IESFSS`GSNT`DOU`FO
!!!avoefg!NND`UY`JQW5`IESFSS`GSNT`DOU`FO
afoejg
ajgefg!NND`UY`JQW5`OPQBZ`GSNT`DOU`FO
!!!avoefg!NND`UY`JQW5`OPQBZ`GSNT`DOU`FO
afoejg
ajgefg!NND`UY`JQW7`HE`GSNT`DOU`FO
!!!avoefg!NND`UY`JQW7`HE`GSNT`DOU`FO
afoejg
ajgefg!NND`UY`JQW7`IESFSS`GSNT`DOU`FO
!!!avoefg!NND`UY`JQW7`IESFSS`GSNT`DOU`FO
afoejg
ajgefg!NND`UY`JQW7`OPQBZ`GSNT`DOU`FO
!!!avoefg!NND`UY`JQW7`OPQBZ`GSNT`DOU`FO
afoejg
ajgefg!NND`UY`VEQ`HE`GSNT`DOU`FO
!!!avoefg!NND`UY`VEQ`HE`GSNT`DOU`FO
afoejg
ajgefg!NND`UY`VEQ`FSS`GSNT`DOU`FO
!!!avoefg!NND`UY`VEQ`FSS`GSNT`DOU`FO
afoejg
ajgefg!NND`UY`UDQ`HE`GSNT`DOU`FO
!!!avoefg!NND`UY`UDQ`HE`GSNT`DOU`FO
afoejg
ajgefg!NND`UY`UDQ`FSS`GSNT`DOU`FO
!!!avoefg!NND`UY`UDQ`FSS`GSNT`DOU`FO
afoejg
ajgefg!NND`UY`JDNQ`HE`GSNT`DOU`FO
!!!avoefg!NND`UY`JDNQ`HE`GSNT`DOU`FO
afoejg
ajgefg!NND`UY`JDNQ`FSS`GSNT`DOU`FO
!!!avoefg!NND`UY`JDNQ`FSS`GSNT`DOU`FO
afoejg
ajgefg!NND`UY`JQW5`HE`PDUFU`DOU`FO
!!!avoefg!NND`UY`JQW5`HE`PDUFU`DOU`FO
afoejg
ajgefg!NND`UY`JQW5`IESFSS`PDUFU`DOU`FO
!!!avoefg!NND`UY`JQW5`IESFSS`PDUFU`DOU`FO
afoejg
ajgefg!NND`UY`JQW5`OPQBZ`PDUFU`DOU`FO
!!!avoefg!NND`UY`JQW5`OPQBZ`PDUFU`DOU`FO
afoejg
ajgefg!NND`UY`JQW7`HE`PDUFU`DOU`FO
!!!avoefg!NND`UY`JQW7`HE`PDUFU`DOU`FO
afoejg
ajgefg!NND`UY`JQW7`IESFSS`PDUFU`DOU`FO
!!!avoefg!NND`UY`JQW7`IESFSS`PDUFU`DOU`FO
afoejg
ajgefg!NND`UY`JQW7`OPQBZ`PDUFU`DOU`FO
!!!avoefg!NND`UY`JQW7`OPQBZ`PDUFU`DOU`FO
afoejg
ajgefg!NND`UY`VEQ`HE`PDUFU`DOU`FO
!!!avoefg!NND`UY`VEQ`HE`PDUFU`DOU`FO
afoejg
ajgefg!NND`UY`VEQ`FSS`PDUFU`DOU`FO
!!!avoefg!NND`UY`VEQ`FSS`PDUFU`DOU`FO
afoejg
ajgefg!NND`UY`UDQ`HE`PDUFU`DOU`FO
!!!avoefg!NND`UY`UDQ`HE`PDUFU`DOU`FO
afoejg
ajgefg!NND`UY`UDQ`FSS`PDUFU`DOU`FO
!!!avoefg!NND`UY`UDQ`FSS`PDUFU`DOU`FO
afoejg
ajgefg!NND`UY`JDNQ`HE`PDUFU`DOU`FO
!!!avoefg!NND`UY`JDNQ`HE`PDUFU`DOU`FO
afoejg
ajgefg!NND`UY`JDNQ`FSS`PDUFU`DOU`FO
!!!avoefg!NND`UY`JDNQ`FSS`PDUFU`DOU`FO
afoejg
ajgefg!NND`JQD`UY`GSNT`BUMFBTU`POF
!!!avoefg!NND`JQD`UY`GSNT`BUMFBTU`POF
afoejg
ajgefg!NND`JQD`UY`EHSBN`CDOU`BUMFBTU`POF
!!!avoefg!NND`JQD`UY`EHSBN`CDOU`BUMFBTU`POF
afoejg
ajgefg!NND`JQD`UY`QBZME`CDOU`BUMFBTU`POF
!!!avoefg!NND`JQD`UY`QBZME`CDOU`BUMFBTU`POF
afoejg
ajgefg!NND`JQD`UY`FO`BUMFBTU`POF
!!!avoefg!NND`JQD`UY`FO`BUMFBTU`POF
afoejg
ajgefg!NND`JQD`FO`SY`BMM
!!!avoefg!NND`JQD`FO`SY`BMM
afoejg
ajgefg!NND`SY`JQW5`HE`GSNT`DOU`FO
!!!avoefg!NND`SY`JQW5`HE`GSNT`DOU`FO
afoejg
ajgefg!NND`SY`JQW5`HE`GSNT`DOU`27CJU`FO
!!!avoefg!NND`SY`JQW5`HE`GSNT`DOU`27CJU`FO
afoejg
ajgefg!NND`SY`JQW5`IESFSS`GSNT`DOU`FO
!!!avoefg!NND`SY`JQW5`IESFSS`GSNT`DOU`FO
afoejg
ajgefg!NND`SY`JQW5`IESFSS`GSNT`DOU`27CJU`FO
!!!avoefg!NND`SY`JQW5`IESFSS`GSNT`DOU`27CJU`FO
afoejg
ajgefg!NND`SY`JQW5`OPQBZ`GSNT`DOU`FO
!!!avoefg!NND`SY`JQW5`OPQBZ`GSNT`DOU`FO
afoejg
ajgefg!NND`SY`JQW5`OPQBZ`GSNT`DOU`27CJU`FO
!!!avoefg!NND`SY`JQW5`OPQBZ`GSNT`DOU`27CJU`FO
afoejg
ajgefg!NND`SY`JQW5`GSBH`GSNT`DOU`FO
!!!avoefg!NND`SY`JQW5`GSBH`GSNT`DOU`FO
afoejg
ajgefg!NND`SY`JQW5`GSBH`GSNT`DOU`27CJU`FO
!!!avoefg!NND`SY`JQW5`GSBH`GSNT`DOU`27CJU`FO
afoejg
ajgefg!NND`SY`JQW5`VETCM`GSNT`DOU`FO
!!!avoefg!NND`SY`JQW5`VETCM`GSNT`DOU`FO
afoejg
ajgefg!NND`SY`JQW5`VETCM`GSNT`DOU`27CJU`FO
!!!avoefg!NND`SY`JQW5`VETCM`GSNT`DOU`27CJU`FO
afoejg
ajgefg!NND`SY`JQW7`HE`GSNT`DOU`FO
!!!avoefg!NND`SY`JQW7`HE`GSNT`DOU`FO
afoejg
ajgefg!NND`SY`JQW7`HE`GSNT`DOU`27CJU`FO
!!!avoefg!NND`SY`JQW7`HE`GSNT`DOU`27CJU`FO
afoejg
ajgefg!NND`SY`JQW7`IESFSS`GSNT`DOU`FO
!!!avoefg!NND`SY`JQW7`IESFSS`GSNT`DOU`FO
afoejg
ajgefg!NND`SY`JQW7`IESFSS`GSNT`DOU`27CJU`FO
!!!avoefg!NND`SY`JQW7`IESFSS`GSNT`DOU`27CJU`FO
afoejg
ajgefg!NND`SY`JQW7`OPQBZ`GSNT`DOU`FO
!!!avoefg!NND`SY`JQW7`OPQBZ`GSNT`DOU`FO
afoejg
ajgefg!NND`SY`JQW7`OPQBZ`GSNT`DOU`27CJU`FO
!!!avoefg!NND`SY`JQW7`OPQBZ`GSNT`DOU`27CJU`FO
afoejg
ajgefg!NND`SY`VEQ`HE`GSNT`DOU`FO
!!!avoefg!NND`SY`VEQ`HE`GSNT`DOU`FO
afoejg
ajgefg!NND`SY`VEQ`HE`GSNT`DOU`27CJU`FO
!!!avoefg!NND`SY`VEQ`HE`GSNT`DOU`27CJU`FO
afoejg
ajgefg!NND`SY`VEQ`FSS`GSNT`DOU`FO
!!!avoefg!NND`SY`VEQ`FSS`GSNT`DOU`FO
afoejg
ajgefg!NND`SY`VEQ`FSS`GSNT`DOU`27CJU`FO
!!!avoefg!NND`SY`VEQ`FSS`GSNT`DOU`27CJU`FO
afoejg
ajgefg!NND`SY`UDQ`HE`GSNT`DOU`FO
!!!avoefg!NND`SY`UDQ`HE`GSNT`DOU`FO
afoejg
ajgefg!NND`SY`UDQ`HE`GSNT`DOU`27CJU`FO
!!!avoefg!NND`SY`UDQ`HE`GSNT`DOU`27CJU`FO
afoejg
ajgefg!NND`SY`UDQ`FSS`GSNT`DOU`FO
!!!avoefg!NND`SY`UDQ`FSS`GSNT`DOU`FO
afoejg
ajgefg!NND`SY`UDQ`FSS`GSNT`DOU`27CJU`FO
!!!avoefg!NND`SY`UDQ`FSS`GSNT`DOU`27CJU`FO
afoejg
ajgefg!NND`SY`JDNQ`HE`GSNT`DOU`FO
!!!avoefg!NND`SY`JDNQ`HE`GSNT`DOU`FO
afoejg
ajgefg!NND`SY`JDNQ`HE`GSNT`DOU`27CJU`FO
!!!avoefg!NND`SY`JDNQ`HE`GSNT`DOU`27CJU`FO
afoejg
ajgefg!NND`SY`JDNQ`FSS`GSNT`DOU`FO
!!!avoefg!NND`SY`JDNQ`FSS`GSNT`DOU`FO
afoejg
ajgefg!NND`SY`JDNQ`FSS`GSNT`DOU`27CJU`FO
!!!avoefg!NND`SY`JDNQ`FSS`GSNT`DOU`27CJU`FO
afoejg
ajgefg!NND`SY`JQW5`HE`PDUFU`DOU`FO
!!!avoefg!NND`SY`JQW5`HE`PDUFU`DOU`FO
afoejg
ajgefg!NND`SY`JQW5`HE`PDUFU`DOU`27CJU`FO
!!!avoefg!NND`SY`JQW5`HE`PDUFU`DOU`27CJU`FO
afoejg
ajgefg!NND`SY`JQW5`IESFSS`PDUFU`DOU`FO
!!!avoefg!NND`SY`JQW5`IESFSS`PDUFU`DOU`FO
afoejg
ajgefg!NND`SY`JQW5`IESFSS`PDUFU`DOU`27CJU`FO
!!!avoefg!NND`SY`JQW5`IESFSS`PDUFU`DOU`27CJU`FO
afoejg
ajgefg!NND`SY`JQW5`OPQBZ`PDUFU`DOU`FO
!!!avoefg!NND`SY`JQW5`OPQBZ`PDUFU`DOU`FO
afoejg
ajgefg!NND`SY`JQW5`OPQBZ`PDUFU`DOU`27CJU`FO
!!!avoefg!NND`SY`JQW5`OPQBZ`PDUFU`DOU`27CJU`FO
afoejg
ajgefg!NND`SY`JQW5`GSBH`PDUFU`DOU`FO
!!!avoefg!NND`SY`JQW5`GSBH`PDUFU`DOU`FO
afoejg
ajgefg!NND`SY`JQW5`GSBH`PDUFU`DOU`27CJU`FO
!!!avoefg!NND`SY`JQW5`GSBH`PDUFU`DOU`27CJU`FO
afoejg
ajgefg!NND`SY`JQW5`VETCM`PDUFU`DOU`FO
!!!avoefg!NND`SY`JQW5`VETCM`PDUFU`DOU`FO
afoejg
ajgefg!NND`SY`JQW5`VETCM`PDUFU`DOU`27CJU`FO
!!!avoefg!NND`SY`JQW5`VETCM`PDUFU`DOU`27CJU`FO
afoejg
ajgefg!NND`SY`JQW7`HE`PDUFU`DOU`FO
!!!avoefg!NND`SY`JQW7`HE`PDUFU`DOU`FO
afoejg
ajgefg!NND`SY`JQW7`HE`PDUFU`DOU`27CJU`FO
!!!avoefg!NND`SY`JQW7`HE`PDUFU`DOU`27CJU`FO
afoejg
ajgefg!NND`SY`JQW7`IESFSS`PDUFU`DOU`FO
!!!avoefg!NND`SY`JQW7`IESFSS`PDUFU`DOU`FO
afoejg
ajgefg!NND`SY`JQW7`IESFSS`PDUFU`DOU`27CJU`FO
!!!avoefg!NND`SY`JQW7`IESFSS`PDUFU`DOU`27CJU`FO
afoejg
ajgefg!NND`SY`JQW7`OPQBZ`PDUFU`DOU`FO
!!!avoefg!NND`SY`JQW7`OPQBZ`PDUFU`DOU`FO
afoejg
ajgefg!NND`SY`JQW7`OPQBZ`PDUFU`DOU`27CJU`FO
!!!avoefg!NND`SY`JQW7`OPQBZ`PDUFU`DOU`27CJU`FO
afoejg
ajgefg!NND`SY`VEQ`HE`PDUFU`DOU`FO
!!!avoefg!NND`SY`VEQ`HE`PDUFU`DOU`FO
afoejg
ajgefg!NND`SY`VEQ`HE`PDUFU`DOU`27CJU`FO
!!!avoefg!NND`SY`VEQ`HE`PDUFU`DOU`27CJU`FO
afoejg
ajgefg!NND`SY`VEQ`FSS`PDUFU`DOU`FO
!!!avoefg!NND`SY`VEQ`FSS`PDUFU`DOU`FO
afoejg
ajgefg!NND`SY`VEQ`FSS`PDUFU`DOU`27CJU`FO
!!!avoefg!NND`SY`VEQ`FSS`PDUFU`DOU`27CJU`FO
afoejg
ajgefg!NND`SY`UDQ`HE`PDUFU`DOU`FO
!!!avoefg!NND`SY`UDQ`HE`PDUFU`DOU`FO
afoejg
ajgefg!NND`SY`UDQ`HE`PDUFU`DOU`27CJU`FO
!!!avoefg!NND`SY`UDQ`HE`PDUFU`DOU`27CJU`FO
afoejg
ajgefg!NND`SY`UDQ`FSS`PDUFU`DOU`FO
!!!avoefg!NND`SY`UDQ`FSS`PDUFU`DOU`FO
afoejg
ajgefg!NND`SY`UDQ`FSS`PDUFU`DOU`27CJU`FO
!!!avoefg!NND`SY`UDQ`FSS`PDUFU`DOU`27CJU`FO
afoejg
ajgefg!NND`SY`JDNQ`HE`PDUFU`DOU`FO
!!!avoefg!NND`SY`JDNQ`HE`PDUFU`DOU`FO
afoejg
ajgefg!NND`SY`JDNQ`HE`PDUFU`DOU`27CJU`FO
!!!avoefg!NND`SY`JDNQ`HE`PDUFU`DOU`27CJU`FO
afoejg
ajgefg!NND`SY`JDNQ`FSS`PDUFU`DOU`FO
!!!avoefg!NND`SY`JDNQ`FSS`PDUFU`DOU`FO
afoejg
ajgefg!NND`SY`JDNQ`FSS`PDUFU`DOU`27CJU`FO
!!!avoefg!NND`SY`JDNQ`FSS`PDUFU`DOU`27CJU`FO
afoejg
ajgefg!NND`JQD`SY`EHSBN`CDOU`BUMFBTU`POF
!!!avoefg!NND`JQD`SY`EHSBN`CDOU`BUMFBTU`POF
afoejg
ajgefg!NND`JQD`SY`QBZME`CDOU`BUMFBTU`POF
!!!avoefg!NND`JQD`SY`QBZME`CDOU`BUMFBTU`POF
afoejg
ajgefg!NND`JQD`SY`GSNT`BUMFBTU`POF
!!!avoefg!NND`JQD`SY`GSNT`BUMFBTU`POF
afoejg
ajgefg!NND`JQD`SY`FO`BUMFBTU`POF
!!!avoefg!NND`JQD`SY`FO`BUMFBTU`POF
afoejg
ajgefg!TNB`FO
!!!avoefg!TNB`FO
afoejg
ajgefg!MQ`NPEF`FO
!!!avoefg!MQ`NPEF`FO
afoejg
ajgefg!QNU`FO
!!!avoefg!QNU`FO
afoejg
ajgefg!QNU`NHL`FO
!!!avoefg!QNU`NHL`FO
afoejg
ajgefg!QNU`SXL`FO
!!!avoefg!QNU`SXL`FO
afoejg
ajgefg!TJ[F`CBTF`TJ[F
!!!avoefg!TJ[F`CBTF`TJ[F
afoejg
ajgefg!OFFEFE`CFBUT`TJ[F
!!!avoefg!OFFEFE`CFBUT`TJ[F
afoejg
ajgefg!GMUSWBMJE`EMZ
!!!avoefg!GMUSWBMJE`EMZ
afoejg
ajgefg!HOU`GSBNF`UISTIME
!!!avoefg!HOU`GSBNF`UISTIME
afoejg
ajgefg!UYE`XJEUI
!!!avoefg!UYE`XJEUI
afoejg
ajgefg!SYE`XJEUI
!!!avoefg!SYE`XJEUI
afoejg
ajgefg!UYFO`PQ
!!!avoefg!UYFO`PQ
afoejg
ajgefg!UYFS`PQ
!!!avoefg!UYFS`PQ
afoejg
ajgefg!SYEW`JQ
!!!avoefg!SYEW`JQ
afoejg
ajgefg!SYFS`JQ
!!!avoefg!SYFS`JQ
afoejg
ajgefg!DST`JQ
!!!avoefg!DST`JQ
afoejg
ajgefg!DPM`JQ
!!!avoefg!DPM`JQ
afoejg
ajgefg!BYJ`HN`SFRVFTU`QSJPSJUZ
!!!avoefg!BYJ`HN`SFRVFTU`QSJPSJUZ
afoejg
ajgefg!BYJ`HN`BEES`XJEUI
!!!avoefg!BYJ`HN`BEES`XJEUI
afoejg
ajgefg!BYJ`HN`EBUB`XJEUI
!!!avoefg!BYJ`HN`EBUB`XJEUI
afoejg
ajgefg!BYJ`HN`EBUB`XJEUI`75
!!!avoefg!BYJ`HN`EBUB`XJEUI`75
afoejg
ajgefg!BYJ`HN`EBUB`XJEUI`239
!!!avoefg!BYJ`HN`EBUB`XJEUI`239
afoejg
ajgefg!BYJ`HN`HN`JE`XJEUI
!!!avoefg!BYJ`HN`HN`JE`XJEUI
afoejg
ajgefg!BYJ`HN`QFS`JE`NBY`XS`SFRVFTUT
!!!avoefg!BYJ`HN`QFS`JE`NBY`XS`SFRVFTUT
afoejg
ajgefg!BYJ`HN`XS`SFR`CVGGFS
!!!avoefg!BYJ`HN`XS`SFR`CVGGFS
afoejg
ajgefg!XS`SFRVFTU`CVGGFS`QSFTFOU
!!!avoefg!XS`SFRVFTU`CVGGFS`QSFTFOU
afoejg
ajgefg!BYJ`HN`XEBUB`CVGGFS
!!!avoefg!BYJ`HN`XEBUB`CVGGFS
afoejg
ajgefg!BYJ`HN`XSFTQ`CVGGFS
!!!avoefg!BYJ`HN`XSFTQ`CVGGFS
afoejg
ajgefg!BYJ`HN`QFS`JE`NBY`SE`SFRVFTUT
!!!avoefg!BYJ`HN`QFS`JE`NBY`SE`SFRVFTUT
afoejg
ajgefg!BYJ`HN`SE`SFR`CVGGFS
!!!avoefg!BYJ`HN`SE`SFR`CVGGFS
afoejg
ajgefg!SE`SFRVFTU`CVGGFS`QSFTFOU
!!!avoefg!SE`SFRVFTU`CVGGFS`QSFTFOU
afoejg
ajgefg!QBE`[FSPT
!!!avoefg!QBE`[FSPT
afoejg
ajgefg!DOUX
!!!avoefg!DOUX
afoejg
ajgefg!UPU`JET
!!!avoefg!UPU`JET
afoejg
ajgefg!CTB
!!!avoefg!CTB
afoejg
ajgefg!TUSX
!!!avoefg!TUSX
afoejg
ajgefg!XUPU`DNET
!!!avoefg!XUPU`DNET
afoejg
ajgefg!XMCDX
!!!avoefg!XMCDX
afoejg
ajgefg!XPTSDX
!!!avoefg!XPTSDX
afoejg
ajgefg!XPTSMX
!!!avoefg!XPTSMX
afoejg
ajgefg!XDNO`DQUSX
!!!avoefg!XDNO`DQUSX
afoejg
ajgefg!XQJE`DQUSX
!!!avoefg!XQJE`DQUSX
afoejg
ajgefg!SUPU`DNET
!!!avoefg!SUPU`DNET
afoejg
ajgefg!SPTSDX
!!!avoefg!SPTSDX
afoejg
ajgefg!SPTSMX
!!!avoefg!SPTSMX
afoejg
ajgefg!SDNO`DQUSX
!!!avoefg!SDNO`DQUSX
afoejg
ajgefg!SQJE`DQUSX
!!!avoefg!SQJE`DQUSX
afoejg
ajgefg!JP`ESRX
!!!avoefg!JP`ESRX
afoejg
ajgefg!HT`BYJ`FY`BDDFTT
!!!avoefg!HT`BYJ`FY`BDDFTT
afoejg
ajgefg!HT`HJG`MJUF
!!!avoefg!HT`HJG`MJUF
afoejg
ajgefg!HT`CJE`CVGGFS
!!!avoefg!HT`CJE`CVGGFS
afoejg
ajgefg!HT`SJE`CVGGFS
!!!avoefg!HT`SJE`CVGGFS
afoejg
ajgefg!HT`EJSFDU`HJG`SFBEZ
!!!avoefg!HT`EJSFDU`HJG`SFBEZ
afoejg
ajgefg!HT`SFR`CVGGFS
!!!avoefg!HT`SFR`CVGGFS
afoejg
ajgefg!HT`XEBUB`CVGGFS
!!!avoefg!HT`XEBUB`CVGGFS
afoejg
ajgefg!HT`EJSFDU`BYJ`SFBEZ
!!!avoefg!HT`EJSFDU`BYJ`SFBEZ
afoejg
ajgefg!HT`SFTQ`CVGGFS
!!!avoefg!HT`SFTQ`CVGGFS
afoejg
ajgefg!M
!!!avoefg!M
afoejg
ajgefg!I
!!!avoefg!I
afoejg
ajgefg!HNBD`G`TZOD`UZQF
!!!avoefg!HNBD`G`TZOD`UZQF
afoejg
ajgefg!HNBD`WFSJG`FO
!!!avoefg!HNBD`WFSJG`FO
afoejg
ajgefg!TUBUVT`PL
!!!avoefg!TUBUVT`PL
afoejg
ajgefg!HNBD`BEES`24`9
!!!avoefg!HNBD`BEES`24`9
afoejg
ajgefg!HNBD`FYUSB`BEES`24`9
!!!avoefg!HNBD`FYUSB`BEES`24`9
afoejg
ajgefg!HNBD`BEE43`BEES`24`9
!!!avoefg!HNBD`BEE43`BEES`24`9
afoejg
ajgefg!HNBD`BEE75`BEES`24`:
!!!avoefg!HNBD`BEE75`BEES`24`:
afoejg
ajgefg!QUQ`SFH`BEES`24`9
!!!avoefg!QUQ`SFH`BEES`24`9
afoejg
ajgefg!NND`BEES`24`9
!!!avoefg!NND`BEES`24`9
afoejg
ajgefg!NND`JQD`BEES`24`9
!!!avoefg!NND`JQD`BEES`24`9
afoejg
ajgefg!ENB`BEES`24`9
!!!avoefg!ENB`BEES`24`9
afoejg
ajgefg!ENB`BEES`DI2`24`9
!!!avoefg!ENB`BEES`DI2`24`9
afoejg
ajgefg!ENB`BEES`DI3`24`9
!!!avoefg!ENB`BEES`DI3`24`9
afoejg
ajgefg!DNF`HNBD`M4`M5`GJMUFS`BEES`24`9
!!!avoefg!DNF`HNBD`M4`M5`GJMUFS`BEES`24`9
afoejg
ajgefg!DNF`HNBD`IBTI`24`8
!!!avoefg!DNF`HNBD`IBTI`24`8
afoejg
ajgefg!DNF`HNBD`WMBO`24`8
!!!avoefg!DNF`HNBD`WMBO`24`8
afoejg
ajgefg!BIC`HNBD
!!!avoefg!BIC`HNBD
afoejg
ajgefg!BEES`CBTF`NTC
!!!avoefg!BEES`CBTF`NTC
afoejg
ajgefg!BEES`PGGTFU`MTC
!!!avoefg!BEES`PGGTFU`MTC
afoejg
ajgefg!TOQT`WFS
!!!avoefg!TOQT`WFS
afoejg
ajgefg!VEQ`IES
!!!avoefg!VEQ`IES
afoejg
ajgefg!UDQ`IES
!!!avoefg!UDQ`IES
afoejg
ajgefg!JDNQ`JQW5`IES
!!!avoefg!JDNQ`JQW5`IES
afoejg
ajgefg!JDNQ`JQW7`IES
!!!avoefg!JDNQ`JQW7`IES
afoejg
ajgefg!IPQCZIPQ`IES
!!!avoefg!IPQCZIPQ`IES
afoejg
ajgefg!SPVUJOH`IES
!!!avoefg!SPVUJOH`IES
afoejg
ajgefg!EFTUPQUT`IES
!!!avoefg!EFTUPQUT`IES
afoejg
ajgefg!BVUI`IES
!!!avoefg!BVUI`IES
afoejg
ajgefg!JQW5
!!!avoefg!JQW5
afoejg
ajgefg!JQW7
!!!avoefg!JQW7
afoejg
ajgefg!TJOHMF
!!!avoefg!TJOHMF
afoejg
ajgefg!JODS
!!!avoefg!JODS
afoejg
ajgefg!XSBQ5
!!!avoefg!XSBQ5
afoejg
ajgefg!JODS5
!!!avoefg!JODS5
afoejg
ajgefg!XSBQ9
!!!avoefg!XSBQ9
afoejg
ajgefg!JODS9
!!!avoefg!JODS9
afoejg
ajgefg!XSBQ27
!!!avoefg!XSBQ27
afoejg
ajgefg!JODS27
!!!avoefg!JODS27
afoejg
ajgefg!JEMF
!!!avoefg!JEMF
afoejg
ajgefg!CVTZ
!!!avoefg!CVTZ
afoejg
ajgefg!OTFR
!!!avoefg!OTFR
afoejg
ajgefg!TFR
!!!avoefg!TFR
afoejg
ajgefg!PL
!!!avoefg!PL
afoejg
ajgefg!FSSPS
!!!avoefg!FSSPS
afoejg
ajgefg!SFUSZ
!!!avoefg!SFUSZ
afoejg
ajgefg!TQMJU
!!!avoefg!TQMJU
afoejg
ajgefg!EVNNZ`UY`TUT
!!!avoefg!EVNNZ`UY`TUT
afoejg
ajgefg!EVNNZ`TUT
!!!avoefg!EVNNZ`TUT
afoejg
ajgefg!PWG`TUT
!!!avoefg!PWG`TUT
afoejg
ajgefg!OBOPTFD`DBSSZ`DPOTU
!!!avoefg!OBOPTFD`DBSSZ`DPOTU
afoejg
ajgefg!STO`XJEUI
!!!avoefg!STO`XJEUI
afoejg
ajgefg!QIZ`TFMFDU`WBM
!!!avoefg!QIZ`TFMFDU`WBM
afoejg
ajgefg!NJJ`VTFD
!!!avoefg!NJJ`VTFD
afoejg
ajgefg!HNJJ`VTFD
!!!avoefg!HNJJ`VTFD
afoejg
ajgefg!NJJ`NTFD
!!!avoefg!NJJ`NTFD
afoejg
ajgefg!HNJJ`NTFD
!!!avoefg!HNJJ`NTFD
afoejg
ajgefg!HNJJ`UY`DHD`WBM
!!!avoefg!HNJJ`UY`DHD`WBM
afoejg
ajgefg!PT`T
!!!avoefg!PT`T
afoejg
ajgefg!PT`S
!!!avoefg!PT`S
afoejg
ajgefg!PT`U
!!!avoefg!PT`U
afoejg
ajgefg!L39`1
!!!avoefg!L39`1
afoejg
ajgefg!L39`2
!!!avoefg!L39`2
afoejg
ajgefg!L39`3
!!!avoefg!L39`3
afoejg
ajgefg!L39`4
!!!avoefg!L39`4
afoejg
ajgefg!L39`5
!!!avoefg!L39`5
afoejg
ajgefg!L39`6
!!!avoefg!L39`6
afoejg
ajgefg!L39`7
!!!avoefg!L39`7
afoejg
ajgefg!L39`8
!!!avoefg!L39`8
afoejg
ajgefg!L34`8
!!!avoefg!L34`8
afoejg
ajgefg!L38`8
!!!avoefg!L38`8
afoejg
ajgefg!L3:`8
!!!avoefg!L3:`8
afoejg
ajgefg!L41`8
!!!avoefg!L41`8
afoejg
ajgefg!E6`7
!!!avoefg!E6`7
afoejg
ajgefg!E27`3
!!!avoefg!E27`3
afoejg
ajgefg!E32`6
!!!avoefg!E32`6
afoejg
ajgefg!E3`3
!!!avoefg!E3`3
afoejg
ajgefg!E1`1
!!!avoefg!E1`1
afoejg
ajgefg!MJOL`UNS`UCJ
!!!avoefg!MJOL`UNS`UCJ
afoejg
ajgefg!MJOL`UNS`THNJJ
!!!avoefg!MJOL`UNS`THNJJ
afoejg
ajgefg!UY`STU`NPEF
!!!avoefg!UY`STU`NPEF
afoejg
ajgefg!UY`291`STU`NPEF
!!!avoefg!UY`291`STU`NPEF
afoejg
ajgefg!SY`STU`NPEF
!!!avoefg!SY`STU`NPEF
afoejg
ajgefg!SY`291`STU`NPEF
!!!avoefg!SY`291`STU`NPEF
afoejg
ajgefg!BQQ`STU`NPEF
!!!avoefg!BQQ`STU`NPEF
afoejg
ajgefg!DTS`STU`NPEF
!!!avoefg!DTS`STU`NPEF
afoejg
ajgefg!TSD`STU`NPEF
!!!avoefg!TSD`STU`NPEF
afoejg
ajgefg!BIC`STU`NPEF
!!!avoefg!BIC`STU`NPEF
afoejg
ajgefg!SNJJ`STU`NPEF
!!!avoefg!SNJJ`STU`NPEF
afoejg
ajgefg!QUQ`STU`NPEF
!!!avoefg!QUQ`STU`NPEF
afoejg
ajgefg!UY`236`STU`NPEF
!!!avoefg!UY`236`STU`NPEF
afoejg
ajgefg!SY`236`STU`NPEF
!!!avoefg!SY`236`STU`NPEF
afoejg
ajgefg!STU`HN`NPEF
!!!avoefg!STU`HN`NPEF
afoejg
ajgefg!STU`HT`NPEF
!!!avoefg!STU`HT`NPEF
afoejg
ajgefg!EXCC`STU`NPEF
!!!avoefg!EXCC`STU`NPEF
afoejg
ajgefg!SFWNJJ`NED`STU`NPEF
!!!avoefg!SFWNJJ`NED`STU`NPEF
afoejg
ajgefg!SFWNJJ`UYDML`STU`NPEF
!!!avoefg!SFWNJJ`UYDML`STU`NPEF
afoejg
ajgefg!SFWNJJ`SYDML`STU`NPEF
!!!avoefg!SFWNJJ`SYDML`STU`NPEF
afoejg
ajgefg!STU`QDT`UY`NPEF
!!!avoefg!STU`QDT`UY`NPEF
afoejg
ajgefg!STU`QDT`SY`NPEF
!!!avoefg!STU`QDT`SY`NPEF
afoejg
ajgefg!SBOEPN`TFFE`2
!!!avoefg!SBOEPN`TFFE`2
afoejg
ajgefg!SBOEPN`TFFE`3
!!!avoefg!SBOEPN`TFFE`3
afoejg
ajgefg!SBOEPN`TFFE`4
!!!avoefg!SBOEPN`TFFE`4
afoejg
ajgefg!SBOEPN`TFFE`5
!!!avoefg!SBOEPN`TFFE`5
afoejg
ajgefg!NBTL`2
!!!avoefg!NBTL`2
afoejg
ajgefg!NBTL`3
!!!avoefg!NBTL`3
afoejg
ajgefg!NBTL`4
!!!avoefg!NBTL`4
afoejg
ajgefg!NBTL`5
!!!avoefg!NBTL`5
afoejg
ajgefg!QCM`NTC`[FSPT
!!!avoefg!QCM`NTC`[FSPT
afoejg
ajgefg!BEES`CBTF`JODS
!!!avoefg!BEES`CBTF`JODS
afoejg
ajgefg!EBUB`CVT`TJ[F
!!!avoefg!EBUB`CVT`TJ[F
afoejg
ajgefg!CZUF`FOBCMFT`EFDS
!!!avoefg!CZUF`FOBCMFT`EFDS
afoejg
ajgefg!SY`CVG`TJ[F`MTC`[FSPT
!!!avoefg!SY`CVG`TJ[F`MTC`[FSPT
afoejg
ajgefg!EFTD`BEES`MTC`[FSPT
!!!avoefg!EFTD`BEES`MTC`[FSPT
afoejg
ajgefg!TUT`XJEUI
!!!avoefg!TUT`XJEUI
afoejg
ajgefg!EBG`TUT`XJEUI
!!!avoefg!EBG`TUT`XJEUI
afoejg
ajgefg!UISFT`XJEUI
!!!avoefg!UISFT`XJEUI
afoejg
ajgefg!BWH`CX`DOUS`XJEUI
!!!avoefg!BWH`CX`DOUS`XJEUI
afoejg
ajgefg!CVGTJ[F`XJEUI
!!!avoefg!CVGTJ[F`XJEUI
afoejg
ajgefg!EFTD`SFBE`TJ[F
!!!avoefg!EFTD`SFBE`TJ[F
afoejg
ajgefg!EFTD`XSJUF`TJ[F
!!!avoefg!EFTD`XSJUF`TJ[F
afoejg
ajgefg!UJNF`XSJUF`TJ[F
!!!avoefg!UJNF`XSJUF`TJ[F
afoejg
ajgefg!TJ[F`CBTF`NTC
!!!avoefg!TJ[F`CBTF`NTC
afoejg
ajgefg!TJ[F`CBTF`JODS
!!!avoefg!TJ[F`CBTF`JODS
afoejg
ajgefg!OFFEFE`CFBUT`POF
!!!avoefg!OFFEFE`CFBUT`POF
afoejg
ajgefg!XPSEDOU`XJEUI
!!!avoefg!XPSEDOU`XJEUI
afoejg
ajgefg!IESDOU`XJEUI
!!!avoefg!IESDOU`XJEUI
afoejg
ajgefg!SY`NND`GJGP`XJEUI
!!!avoefg!SY`NND`GJGP`XJEUI
afoejg
ajgefg!DPSF`TUBUVT`XJEUI
!!!avoefg!DPSF`TUBUVT`XJEUI
afoejg
ajgefg!UT`SFH`TFM`XJEUI
!!!avoefg!UT`SFH`TFM`XJEUI
afoejg
ajgefg!DNF`HNBD`UT`TUT`XJEUI
!!!avoefg!DNF`HNBD`UT`TUT`XJEUI
afoejg
ajgefg!YTX
!!!avoefg!YTX
afoejg
ajgefg!TBWJOT
!!!avoefg!TBWJOT
afoejg
ajgefg!GMYQQT
!!!avoefg!GMYQQT
afoejg
ajgefg!JOU`UT
!!!avoefg!JOU`UT
afoejg
ajgefg!BMU`EFTD
!!!avoefg!BMU`EFTD
afoejg
ajgefg!SYDPF3
!!!avoefg!SYDPF3
afoejg
ajgefg!SYDPF2
!!!avoefg!SYDPF2
afoejg
ajgefg!UYDPF
!!!avoefg!UYDPF
afoejg
ajgefg!BWCFO
!!!avoefg!BWCFO
afoejg
ajgefg!FFFO
!!!avoefg!FFFO
afoejg
ajgefg!UT`UZQ3
!!!avoefg!UT`UZQ3
afoejg
ajgefg!UT`UZQ2
!!!avoefg!UT`UZQ2
afoejg
ajgefg!NNDFO
!!!avoefg!NNDFO
afoejg
ajgefg!QNUSXL
!!!avoefg!QNUSXL
afoejg
ajgefg!QNUNHL
!!!avoefg!QNUNHL
afoejg
ajgefg!TNBFO
!!!avoefg!TNBFO
afoejg
ajgefg!M4M5FO
!!!avoefg!M4M5FO
afoejg
ajgefg!QDTSFH
!!!avoefg!QDTSFH
afoejg
ajgefg!NVMUJBEES
!!!avoefg!NVMUJBEES
afoejg
ajgefg!IBTIG
!!!avoefg!IBTIG
afoejg
ajgefg!FYIBTIG
!!!avoefg!FYIBTIG
afoejg
ajgefg!IE`FO
!!!avoefg!IE`FO
afoejg
ajgefg!TQFFE
!!!avoefg!TQFFE
afoejg
ajgefg!BYJ`HN`SEBUB`CVGGFS
!!!avoefg!BYJ`HN`SEBUB`CVGGFS
afoejg
ajgefg!BYJ`MQJ`DOUX
!!!avoefg!BYJ`MQJ`DOUX
afoejg
ajgefg!BX
!!!avoefg!BX
afoejg
ajgefg!EBUX
!!!avoefg!EBUX
afoejg
ajgefg!BYJ`JEX
!!!avoefg!BYJ`JEX
afoejg
ajgefg!JEX
!!!avoefg!JEX
afoejg
ajgefg!JEXJ
!!!avoefg!JEXJ
afoejg
ajgefg!BEE`JEX
!!!avoefg!BEE`JEX
afoejg
ajgefg!HNX`QX
!!!avoefg!HNX`QX
afoejg
ajgefg!HNX`XS
!!!avoefg!HNX`XS
afoejg
ajgefg!DNE`JEMF
!!!avoefg!DNE`JEMF
afoejg
ajgefg!JOD`B
!!!avoefg!JOD`B
afoejg
ajgefg!JOD
!!!avoefg!JOD
afoejg
ajgefg!XSBQ
!!!avoefg!XSBQ
afoejg
ajgefg!PL`S
!!!avoefg!PL`S
afoejg
ajgefg!PL`X
!!!avoefg!PL`X
afoejg
ajgefg!PL`SFTQ
!!!avoefg!PL`SFTQ
afoejg
ajgefg!FSS`SFTQ
!!!avoefg!FSS`SFTQ
afoejg
ajgefg!BEE`SFTQ
!!!avoefg!BEE`SFTQ
afoejg
ajgefg!DNEX
!!!avoefg!DNEX
afoejg
ajgefg!PP`ESRX
!!!avoefg!PP`ESRX
afoejg
ajgefg!EBUGX
!!!avoefg!EBUGX
afoejg
ajgefg!XSTGX
!!!avoefg!XSTGX
afoejg
ajgefg!SSTGX
!!!avoefg!SSTGX
afoejg
ajgefg!HT`BX
!!!avoefg!HT`BX
afoejg
ajgefg!HT`CX
!!!avoefg!HT`CX
afoejg
ajgefg!HT`EX
!!!avoefg!HT`EX
afoejg
ajgefg!HT`TSFTQ`PL`S
!!!avoefg!HT`TSFTQ`PL`S
afoejg
ajgefg!HT`TSFTQ`PL`X
!!!avoefg!HT`TSFTQ`PL`X
afoejg
ajgefg!HT`TSFTQ`TMWFSS`S
!!!avoefg!HT`TSFTQ`TMWFSS`S
afoejg
ajgefg!HT`TSFTQ`TMWFSS`X
!!!avoefg!HT`TSFTQ`TMWFSS`X
afoejg
ajgefg!HT`CVSTU`GJYFE
!!!avoefg!HT`CVSTU`GJYFE
afoejg
ajgefg!HT`CVSTU`JODS
!!!avoefg!HT`CVSTU`JODS
afoejg
ajgefg!HT`CVSTU`XSBQ
!!!avoefg!HT`CVSTU`XSBQ
afoejg
ajgefg!HT`CVSTU`VJODS
!!!avoefg!HT`CVSTU`VJODS
afoejg
ajgefg!HT`BYJ`GJYFE
!!!avoefg!HT`BYJ`GJYFE
afoejg
ajgefg!HT`BYJ`JODS
!!!avoefg!HT`BYJ`JODS
afoejg
ajgefg!HT`BYJ`XSBQ
!!!avoefg!HT`BYJ`XSBQ
afoejg
ajgefg!HT`BYJ`SFTWE
!!!avoefg!HT`BYJ`SFTWE
afoejg
ajgefg!HT`BYJ`PLBZ
!!!avoefg!HT`BYJ`PLBZ
afoejg
ajgefg!HT`BYJ`FYPLBZ
!!!avoefg!HT`BYJ`FYPLBZ
afoejg
ajgefg!HT`BYJ`TMWFSS
!!!avoefg!HT`BYJ`TMWFSS
afoejg
ajgefg!HT`BYJ`EFDFSS
!!!avoefg!HT`BYJ`EFDFSS
afoejg
ajgefg!UYE`JPX
!!!avoefg!UYE`JPX
afoejg
ajgefg!SYE`JPX
!!!avoefg!SYE`JPX
afoejg
ajgefg!TMPU`DOUS`XJEUI
!!!avoefg!TMPU`DOUS`XJEUI
afoejg
ajgefg!TMPU2`DOU`N2111
!!!avoefg!TMPU2`DOU`N2111
afoejg
ajgefg!TMPU3`DOU`N2111
!!!avoefg!TMPU3`DOU`N2111
afoejg
ajgefg!TMPU4`DOU`N2111
!!!avoefg!TMPU4`DOU`N2111
afoejg
ajgefg!TMPU5`DOU`N2111
!!!avoefg!TMPU5`DOU`N2111
afoejg
ajgefg!TMPU6`DOU`N2111
!!!avoefg!TMPU6`DOU`N2111
afoejg
ajgefg!TMPU2`DOU`N211
!!!avoefg!TMPU2`DOU`N211
afoejg
ajgefg!TMPU3`DOU`N211
!!!avoefg!TMPU3`DOU`N211
afoejg
ajgefg!TMPU4`DOU`N211
!!!avoefg!TMPU4`DOU`N211
afoejg
ajgefg!TMPU5`DOU`N211
!!!avoefg!TMPU5`DOU`N211
afoejg
ajgefg!TMPU6`DOU`N211
!!!avoefg!TMPU6`DOU`N211
afoejg
ajgefg!OVN`SY`DI
!!!avoefg!OVN`SY`DI
afoejg
ajgefg!OVN`UY`DI
!!!avoefg!OVN`UY`DI
afoejg
ajgefg!OED
!!!avoefg!OED
afoejg
ajgefg!NND`UYBEES`SOH`DOU`XJEUI
!!!avoefg!NND`UYBEES`SOH`DOU`XJEUI
afoejg
ajgefg!NND`UYPDUHC`DOU`XJEUI
!!!avoefg!NND`UYPDUHC`DOU`XJEUI
afoejg
ajgefg!NND`UYGSNHC`DOU`XJEUI
!!!avoefg!NND`UYGSNHC`DOU`XJEUI
afoejg
ajgefg!NND`UYCDBTUH`DOU`XJEUI
!!!avoefg!NND`UYCDBTUH`DOU`XJEUI
afoejg
ajgefg!NND`UYNDBTUH`DOU`XJEUI
!!!avoefg!NND`UYNDBTUH`DOU`XJEUI
afoejg
ajgefg!NND`UYVDBTUHC`DOU`XJEUI
!!!avoefg!NND`UYVDBTUHC`DOU`XJEUI
afoejg
ajgefg!NND`UYNDBTUHC`DOU`XJEUI
!!!avoefg!NND`UYNDBTUHC`DOU`XJEUI
afoejg
ajgefg!NND`UYCDBTUHC`DOU`XJEUI
!!!avoefg!NND`UYCDBTUHC`DOU`XJEUI
afoejg
ajgefg!NND`UYVOESGMX`DOU`XJEUI
!!!avoefg!NND`UYVOESGMX`DOU`XJEUI
afoejg
ajgefg!NND`UYTOHMDPMH`DOU`XJEUI
!!!avoefg!NND`UYTOHMDPMH`DOU`XJEUI
afoejg
ajgefg!NND`UYNVMUDPMH`DOU`XJEUI
!!!avoefg!NND`UYNVMUDPMH`DOU`XJEUI
afoejg
ajgefg!NND`UYEFGSE`DOU`XJEUI
!!!avoefg!NND`UYEFGSE`DOU`XJEUI
afoejg
ajgefg!NND`UYMBUFDPM`DOU`XJEUI
!!!avoefg!NND`UYMBUFDPM`DOU`XJEUI
afoejg
ajgefg!NND`UYFYTDPM`DOU`XJEUI
!!!avoefg!NND`UYFYTDPM`DOU`XJEUI
afoejg
ajgefg!NND`UYDBSS`DOU`XJEUI
!!!avoefg!NND`UYDBSS`DOU`XJEUI
afoejg
ajgefg!NND`UYPDUH`DOU`XJEUI
!!!avoefg!NND`UYPDUH`DOU`XJEUI
afoejg
ajgefg!NND`UYGSNH`DOU`XJEUI
!!!avoefg!NND`UYGSNH`DOU`XJEUI
afoejg
ajgefg!NND`UYFYTEFG`DOU`XJEUI
!!!avoefg!NND`UYFYTEFG`DOU`XJEUI
afoejg
ajgefg!NND`UYQBVTF`DOU`XJEUI
!!!avoefg!NND`UYQBVTF`DOU`XJEUI
afoejg
ajgefg!NND`UYWMBO`DOU`XJEUI
!!!avoefg!NND`UYWMBO`DOU`XJEUI
afoejg
ajgefg!DNF`HNBD`NND`UYPWFST[H`DOU`XJEUI
!!!avoefg!DNF`HNBD`NND`UYPWFST[H`DOU`XJEUI
afoejg
ajgefg!NND`SYGSNHC`DOU`XJEUI
!!!avoefg!NND`SYGSNHC`DOU`XJEUI
afoejg
ajgefg!NND`SYPDUHC`DOU`XJEUI
!!!avoefg!NND`SYPDUHC`DOU`XJEUI
afoejg
ajgefg!NND`SYPDUH`DOU`XJEUI
!!!avoefg!NND`SYPDUH`DOU`XJEUI
afoejg
ajgefg!NND`SYCDBTUH`DOU`XJEUI
!!!avoefg!NND`SYCDBTUH`DOU`XJEUI
afoejg
ajgefg!NND`SYNDBTUH`DOU`XJEUI
!!!avoefg!NND`SYNDBTUH`DOU`XJEUI
afoejg
ajgefg!NND`SYDSDFSS`DOU`XJEUI
!!!avoefg!NND`SYDSDFSS`DOU`XJEUI
afoejg
ajgefg!NND`SYBMHOFSS`DOU`XJEUI
!!!avoefg!NND`SYBMHOFSS`DOU`XJEUI
afoejg
ajgefg!NND`SYSVOUFSS`DOU`XJEUI
!!!avoefg!NND`SYSVOUFSS`DOU`XJEUI
afoejg
ajgefg!NND`SYKBCFSS`DOU`XJEUI
!!!avoefg!NND`SYKBCFSS`DOU`XJEUI
afoejg
ajgefg!NND`SYVOEFST[H`DOU`XJEUI
!!!avoefg!NND`SYVOEFST[H`DOU`XJEUI
afoejg
ajgefg!NND`SYPWFST[H`DOU`XJEUI
!!!avoefg!NND`SYPWFST[H`DOU`XJEUI
afoejg
ajgefg!NND`SYBEES`SOH`DOU`XJEUI
!!!avoefg!NND`SYBEES`SOH`DOU`XJEUI
afoejg
ajgefg!NND`SYVDBTUH`DOU`XJEUI
!!!avoefg!NND`SYVDBTUH`DOU`XJEUI
afoejg
ajgefg!NND`SYMFOFSS`DOU`XJEUI
!!!avoefg!NND`SYMFOFSS`DOU`XJEUI
afoejg
ajgefg!NND`SYPVUPGSOH`UZQ`DOU`XJEUI
!!!avoefg!NND`SYPVUPGSOH`UZQ`DOU`XJEUI
afoejg
ajgefg!NND`SYQBVTFGSN`DOU`XJEUI
!!!avoefg!NND`SYQBVTFGSN`DOU`XJEUI
afoejg
ajgefg!NND`SYGJGPPWGM`DOU`XJEUI
!!!avoefg!NND`SYGJGPPWGM`DOU`XJEUI
afoejg
ajgefg!NND`SYWMBOGSHC`DOU`XJEUI
!!!avoefg!NND`SYWMBOGSHC`DOU`XJEUI
afoejg
ajgefg!NND`SYXEHFSS`DOU`XJEUI
!!!avoefg!NND`SYXEHFSS`DOU`XJEUI
afoejg
ajgefg!DNF`HNBD`NND`SYSDWFSS`DOU`XJEUI
!!!avoefg!DNF`HNBD`NND`SYSDWFSS`DOU`XJEUI
afoejg
ajgefg!DNF`HNBD`NND`SYDUSMGSN`DOU`XJEUI
!!!avoefg!DNF`HNBD`NND`SYDUSMGSN`DOU`XJEUI
afoejg
ajgefg!NND`SY`JQW5`HE`GSNT`DOU`XJEUI
!!!avoefg!NND`SY`JQW5`HE`GSNT`DOU`XJEUI
afoejg
ajgefg!NND`SY`JQW5`IESFSS`GSNT`DOU`XJEUI
!!!avoefg!NND`SY`JQW5`IESFSS`GSNT`DOU`XJEUI
afoejg
ajgefg!NND`SY`JQW5`OPQBZ`GSNT`DOU`XJEUI
!!!avoefg!NND`SY`JQW5`OPQBZ`GSNT`DOU`XJEUI
afoejg
ajgefg!NND`SY`JQW5`GSBH`GSNT`DOU`XJEUI
!!!avoefg!NND`SY`JQW5`GSBH`GSNT`DOU`XJEUI
afoejg
ajgefg!NND`SY`JQW5`VETCM`GSNT`DOU`XJEUI
!!!avoefg!NND`SY`JQW5`VETCM`GSNT`DOU`XJEUI
afoejg
ajgefg!NND`SY`JQW7`HE`GSNT`DOU`XJEUI
!!!avoefg!NND`SY`JQW7`HE`GSNT`DOU`XJEUI
afoejg
ajgefg!NND`SY`JQW7`IESFSS`GSNT`DOU`XJEUI
!!!avoefg!NND`SY`JQW7`IESFSS`GSNT`DOU`XJEUI
afoejg
ajgefg!NND`SY`JQW7`OPQBZ`GSNT`DOU`XJEUI
!!!avoefg!NND`SY`JQW7`OPQBZ`GSNT`DOU`XJEUI
afoejg
ajgefg!NND`SY`VEQ`HE`GSNT`DOU`XJEUI
!!!avoefg!NND`SY`VEQ`HE`GSNT`DOU`XJEUI
afoejg
ajgefg!NND`SY`VEQ`FSS`GSNT`DOU`XJEUI
!!!avoefg!NND`SY`VEQ`FSS`GSNT`DOU`XJEUI
afoejg
ajgefg!NND`SY`UDQ`HE`GSNT`DOU`XJEUI
!!!avoefg!NND`SY`UDQ`HE`GSNT`DOU`XJEUI
afoejg
ajgefg!NND`SY`UDQ`FSS`GSNT`DOU`XJEUI
!!!avoefg!NND`SY`UDQ`FSS`GSNT`DOU`XJEUI
afoejg
ajgefg!NND`SY`JDNQ`HE`GSNT`DOU`XJEUI
!!!avoefg!NND`SY`JDNQ`HE`GSNT`DOU`XJEUI
afoejg
ajgefg!NND`SY`JDNQ`FSS`GSNT`DOU`XJEUI
!!!avoefg!NND`SY`JDNQ`FSS`GSNT`DOU`XJEUI
afoejg
ajgefg!NND`SY`JQW5`HE`PDUFU`DOU`XJEUI
!!!avoefg!NND`SY`JQW5`HE`PDUFU`DOU`XJEUI
afoejg
ajgefg!NND`SY`JQW5`IESFSS`PDUFU`DOU`XJEUI
!!!avoefg!NND`SY`JQW5`IESFSS`PDUFU`DOU`XJEUI
afoejg
ajgefg!NND`SY`JQW5`OPQBZ`PDUFU`DOU`XJEUI
!!!avoefg!NND`SY`JQW5`OPQBZ`PDUFU`DOU`XJEUI
afoejg
ajgefg!NND`SY`JQW5`GSBH`PDUFU`DOU`XJEUI
!!!avoefg!NND`SY`JQW5`GSBH`PDUFU`DOU`XJEUI
afoejg
ajgefg!NND`SY`JQW5`VETCM`PDUFU`DOU`XJEUI
!!!avoefg!NND`SY`JQW5`VETCM`PDUFU`DOU`XJEUI
afoejg
ajgefg!NND`SY`JQW7`HE`PDUFU`DOU`XJEUI
!!!avoefg!NND`SY`JQW7`HE`PDUFU`DOU`XJEUI
afoejg
ajgefg!NND`SY`JQW7`IESFSS`PDUFU`DOU`XJEUI
!!!avoefg!NND`SY`JQW7`IESFSS`PDUFU`DOU`XJEUI
afoejg
ajgefg!NND`SY`JQW7`OPQBZ`PDUFU`DOU`XJEUI
!!!avoefg!NND`SY`JQW7`OPQBZ`PDUFU`DOU`XJEUI
afoejg
ajgefg!NND`SY`VEQ`HE`PDUFU`DOU`XJEUI
!!!avoefg!NND`SY`VEQ`HE`PDUFU`DOU`XJEUI
afoejg
ajgefg!NND`SY`VEQ`FSS`PDUFU`DOU`XJEUI
!!!avoefg!NND`SY`VEQ`FSS`PDUFU`DOU`XJEUI
afoejg
ajgefg!NND`SY`UDQ`HE`PDUFU`DOU`XJEUI
!!!avoefg!NND`SY`UDQ`HE`PDUFU`DOU`XJEUI
afoejg
ajgefg!NND`SY`UDQ`FSS`PDUFU`DOU`XJEUI
!!!avoefg!NND`SY`UDQ`FSS`PDUFU`DOU`XJEUI
afoejg
ajgefg!NND`SY`JDNQ`HE`PDUFU`DOU`XJEUI
!!!avoefg!NND`SY`JDNQ`HE`PDUFU`DOU`XJEUI
afoejg
ajgefg!NND`SY`JDNQ`FSS`PDUFU`DOU`XJEUI
!!!avoefg!NND`SY`JDNQ`FSS`PDUFU`DOU`XJEUI
afoejg
ajgefg!DNF`HNBD`NND`QSTFU`GDOU`WBM
!!!avoefg!DNF`HNBD`NND`QSTFU`GDOU`WBM
afoejg
ajgefg!DNF`HNBD`NND`QSTFU`PDOU`WBM
!!!avoefg!DNF`HNBD`NND`QSTFU`PDOU`WBM
afoejg
ajgefg!DNF`EJTBMMPX`MBUDIFT
!!!avoefg!DNF`EJTBMMPX`MBUDIFT
afoejg
ajgefg!QUQ`TFD`PWG`XJEUI
!!!avoefg!QUQ`TFD`PWG`XJEUI
afoejg
ajgefg!DNF`HNBD`IBTI`JEY
!!!avoefg!DNF`HNBD`IBTI`JEY
afoejg
ajgefg!DNF`HNBD`EFT`DUM`GJGP`XJEUI
!!!avoefg!DNF`HNBD`EFT`DUM`GJGP`XJEUI
afoejg
ajgefg!DNF`HNBD`BVY`GJGP`XJEUI
!!!avoefg!DNF`HNBD`BVY`GJGP`XJEUI
afoejg
ajgefg!DNF`HNBD`BVY`GJGP`QUS`XEUI
!!!avoefg!DNF`HNBD`BVY`GJGP`QUS`XEUI
afoejg
ajgefg!DNF`HNBD`TUT`GJGP`XJEUI
!!!avoefg!DNF`HNBD`TUT`GJGP`XJEUI
afoejg
ajgefg!EX`ebub`t`jou
!!!avoefg!EX`ebub`t`jou
afoejg
ajgefg!EX`GPSDFE`WBMVF
!!!avoefg!EX`GPSDFE`WBMVF
afoejg
ajgefg!EX`GPSDFE`WBMVF`CJO3HSBZ
!!!avoefg!EX`GPSDFE`WBMVF`CJO3HSBZ
afoejg
ajgefg!TNB`JEMF
!!!avoefg!TNB`JEMF
afoejg
ajgefg!TNB`QSF
!!!avoefg!TNB`QSF
afoejg
ajgefg!TNB`PQD
!!!avoefg!TNB`PQD
afoejg
ajgefg!TNB`BEES
!!!avoefg!TNB`BEES
afoejg
ajgefg!TNB`EBUB
!!!avoefg!TNB`EBUB
afoejg
ajgefg!EJW31UP46
!!!avoefg!EJW31UP46
afoejg
ajgefg!EJW46UP71
!!!avoefg!EJW46UP71
afoejg
ajgefg!EJW71UP211
!!!avoefg!EJW71UP211
afoejg
ajgefg!EJW211UP261
!!!avoefg!EJW211UP261
afoejg
ajgefg!EJW261UP361
!!!avoefg!EJW261UP361
afoejg
ajgefg!EJW361UP411
!!!avoefg!EJW361UP411
afoejg
ajgefg!EJWCZ5
!!!avoefg!EJWCZ5
afoejg
ajgefg!EJWCZ7
!!!avoefg!EJWCZ7
afoejg
ajgefg!EJWCZ9
!!!avoefg!EJWCZ9
afoejg
ajgefg!EJWCZ21
!!!avoefg!EJWCZ21
afoejg
ajgefg!EJWCZ23
!!!avoefg!EJWCZ23
afoejg
ajgefg!EJWCZ25
!!!avoefg!EJWCZ25
afoejg
ajgefg!EJWCZ27
!!!avoefg!EJWCZ27
afoejg
ajgefg!EJWCZ29
!!!avoefg!EJWCZ29
afoejg
ajgefg!TGE
!!!avoefg!TGE
afoejg
ajgefg!NJO`GSBNF`MFO
!!!avoefg!NJO`GSBNF`MFO
afoejg
ajgefg!NJO`GSBNF`MFO`WMBO
!!!avoefg!NJO`GSBNF`MFO`WMBO
afoejg
ajgefg!NBY`GSBNF`MFO
!!!avoefg!NBY`GSBNF`MFO
afoejg
ajgefg!NBY`GSBNF`MFO`WMBO
!!!avoefg!NBY`GSBNF`MFO`WMBO
afoejg
ajgefg!JGH`DX
!!!avoefg!JGH`DX
afoejg
ajgefg!MGTS`DOU`2
!!!avoefg!MGTS`DOU`2
afoejg
ajgefg!MGTS`DOU`4
!!!avoefg!MGTS`DOU`4
afoejg
ajgefg!MGTS`DOU`5
!!!avoefg!MGTS`DOU`5
afoejg
ajgefg!MGTS`DOU`6
!!!avoefg!MGTS`DOU`6
afoejg
ajgefg!MGTS`DOU`7
!!!avoefg!MGTS`DOU`7
afoejg
ajgefg!MGTS`DOU`8
!!!avoefg!MGTS`DOU`8
afoejg
ajgefg!MGTS`DOU`9
!!!avoefg!MGTS`DOU`9
afoejg
ajgefg!MGTS`DOU`21
!!!avoefg!MGTS`DOU`21
afoejg
ajgefg!MGTS`DOU`25
!!!avoefg!MGTS`DOU`25
afoejg
ajgefg!FYTTEFG`MNU`HNJJ
!!!avoefg!FYTTEFG`MNU`HNJJ
afoejg
ajgefg!FYTTEFG`MNU`NJJ
!!!avoefg!FYTTEFG`MNU`NJJ
afoejg
ajgefg!FBSMZ`CTU`MNU
!!!avoefg!FBSMZ`CTU`MNU
afoejg
ajgefg!EX`l39q6npef
!!!avoefg!EX`l39q6npef
afoejg
ajgefg!EX`qu`2
!!!avoefg!EX`qu`2
afoejg
ajgefg!EX`qu`3
!!!avoefg!EX`qu`3
afoejg
ajgefg!EX`qu`4
!!!avoefg!EX`qu`4
afoejg
ajgefg!EX`qu`5
!!!avoefg!EX`qu`5
afoejg
ajgefg!EX`qu`6
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



aefgjof!DTS`EBUBXJEUI!43


aefgjof!DTS`EBUBXJEUI`43














aefgjof!HJX!1


aefgjof!HPX!1



aefgjof!BYJ`CM!27


aefgjof!CMX!5









!







aefgjof!PQ`NPEF!1


aefgjof!GEVQMY`POMZ






aefgjof!VTFS`WFS!9(i21


aefgjof!BTZOD`STU


aefgjof!SYGJGP`TJ[F!3159


aefgjof!UYGJGP`TJ[F!3159


aefgjof!NBY`GSBNF`JO`UYGJGP!3






aefgjof!TUT`QUS`XJEUI!2


aefgjof!NBY`GSBNF`JO`UYGJGP`3


aefgjof!SY`GJGP`QUS`XJEUI!:


aefgjof!BSJ`QCM`XJEUI!9


aefgjof!GJGP`EBUB`XJEUI!46


aefgjof!UY`GJGP`QUS`XJEUI!:


aefgjof!BUJ`QCM`XJEUI!9


aefgjof!BEES`PGGTFU`NTC!2


aefgjof!NJO`GSBNF`TJ[F!27


aefgjof!NBY`GSBNF`DOU`XJEUI!9


aefgjof!GSBNF`MFO`GJGP`XJEUI!26




aefgjof!BEES`CBTF`MTC!3


aefgjof!BEES`CBTF`TJ[F!41


aefgjof!BEES`PGGTFU`TJ[F!3


aefgjof!EFTD`BEES`NTC!3:


aefgjof!SY`CVG`TJ[F`NTC!9



aefgjof!UCV`OP`PG`TUBUFT!4









































































aefgjof!IBTI`EJT


aefgjof!DNF`HNBD`IBTI`UBCMF!1










aefgjof!DNF`HNBD`M4`M5`GJMUFS`OVN!1
































aefgjof!SGD`GEFQUI!5


aefgjof!SGD`GQUSXJEUI!3


































aefgjof!TJOHMF`QIZ`JOUG




















aefgjof!HNJJ`JOUG`POMZ








aefgjof!BW`UY`DIBOOFM!1


aefgjof!BW`SY`DIBOOFM!1












aefgjof!BYJ`HN`BYJ`JE`XJEUI!5

!
aefgjof!HT`JE!9


aefgjof!BYJ`HN`NBY`SE`SFRVFTUT!5


aefgjof!BYJ`HN`NBY`XS`SFRVFTUT!5






aefgjof!DPBSTF`GJOF`DPSSFDUJPO!3









aefgjof!DNF`HNBD`BVY`TOBQ`JO`OVN!1








aefgjof!DNF`HNBD`BVY`GJGP`EFQUI!5




aefgjof!DNF`HNBD`QQT`PVU`OVN!1




















aefgjof!DILTVN`GJGP`XJEUI!43


aefgjof!DILTVN`QUS`XJEUI!3



















































































































































































































































































































aefgjof!TNB`FO










aefgjof!TJ[F`CBTF`TJ[F!:


aefgjof!OFFEFE`CFBUT`TJ[F!21




aefgjof!HOU`GSBNF`UISTIME!621


aefgjof!UYE`XJEUI!9


aefgjof!SYE`XJEUI!9



aefgjof!UYFO`PQ


aefgjof!UYFS`PQ


aefgjof!SYEW`JQ


aefgjof!SYFS`JQ


aefgjof!DST`JQ


aefgjof!DPM`JQ


!
aefgjof!BYJ`HN`SFRVFTU`QSJPSJUZ

!
aefgjof!BYJ`HN`BEES`XJEUI!43

!
aefgjof!BYJ`HN`EBUB`XJEUI!43



!

!
aefgjof!BYJ`HN`HN`JE`XJEUI!2

!
aefgjof!BYJ`HN`QFS`JE`NBY`XS`SFRVFTUT!3

!
aefgjof!BYJ`HN`XS`SFR`CVGGFS!3

!

!
aefgjof!BYJ`HN`XEBUB`CVGGFS!3

!
aefgjof!BYJ`HN`XSFTQ`CVGGFS!3


!
aefgjof!BYJ`HN`QFS`JE`NBY`SE`SFRVFTUT!3

!
aefgjof!BYJ`HN`SE`SFR`CVGGFS!3

!

!
aefgjof!QBE`[FSPT!2

!!
!
aefgjof!DOUX!27

!
aefgjof!UPU`JET!3


aefgjof!CTB!3

!
aefgjof!TUSX!5

!
aefgjof!XUPU`DNET!5

!
aefgjof!XMCDX!3

!
aefgjof!XPTSDX!4

!
aefgjof!XPTSMX!3

!
aefgjof!XDNO`DQUSX!3

!
aefgjof!XQJE`DQUSX!2

!
aefgjof!SUPU`DNET!5

!
aefgjof!SPTSDX!4

!
aefgjof!SPTSMX!3

!
aefgjof!SDNO`DQUSX!3

!
aefgjof!SQJE`DQUSX!2

!
aefgjof!JP`ESRX!23



aefgjof!HT`BYJ`FY`BDDFTT!1


aefgjof!HT`HJG`MJUF!1


aefgjof!HT`CJE`CVGGFS!2


aefgjof!HT`SJE`CVGGFS!2


aefgjof!HT`EJSFDU`HJG`SFBEZ!2


aefgjof!HT`SFR`CVGGFS!2


aefgjof!HT`XEBUB`CVGGFS!2



aefgjof!HT`EJSFDU`BYJ`SFBEZ!2


aefgjof!HT`SFTQ`CVGGFS!2



aefgjof!M!2(c1
aefgjof!I!2(c2

aefgjof!HNBD`G`TZOD`UZQF!3
aefgjof!HNBD`WFSJG`FO!3

aefgjof!TUBUVT`PL!35(i151151

aefgjof!HNBD`BEES`24`9!7(i11
aefgjof!HNBD`FYUSB`BEES`24`9!7(i19
aefgjof!HNBD`BEE43`BEES`24`9!7(i1:
aefgjof!HNBD`BEE75`BEES`24`:!6(i16
aefgjof!QUQ`SFH`BEES`24`9!7(i18!
aefgjof!NND`BEES`24`9!7(i12
aefgjof!NND`JQD`BEES`24`9!7(i13
aefgjof!ENB`BEES`24`9!7(i21
aefgjof!ENB`BEES`DI2`24`9!7(i22
aefgjof!ENB`BEES`DI3`24`9!7(i23
aefgjof!DNF`HNBD`M4`M5`GJMUFS`BEES`24`9!7(i15
aefgjof!DNF`HNBD`IBTI`24`8!8(i1B
aefgjof!DNF`HNBD`WMBO`24`8!8(i1C

aefgjof!BIC`HNBD
aefgjof!BEES`CBTF`NTC!42
aefgjof!BEES`PGGTFU`MTC!1
aefgjof!TOQT`WFS!9(i48



aefgjof!EVNNZ`UY`TUT!27(iB111!
aefgjof!EVNNZ`TUT!27(iB113!
aefgjof!PWG`TUT!43(i11119911!

aefgjof!OBOPTFD`DBSSZ`DPOTU!!43(i4C:B`DB11
aefgjof!STO`XJEUI!5

aefgjof!QIZ`TFMFDU`WBM!4(c111




aefgjof!UY`STU`NPEF!qptfehf!dml`uy`j!ps!ofhfehf!stu`dml`uy`o
aefgjof!UY`291`STU`NPEF!qptfehf!dml`uy`291`j!ps!ofhfehf!stu`dml`uy`291`o
aefgjof!SY`STU`NPEF!qptfehf!dml`sy`j!ps!ofhfehf!stu`dml`sy`o
aefgjof!SY`291`STU`NPEF!qptfehf!dml`sy`291`j!ps!ofhfehf!stu`dml`sy`291`o
aefgjof!BQQ`STU`NPEF!qptfehf!dml`bqq`j!ps!ofhfehf!stu`dml`bqq`o
aefgjof!DTS`STU`NPEF!qptfehf!dml`dts`j!ps!ofhfehf!stu`dml`dts`o
aefgjof!TSD`STU`NPEF!qptfehf!dml`tsd!ps!ofhfehf!stu`dml`tsd`o!!!!!
aefgjof!BIC`STU`NPEF!qptfehf!idml`j!ps!ofhfehf!isftfu`o
aefgjof!SNJJ`STU`NPEF!qptfehf!dml`snjj`j!ps!ofhfehf!stu`dml`snjj`o
aefgjof!QUQ`STU`NPEF!qptfehf!dml`quq`sfg`j!ps!ofhfehf!stu`dml`quq`sfg`o
aefgjof!UY`236`STU`NPEF!qptfehf!dml`uy`236`j!ps!ofhfehf!stu`dml`uy`236`o!!
aefgjof!SY`236`STU`NPEF!qptfehf!dml`sy`236`j!ps!ofhfehf!stu`dml`sy`236`o!!
aefgjof!STU`HN`NPEF!qptfehf!hn`dml!ps!ofhfehf!hn`sftfu`o
aefgjof!STU`HT`NPEF!qptfehf!ht`dml!ps!ofhfehf!ht`sftfu`o
aefgjof!EXCC`STU`NPEF!ps!ofhfehf!sftfu`o
aefgjof!SFWNJJ`NED`STU`NPEF!qptfehf!sfwnjj`ned`j!ps!ofhfehf!sfwnjj`ned`stu`o
aefgjof!SFWNJJ`UYDML`STU`NPEF!qptfehf!dml`sfwnjj`uy`j!ps!ofhfehf!stu`dml`sfwnjj`uy`o
aefgjof!SFWNJJ`SYDML`STU`NPEF!qptfehf!dml`sfwnjj`sy`j!ps!ofhfehf!stu`dml`sfwnjj`sy`o
aefgjof!STU`QDT`UY`NPEF!qptfehf!dml`uy2`j!ps!ofhfehf!stu`dml`uy2`j`o
aefgjof!STU`QDT`SY`NPEF!qptfehf!dml`sy2`j!ps!ofhfehf!stu`dml`sy2`j`o



aefgjof!TUT`XJEUI!27


aefgjof!EBG`TUT`XJEUI!6




aefgjof!CVGTJ[F`XJEUI!22
aefgjof!EFTD`SFBE`TJ[F!|4(c111-9(i21~
aefgjof!EFTD`XSJUF`TJ[F!|4(c111-9(i15~
aefgjof!UJNF`XSJUF`TJ[F!|4(c111-9(i19~
aefgjof!TJ[F`CBTF`NTC!21



aefgjof!XPSEDOU`XJEUI!2!
aefgjof!IESDOU`XJEUI!22



aefgjof!DPSF`TUBUVT`XJEUI!!43





aefgjof!TBWJOT!1


aefgjof!GMYQQT!1


aefgjof!JOU`UT!1


aefgjof!BMU`EFTD!1


aefgjof!SYDPF3!1


aefgjof!SYDPF2!1


aefgjof!UYDPF!1


aefgjof!BWCFO!1


aefgjof!FFFO!1


aefgjof!UT`UZQ3!1


aefgjof!UT`UZQ2!1


aefgjof!NNDFO!1


aefgjof!QNUSXL!1


aefgjof!QNUNHL!1


aefgjof!TNBFO!2

aefgjof!M4M5FO!1


aefgjof!QDTSFH!1


aefgjof!NVMUJBEES!1


aefgjof!IBTIG!1


aefgjof!FYIBTIG!1


aefgjof!IE`FO!1


aefgjof!TQFFE!3(c22!




aefgjof!UYE`JPX!!aUYE`XJEUI
aefgjof!SYE`JPX!!aSYE`XJEUI


aefgjof!OVN`SY`DI!2


aefgjof!OVN`UY`DI!2


aefgjof!OED!2




aefgjof!DNF`HNBD`NND`QSTFU`GDOU`WBM!42(i8GGG`GGG1
aefgjof!DNF`HNBD`NND`QSTFU`PDOU`WBM!42(i8GGG`G911

aefgjof!DNF`EJTBMMPX`MBUDIFT


aefgjof!DNF`HNBD`IBTI`JEY!7

aefgjof!DNF`HNBD`EFT`DUM`GJGP`XJEUI!3


aefgjof!DNF`HNBD`TUT`GJGP`XJEUI!)aTUT`XJEUI*


npevmf!DNF`hnbd`qiz`synvy!)
!!!!!!!!!
!!!!!!!!!!!!!!!!!!!!!!!!!!!tnb`ebub-!!!!!!!!!!!
!!!!!!!!!!!!!!!!!!!!!!!!!!!tnb`usbotepof`o-!!!!
!!!!!!!!!!!!!!!!!!!!!!!!!!!sy`tnb`ebub-!!!!!!!!
!!!!!!!!!!!!!!!!!!!!!!!!!!!sy`tnb`usbotepof`o-!
!!!!!!!!!!!!!!!!!!!!!!!!!!!
!!!!!!!!!!!!!!!!!!!!!!!!!!!qiz`sye`j-
!!!!!!!!!!!!!!!!!!!!!!!!!!!qiz`syew`j-
!!!!!!!!!!!!!!!!!!!!!!!!!!!qiz`syfs`j-
!!!!!!!!!!!!!!!!!!!!!!!!!!!qiz`dst`j-
!!!!!!!!!!!!!!!!!!!!!!!!!!!qiz`dpm`j-
!!!!!!!!!!!!!!!!!!!!!!!!!!!
!!!!!!!!!!!!!!!!!!!!!!!!!!!hnjj`sye-
!!!!!!!!!!!!!!!!!!!!!!!!!!!hnjj`syew-
!!!!!!!!!!!!!!!!!!!!!!!!!!!hnjj`syfs-
!!!!!!!!!!!!!!!!!!!!!!!!!!!hnjj`dst-
!!!!!!!!!!!!!!!!!!!!!!!!!!!hnjj`dpm
!!!!!!!!!!!!!!!!!!!!!!!!!!!*<!!!!!!!!
!!!!!!!!
!
!!!!!!!!

!!!!


!!!!

!!!!!
!!
!!!!

!!

!!!!


!!!!

!!!joqvu!\26;1^!!!!!!!!!!tnb`ebub!!!!!!!!!!!!<
!!!joqvu!!!!!!!!!!!!!!!!!tnb`usbotepof`o!!!!!<
!!!pvuqvu!\26;1^!!!!!!!!!sy`tnb`ebub!!!!!!!!!<
!!!pvuqvu!!!!!!!!!!!!!!!!sy`tnb`usbotepof`o!!<

!!
!!joqvu!!!!!!!!!!!!qiz`syew`j<!!!!!!!!!!!!!
!!!!!!!!!!!!!!!!!!!!!!!!!!!!!!!!!!!!!!!!!!!
!!!!!!!!!!!!!!!!!!!!!!!!!!!!!!!!!!!!!!!!!!!
!!!!!!!!!!!!!!!!!!!!!!!!!!!!!!!!!!!!!!!!!!!
!!!!!!!!!!!!!!!!!!!!!!!!!!!!!!!!!!!!!!!!!!!
!!joqvu!!!!!!!!!!!!qiz`syfs`j<!!!!!!!!!!!!!
!!!!!!!!!!!!!!!!!!!!!!!!!!!!!!!!!!!!!!!!!!!
!!joqvu!!\aSYE`JPX.2;1^!qiz`sye`j<!!!!!!!!!
!!!!!!!!!!!!!!!!!!!!!!!!!!!!!!!!!!!!!!!!!!!
!!!!!!!!!!!!!!!!!!!!!!!!!!!!!!!!!!!!!!!!!!!
!!!!!!!!!!!!!!!!!!!!!!!!!!!!!!!!!!!!!!!!!!!
!!joqvu!!!!!!!!!!!!qiz`dst`j<!!!!!!!!!!!!!!
!!!!!!!!!!!!!!!!!!!!!!!!!!!!!!!!!!!!!!!!!!!
!!joqvu!!!!!!!!!!!!qiz`dpm`j<!!!!!!!!!!!!!!

!!
!!
!!pvuqvu!\aSYE`XJEUI.2;1^!hnjj`sye<!!!!!!!!!!
!!pvuqvu!!!!!!!!!!!!!hnjj`syew<!!!!!!!!!!!!!!
!!pvuqvu!!!!!!!!!!!!!hnjj`syfs<!!!!!!!!!!!!!!
!!pvuqvu!!!!!!!!!!!!!hnjj`dst<!!!!!!!!!!!!!!!
!!pvuqvu!!!!!!!!!!!!!hnjj`dpm<!!!!!!!!!!!!!!!
!!
!!
!!
!!
!!bttjho!hnjj`sye!!>!qiz`sye`j<
!!bttjho!hnjj`syew!>!qiz`syew`j<
!!bttjho!hnjj`syfs!>!qiz`syfs`j<
!!bttjho!hnjj`dst!!>!qiz`dst`j<
!!bttjho!hnjj`dpm!!>!qiz`dpm`j<

!!!!!!!

!!
!!!!!!
!!
!!bttjho!sy`tnb`ebub!>!!tnb`ebub<!!!!
!!bttjho!sy`tnb`usbotepof`o!>!!tnb`usbotepof`o<!!!!
!!!!!!
!!!!!!!
!!!!!!


foenpevmf


npevmf!DNF`hnbd`qiz`uynvy!)

!!!!!!!!
!!!!!!!!!!!!!!!!!!!!!!!!!!!tdu`qpsutfmfdu-
!!!!!!!!!!!!!!!!!!!!!!!!!!!
!!!!!!!!!!!!!!!!!!!!!!!!!!!hnjj`uyfo`j-
!!!!!!!!!!!!!!!!!!!!!!!!!!!hnjj`uyfs`j-
!!!!!!!!!!!!!!!!!!!!!!!!!!!hnjj`uye`j-
!!!!!!!!!!!!!!!!!!!!!!!!!!!tnb`nep`p-!!!!
!!!!!!!!!!!!!!!!!!!!!!!!!!!tnb`nep`fo`p-!
!!!!!!!!!!!!!!!!!!!!!!!!!!!hnjj`nep`p-!!!
!!!!!!!!!!!!!!!!!!!!!!!!!!!hnjj`nep`p`f-!
!!!!!!!!!!!!!!!!!!!!!!!!!!!
!!!!!!!!!!!!!!!!!!!!!!!!!!!qiz`uyfo`p-
!!!!!!!!!!!!!!!!!!!!!!!!!!!qiz`uyfs`p-
!!!!!!!!!!!!!!!!!!!!!!!!!!!qiz`uye`p
!!!!!!!!!!!!!!!!!!!!!!!!!!!*<
!!!!!!!!
!!
!!
!!!!!!!!!!!!!!!!!!!!!!!!!!!!!!!!!!!!!!!!!

!!joqvu!!!!!!!!!!!!tdu`qpsutfmfdu<!!!!!!!

!!
!!joqvu!!!!!!!!!!!!hnjj`uyfo`j<!!!!!!!!!!
!!joqvu!!!!!!!!!!!!hnjj`uyfs`j<!!!!!!!!!!
!!joqvu!!\aUYE`XJEUI.2;1^!hnjj`uye`j<!!!!
!!





!!joqvu!!!!!!!!!!!!!!!!tnb`nep`p<!!!!!!
!!joqvu!!!!!!!!!!!!!!!!tnb`nep`fo`p<!!!
!!pvuqvu!!!!!!!!!!!!!!!hnjj`nep`p<!!!!!
!!pvuqvu!!!!!!!!!!!!!!!hnjj`nep`p`f<!!!

!!
!!
!!!!!!!!!!!!!!!!!!!!!!!!!!!!!!!!!!!!!!!!!
!!pvuqvu!!!!!!!!!!!qiz`uyfo`p<!!!!!!!!!!!
!!!!!!!!!!!!!!!!!!!!!!!!!!!!!!!!!!!!!!!!!
!!!!!!!!!!!!!!!!!!!!!!!!!!!!!!!!!!!!!!!!!
!!
!!pvuqvu!!!!!!!!!!!qiz`uyfs`p<!!!!!!!!!!!
!!!!!!!!!!!!!!!!!!!!!!!!!!!!!!!!!!!!!!!!!
!!!!!!!!!!!!!!!!!!!!!!!!!!!!!!!!!!!!!!!!!
!!pvuqvu!\aUYE`JPX.2;1^!qiz`uye`p<!!!!!!!
!!!!!!!!!!!!!!!!!!!!!!!!!!!!!!!!!!!!!!!!!
!!!!!!!!!!!!!!!!!!!!!!!!!!!!!!!!!!!!!!!!!
!!!!!!!!!!!!!!!!!!!!!!!!!!!!!!!!!!!!!!!!!
!!






!!bttjho!qiz`uyfs`p!!>!hnjj`uyfs`j<
!!bttjho!qiz`uyfo`p!!>!hnjj`uyfo`j<
!!bttjho!qiz`uye`p!!!>!hnjj`uye`j<

!!
!!!!!!!!
!!
!!bttjho!hnjj`nep`p!!!>!!tnb`nep`p<!!!!
!!bttjho!hnjj`nep`p`f!>!!tnb`nep`fo`p<!!!!
!!!!!!
!


foenpevmf!


`pragma protect end_protected
//protect_encode_end
module cme_ip_eth_mac_core_f_v3 (

  // Clocks and resets
  clk_tx_i,
                     clk_rx_i,
                     rst_clk_tx_n,
                     rst_clk_rx_n,
                     clk_csr_i,
                     rst_clk_csr_n,
                     // MAC Transmit interface
                     mti_val_i,          
                     mti_data_i,
                     mti_sof_i,
                     mti_eof_i,
                     mti_be_i,
                     mti_discrc_i,
                     mti_dispad_i,
                     mti_flowctrl_i,
                     mti_rdy_o,
                     mti_txstatus_o,
                     mti_txstatus_val_o,
                     // MAC Receive interface
                     mri_val_o,      
                     mri_data_o,
                     mri_be_o,
                     mri_sof_o,
                     mri_eof_o,
                     mri_rxstatus_o,
                     // MAC Control Interface(MCI)
                     mci_val_i,
                     mci_addr_i,
                     mci_rdwrn_i,
                     mci_wdata_i,
                     mci_be_i,
                     mci_ack_o,
                     mci_rdata_o,
                     mci_intr_o,
                     // MII Management Interface.
                     gmii_mdc_o,
                     gmii_mdi_i,
                     gmii_mdo_o,
                     gmii_mdo_o_e,
                     // PHY Interface
                     phy_txen_o,
                     phy_txer_o,
                     phy_txd_o,
                     phy_crs_i,
                     phy_col_i,
                     phy_rxdv_i,
                     phy_rxer_i,
                     phy_rxd_i
                     );
//protect_encode_begin
`pragma protect begin_protected
`pragma protect version=1
`pragma protect data_block
!!joqvu!!!!!!!!!!!!!!!!!!!!!!!!dml`dts`j<!!!!!!
!!joqvu!!!!!!!!!!!!!!!!!!!!!!!!stu`dml`dts`o<!!



!!

!
!


!
!!!!!!!!!!!!!!!!!!!!!!!!!!!!!!!!!!!!!!!!!!!!!!!!!!
!





!

!!!!!!!!!!!!!!!!!!!!!!!!!!!!!!!!!!!!!!!!!!!!!!!
!!joqvu!!!!!!!!!!!!!!!!!!!!!!nuj`wbm`j<!!!!!!!!!
!!joqvu!!\aEBUBXJEUI.2;1^!!!!nuj`ebub`j<!!!!!!!!
!!joqvu!!!!!!!!!!!!!!!!!!!!!!nuj`tpg`j<!!!!!!!!!
!!joqvu!!!!!!!!!!!!!!!!!!!!!!nuj`fpg`j<!!!!!!!!!
!!joqvu!!\aEBUBXJEUI075,2;1^!nuj`cf`j<!!!!!!!!!!
!!joqvu!!!!!!!!!!!!!!!!!!!!!!nuj`ejtdsd`j<!!!!!!
!!joqvu!!!!!!!!!!!!!!!!!!!!!!nuj`ejtqbe`j<!!!!!!
!!
!!joqvu!!!!!!!!!!!!!!!!!!!!!!nuj`gmpxdusm`j<!!!!
!!!!!!!!!!!!!!!!!!!!!!!!!!!!!!!!!!!!!!!!!!!!!!!!
!!
!!pvuqvu!!!!!!!!!!!!!!!!!!!!!nuj`sez`p<!!!!!!!!!
!!pvuqvu!\42;1^!!!!!!!!!!!!!!nuj`uytubuvt`p<!!!!
!!pvuqvu!!!!!!!!!!!!!!!!!!!!!nuj`uytubuvt`wbm`p<


!!pvuqvu!!!!!!!!!!!!!!!!!!!!!nsj`wbm`p<!!!!!!!!!
!!pvuqvu!\aEBUBXJEUI.2;1^!!!!nsj`ebub`p<!!!!!!!!
!!pvuqvu!\aEBUBXJEUI075,2;1^!nsj`cf`p<!!!!!!!!!!
!!pvuqvu!!!!!!!!!!!!!!!!!!!!!nsj`tpg`p<!!!!!!!!!
!!pvuqvu!!!!!!!!!!!!!!!!!!!!!nsj`fpg`p<!!!!!!!!!
!!pvuqvu!\aDPSF`TUBUVT`XJEUI.2;1^!nsj`sytubuvt`p<!

!!!!!!!!!!!!!!!!!!!!!!!!!!!!!!!!!!!!!!!!!!!!!!!!!!!!!!!!
!!!!!!!!!!!!!!!!!!!!!!!!!!!!!!!!!!!!!!!!!!!!!!!!!!!!!!!!

!!!!!!!!!!!!!!!!!!!!!!!!!!!!!!!!!!!!!!!!!!!!!!!!!!!!!!!!
!!!!!!!!!!!!!!!!!!!!!!!!!!!!!!!!!!!!!!!!!!!!!!!!!!!!!!!!


!!!!!!!!!!!!!!!!!!!!!!!!!!!!!!!!!!!!!!!!!!!!!!!!!!!!!!!!
!!!!!!!!!!!!!!!!!!!!!!!!!!!!!!!!!!!!!!!!!!!!!!!!!!!!!!!!


!!
!!joqvu!!!!!!!!!!!!!!!!!!dml`uy`j<!!!!!!!!!!!!!!
!!!!!!!!!!!!!!!!!!!!!!!!!!!!!!!!!!!!!!!!!!!!!!!!
!!joqvu!!!!!!!!!!!!!!!!!!dml`sy`j<!!!!!!!!!!!!!!
!!!!!!!!!!!!!!!!!!!!!!!!!!!!!!!!!!!!!!!!!!!!!!!!
!!joqvu!!!!!!!!!!!!!!!!!!stu`dml`uy`o<!!!!!!!!!!
!!joqvu!!!!!!!!!!!!!!!!!!stu`dml`sy`o<!!!!!!!!!!
!!!!!!!!!!!!!!!!!!!!!!!!!!!!!!!!!!!!!!!!!!!!!!!!
!
!
!!joqvu!!!!!!!!!!!!ndj`wbm`j<!!!!!!
!!joqvu!!\24;1^!!!!ndj`bees`j<!!!!!
!!joqvu!!!!!!!!!!!!ndj`sexso`j<!!!!
!!joqvu!!\42;1^!!!!ndj`xebub`j<!!!!
!!joqvu!!\4;1^!!!!!ndj`cf`j<!!!!!!!

!!pvuqvu!!!!!!!!!!!ndj`bdl`p<!!!!!!
!!pvuqvu!\42;1^!!!!ndj`sebub`p<!!!!
!!pvuqvu!!!!!!!!!!!ndj`jous`p<!!!!!

!
!
!!pvuqvu!!!!!!!!!!!hnjj`ned`p<!!!!!!!
!!joqvu!!!!!!!!!!!!hnjj`nej`j<!!!!!!!
!!pvuqvu!!!!!!!!!!!hnjj`nep`p<!!!!!!!
!!pvuqvu!!!!!!!!!!!hnjj`nep`p`f<!!!!!

!!!!!!!!!!!!!!!!!!!!!!!!!!!!!!!!!!!
!!!!!!!!!!!!!!!!!!!!!!!!!!!!!!!!!!!
!!
!!!!!!!!!!!!!!!!!!!!!!!!!!!!!!!!!!!!!!

!!
!!!!!!!!!!!!!!!!!!!!!!!!!!!!!!!!!!!!!!!!!!!
!!pvuqvu!!!!!!!!!!!qiz`uyfo`p<!!!!!!!!!!!
!!!!!!!!!!!!!!!!!!!!!!!!!!!!!!!!!!!!!!!!!
!!!!!!!!!!!!!!!!!!!!!!!!!!!!!!!!!!!!!!!!!
!!pvuqvu!!!!!!!!!!!qiz`uyfs`p<!!!!!!!!!!!
!!!!!!!!!!!!!!!!!!!!!!!!!!!!!!!!!!!!!!!!!
!!!!!!!!!!!!!!!!!!!!!!!!!!!!!!!!!!!!!!!!!
!!pvuqvu!\aUYE`JPX.2;1^!!qiz`uye`p<!!!!!!
!!!!!!!!!!!!!!!!!!!!!!!!!!!!!!!!!!!!!!!!!
!!!!!!!!!!!!!!!!!!!!!!!!!!!!!!!!!!!!!!!!!
!!!!!!!!!!!!!!!!!!!!!!!!!!!!!!!!!!!!!!!!!
!!
!!joqvu!!!!!!!!!!!!qiz`syew`j<!!!!!!!!!!!!!
!!!!!!!!!!!!!!!!!!!!!!!!!!!!!!!!!!!!!!!!!!!
!!!!!!!!!!!!!!!!!!!!!!!!!!!!!!!!!!!!!!!!!!!
!!!!!!!!!!!!!!!!!!!!!!!!!!!!!!!!!!!!!!!!!!!
!!!!!!!!!!!!!!!!!!!!!!!!!!!!!!!!!!!!!!!!!!!
!!joqvu!!!!!!!!!!!!qiz`syfs`j<!!!!!!!!!!!!!
!!!!!!!!!!!!!!!!!!!!!!!!!!!!!!!!!!!!!!!!!!!
!!
!!joqvu!!\aSYE`JPX.2;1^!!qiz`sye`j<!!!!!!!!
!!!!!!!!!!!!!!!!!!!!!!!!!!!!!!!!!!!!!!!!!!!
!!!!!!!!!!!!!!!!!!!!!!!!!!!!!!!!!!!!!!!!!!!
!!!!!!!!!!!!!!!!!!!!!!!!!!!!!!!!!!!!!!!!!!!
!!joqvu!!!!!!!!!!!!qiz`dst`j<!!!!!!!!!!!!!!
!!
!!joqvu!!!!!!!!!!!!qiz`dpm`j<!!!!!!!!!!!!!!
!
!




!xjsf!!!!!!!!!!!!!!!!!!!!!!!!!!!nuj`sez`p<
!xjsf!!!!!!!!!!!!!!!!!!!!!!!!!!!nuj`wbm`j<
!xjsf!!\aEBUBXJEUI.2;1^!!!!!!!!!nuj`ebub`j<
!xjsf!!!!!!!!!!!!!!!!!!!!!!!!!!!nuj`tpg`j<
!xjsf!!!!!!!!!!!!!!!!!!!!!!!!!!!nuj`fpg`j<
!xjsf!!\aEBUBXJEUI075,2;1^!!!!!!nuj`cf`j<
!xjsf!!!!!!!!!!!!!!!!!!!!!!!!!!!nuj`ejtqbe`j<!
!xjsf!!!!!!!!!!!!!!!!!!!!!!!!!!!nuj`ejtdsd`j<
!xjsf!!!!!!!!!!!!!!!!!!!!!!!!!!!nuj`gmpxdusm`j<
!xjsf!!!!!!!!!!!!!!!!!!!!!!!!!!!nuj`uytubuvt`wbm`p<
!xjsf!!\42;1^!!!!!!!!!!!!!!!!!!!nuj`uytubuvt`p<
!xjsf!!!!!!!!!!!!!!!!!!!!!!!!!!!nsj`wbm`p<!!
!xjsf!!\aEBUBXJEUI.2;1^!!!!!!!!!nsj`ebub`p<
!xjsf!!\aEBUBXJEUI075,2;1^!!!!!!nsj`cf`p<
!xjsf!!!!!!!!!!!!!!!!!!!!!!!!!!!nsj`tpg`p<
!xjsf!!!!!!!!!!!!!!!!!!!!!!!!!!!nsj`fpg`p<
!xjsf!!\aDPSF`TUBUVT`XJEUI.2;1^!nsj`sytubuvt`p<




!!

!!xjsf!!!!!!!!!!!!!!!!!!!!!!!!!!!!dml`dts<
!!xjsf!!!!!!!!!!!!!!!!!!!!!!!!!!!!stu`dml`dts<!!!!!!!!!!!!!!!











!!bttjho!dml`dts!>!dml`dts`j<

!!bttjho!stu`dml`dts!>!stu`dml`dts`o<
!!


!!












!!!!!!!!!!!!!!!!!













DNF`hnbd
!DNF`hnbd`jotu)
!!!!!!!!!!/dml`uy`j)dml`uy`j*-!!!!!!!
!!!!!!!!!!!!!!!!!!!!!!!/dml`sy`j)dml`sy`j*-
!!!!!!!!!!!!!!!!!!!!!!!/dml`dts`j)dml`dts*-
!!!!!!!!!!!!!!!!!!!!!!!/stu`dml`dts`o)stu`dml`dts*-
!!!!!!!!!!!!!!!!!!!!!!!/stu`dml`uy`o)stu`dml`uy`o*-
!!!!!!!!!!!!!!!!!!!!!!!/stu`dml`sy`o)stu`dml`sy`o*-
!!!!!!!!!!!!!!!!!!!!!!!/nuj`wbm`j)nuj`wbm`j*-!!!!!!!!!!
!!!!!!!!!!!!!!!!!!!!!!!/nuj`ebub`j)nuj`ebub`j*-
!!!!!!!!!!!!!!!!!!!!!!!/nuj`tpg`j)nuj`tpg`j*-
!!!!!!!!!!!!!!!!!!!!!!!/nuj`fpg`j)nuj`fpg`j*-
!!!!!!!!!!!!!!!!!!!!!!!/nuj`cf`j)nuj`cf`j*-
!!!!!!!!!!!!!!!!!!!!!!!/nuj`ejtdsd`j)nuj`ejtdsd`j*-
!!!!!!!!!!!!!!!!!!!!!!!/nuj`ejtqbe`j)nuj`ejtqbe`j*-
!!!!!!!!!!!!!!!!!!!!!!!/nuj`gmpxdusm`j)nuj`gmpxdusm`j*-
!!!!!!!!!!!!!!!!!!!!!!!/nuj`sez`p)nuj`sez`p*-
!!!!!!!!!!!!!!!!!!!!!!!/nuj`uytubuvt`p)nuj`uytubuvt`p*-
!!!!!!!!!!!!!!!!!!!!!!!/nuj`uytubuvt`wbm`p)nuj`uytubuvt`wbm`p*-
!!!!!!!!!!!!!!!!!!!!!!!/nsj`wbm`p)nsj`wbm`p*-!!!!!!
!!!!!!!!!!!!!!!!!!!!!!!/nsj`ebub`p)nsj`ebub`p*-
!!!!!!!!!!!!!!!!!!!!!!!/nsj`cf`p)nsj`cf`p*-
!!!!!!!!!!!!!!!!!!!!!!!/nsj`tpg`p)nsj`tpg`p*-
!!!!!!!!!!!!!!!!!!!!!!!/nsj`fpg`p)nsj`fpg`p*-
!!!!!!!!!!!!!!!!!!!!!!!/nsj`sytubuvt`p)nsj`sytubuvt`p*-
!!!!!!!!!!!!!!!!!!!!!!!/ndj`wbm`j)ndj`wbm`j*-!!!
!!!!!!!!!!!!!!!!!!!!!!!/ndj`bees`j)ndj`bees`j*-
!!!!!!!!!!!!!!!!!!!!!!!/ndj`sexso`j)ndj`sexso`j*-
!!!!!!!!!!!!!!!!!!!!!!!/ndj`xebub`j)ndj`xebub`j*-
!!!!!!!!!!!!!!!!!!!!!!!/ndj`cf`j)ndj`cf`j*-!!!!
!!!!!!!!!!!!!!!!!!!!!!!/ndj`bdl`p)ndj`bdl`p*-
!!!!!!!!!!!!!!!!!!!!!!!/ndj`sebub`p)ndj`sebub`p*-
!!!!!!!!!!!!!!!!!!!!!!!/ndj`jous`p)ndj`jous`p*-
!!!!!!!!!!!!!!!!!!!!!!!
!!!!!!!!!!!!!!!!!!!!!!!/hnjj`ned`p)hnjj`ned`p*-!!!
!!!!!!!!!!!!!!!!!!!!!!!/hnjj`nej`j)hnjj`nej`j*-
!!!!!!!!!!!!!!!!!!!!!!!/hnjj`nep`p)hnjj`nep`p*-
!!!!!!!!!!!!!!!!!!!!!!!/hnjj`nep`p`f)hnjj`nep`p`f*-
!!!!!!!!!!!!!!!!!!!!!!!/nbd`qpsutfmfdu`p)*-!
!!!!!!!!!!!!!!!!!!!!!!!/qiz`uyfo`p)qiz`uyfo`p*-!
!!!!!!!!!!!!!!!!!!!!!!!/qiz`uyfs`p)qiz`uyfs`p*-
!!!!!!!!!!!!!!!!!!!!!!!/qiz`uye`p)qiz`uye`p*-
!!!!!!!!!!!!!!!!!!!!!!!/qiz`dst`j)qiz`dst`j*-
!!!!!!!!!!!!!!!!!!!!!!!/qiz`dpm`j)qiz`dpm`j*-
!!!!!!!!!!!!!!!!!!!!!!!/qiz`syew`j)qiz`syew`j*-
!!!!!!!!!!!!!!!!!!!!!!!/qiz`syfs`j)qiz`syfs`j*-
!!!!!!!!!!!!!!!!!!!!!!!/qiz`sye`j)qiz`sye`j*
!!!!!!!!!!!!!!!!!!!!!!!*<







foenpevmf



npevmf!DNF`hnbd!)
!!!!!!!!
!!!!!!!!
!!!!!!!!dml`uy`j-
!!!!!!!!!!!!!!!!!dml`sy`j-
!!!!!!!!!!!!!!!!!dml`dts`j-
!!!!!!!!!!!!!!!!!stu`dml`uy`o-
!!!!!!!!!!!!!!!!!stu`dml`sy`o-
!!!!!!!!!!!!!!!!!stu`dml`dts`o-
!!!!!!!!!!!!!!!!!
!!!!!!!!!!!!!!!!!nuj`wbm`j-
!!!!!!!!!!!!!!!!!nuj`ebub`j-
!!!!!!!!!!!!!!!!!nuj`tpg`j-
!!!!!!!!!!!!!!!!!nuj`fpg`j-
!!!!!!!!!!!!!!!!!nuj`cf`j-
!!!!!!!!!!!!!!!!!nuj`ejtdsd`j-
!!!!!!!!!!!!!!!!!nuj`ejtqbe`j-
!!!!!!!!!!!!!!!!!nuj`gmpxdusm`j-
!!!!!!!!!!!!!!!!!nuj`sez`p-
!!!!!!!!!!!!!!!!!nuj`uytubuvt`p-
!!!!!!!!!!!!!!!!!nuj`uytubuvt`wbm`p-
!!!!!!!!!!!!!!!!!nsj`wbm`p-
!!!!!!!!!!!!!!!!!nsj`ebub`p-
!!!!!!!!!!!!!!!!!nsj`cf`p-
!!!!!!!!!!!!!!!!!nsj`tpg`p-
!!!!!!!!!!!!!!!!!nsj`fpg`p-
!!!!!!!!!!!!!!!!!nsj`sytubuvt`p-
!!!!!!!!!!!!!!!!!
!!!!!!!!!!!!!!!!!ndj`wbm`j-
!!!!!!!!!!!!!!!!!ndj`bees`j-
!!!!!!!!!!!!!!!!!ndj`sexso`j-
!!!!!!!!!!!!!!!!!ndj`xebub`j-
!!!!!!!!!!!!!!!!!ndj`cf`j-
!!!!!!!!!!!!!!!!!ndj`bdl`p-
!!!!!!!!!!!!!!!!!ndj`sebub`p-
!!!!!!!!!!!!!!!!!ndj`jous`p-
!!!!!!!!!!!!!!!!!
!!!!!!!!!!!!!!!!!hnjj`ned`p-
!!!!!!!!!!!!!!!!!hnjj`nej`j-
!!!!!!!!!!!!!!!!!hnjj`nep`p-
!!!!!!!!!!!!!!!!!hnjj`nep`p`f-
!!!!!!!!!!!!!!!!!nbd`qpsutfmfdu`p-
!!!!!!!!!!!!!!!!!qiz`uyfo`p-
!!!!!!!!!!!!!!!!!qiz`uyfs`p-
!!!!!!!!!!!!!!!!!qiz`uye`p-
!!!!!!!!!!!!!!!!!qiz`dst`j-
!!!!!!!!!!!!!!!!!qiz`dpm`j-
!!!!!!!!!!!!!!!!!qiz`syew`j-
!!!!!!!!!!!!!!!!!qiz`syfs`j-
!!!!!!!!!!!!!!!!!qiz`sye`j
!!!!!!!!!!!!!!!!!*<

!!joqvu!!!!!!!!!!!!!!!!!!!!!!dml`uy`j<!!!!!!!!!!!!!!
!!!!!!!!!!!!!!!!!!!!!!!!!!!!!!!!!!!!!!!!!!!!!!!!!!!!
!!!!!!!!!!!!!!!!!!!!!!!!!!!!!!!!!!!!!!!!!!!!!!!!!!!!
!!joqvu!!!!!!!!!!!!!!!!!!!!!!dml`sy`j<!!!!!!!!!!!!!!
!!!!!!!!!!!!!!!!!!!!!!!!!!!!!!!!!!!!!!!!!!!!!!!!!!!!
!!!!!!
!!joqvu!!!!!!!!!!!!!!!!!!!!!!dml`dts`j<!!!!!!!!!!!!!
!!


!!joqvu!!!!!!!!!!!!!!!!!!!!!!stu`dml`uy`o<!!!!!!!!!!
!!!!!!!!!!!!!!!!!!!!!!!!!!!!!!!!!!!!!!!!!!!!!!!!!!!!

!!joqvu!!!!!!!!!!!!!!!!!!!!!!stu`dml`sy`o<!!!!!!!!!!
!!!!!!!!!!!!!!!!!!!!!!!!!!!!!!!!!!!!!!!!!!!!!!!!!!!!
!!!!!!!!!!!!!!!!!!!!!!!!!!!!!!!!!!!!!!!!!!!!!!!!!!!!
!!joqvu!!!!!!!!!!!!!!!!!!!!!!stu`dml`dts`o<!!!!!!!!!
!!!!!!!!!!!!!!!!!!!!!!!!!!!!!!!!!!!!!!!!!!!!!!!!!!!!

!!!!!!!!!!!!!!!!!!!!!!!!!!!!!!!!!!!!!!!!!!!!!!!!!!!
!!!!!!!!!!!!!!!!!!!!!!!!!!!!!!!!!!!!!!!!!!!!!!!!!!!
!!
!!!!!!!!!!!!!!!!!!!!!!!!!!!!!!!!!!!!!!!!!!!!!!!!!!!!

!!!!!!!!!!!!!!!!!!!!!!!!!!!!!!!!!!!!!!!!!!!!!!!!!!!!
!!!!!!!!!!!!!!!!!!!!!!!!!!!!!!!!!!!!!!!!!!!!!!!!!!!!
!!
!!!!!!!!!!!!!!!!!!!!!!!!!!!!!!!!!!!!!!!!!!!!!!!!!!!!
!!!!!!!!!!!!!!!!!!!!!!!!!!!!!!!!!!!!!!!!!!!!!!!!!!!!
!!!!!!!!!!!!!!!!!!!!!!!!!!!!!!!!!!!!!!!!!!!!!!!!!!!!
!!!!!!!!!!!!!!!!!!!!!!!!!!!!!!!!!!!!!!!!!!!!!!!!!!!!
!!!!!!!!!!!!!!!!!!!!!!!!!!!!!!!!!!!!!!!!!!!!!!!!!!!!
!!!!!!!!!!!!!!!!!!!!!!!!!!!!!!!!!!!!!!!!!!!!!!!!!!!!
!!!!!!!!!!!!!!!!!!!!!!!!!!!!!!!!!!!!!!!!!!!!!!!!!!!!
!!!!!!!!!!!!!!!!!!!!!!!!!!!!!!!!!!!!!!!!!!!!!!!!!!!!
!!!!!!!!!!!!!!!!!!!!!!!!!!!!!!!!!!!!!!!!!!!!!!!!!!!!
!!!!!!!!!!!!!!!!!!!!!!!!!!!!!!!!!!!!!!!!!!!!!!!!!!!!
!!!!!!!!!!!!!!!!!!!!!!!!!!!!!!!!!!!!!!!!!!!!!!!!!!!!
!!!!!!!!!!!!!!!!!!!!!!!!!!!!!!!!!!!!!!!!!
!!
!!!!!!!!!!!!!!!!!!!!!!!!!!!!!!!!!!!!!!!!!!!!!!!!!!!!
!!!!!!!!!!!!!!!!!!!!!!!!!!!!!!!!!!!!!!!!!!!!!!!!!!!!
!!!!!!!!!!!!!!!!!!!!!!!!!!!!!!!!!!!!!!!!!!!!!!!!!!!!

!!!!!!!!!!!!!!!!!!!!!!!!!!!!!!!!!!!!!!!!!!!!!!!!!!!!
!!!!!!!!!!!!!!!!!!!!!!!!!!!!!!!!!!!!!!!!!!!!!!!!!!!!





!!joqvu!!!!!!!!!!!!!!!!!!!!!!nuj`wbm`j<!!!!!!!!!
!!joqvu!!\aEBUBXJEUI.2;1^!!!!nuj`ebub`j<!!!!!!!!
!!joqvu!!!!!!!!!!!!!!!!!!!!!!nuj`tpg`j<!!!!!!!!!
!!joqvu!!!!!!!!!!!!!!!!!!!!!!nuj`fpg`j<!!!!!!!!!
!!joqvu!!\aEBUBXJEUI075,2;1^!nuj`cf`j<!!!!!!!!!!
!!joqvu!!!!!!!!!!!!!!!!!!!!!!nuj`ejtdsd`j<!!!!!!
!!joqvu!!!!!!!!!!!!!!!!!!!!!!nuj`ejtqbe`j<!!!!!!

!!joqvu!!!!!!!!!!!!!!!!!!!!!!nuj`gmpxdusm`j<!!!!
!!!!!!!!!!!!!!!!!!!!!!!!!!!!!!!!!!!!!!!!!!!!!!!!
!!
!!pvuqvu!!!!!!!!!!!!!!!!!!!!!nuj`sez`p<!!!!!!!!!
!!pvuqvu!\42;1^!!!!!!!!!!!!!!nuj`uytubuvt`p<!!!!
!!pvuqvu!!!!!!!!!!!!!!!!!!!!!nuj`uytubuvt`wbm`p<


!!pvuqvu!!!!!!!!!!!!!!!!!!!!!nsj`wbm`p<!!!!!!!!!
!!pvuqvu!\aEBUBXJEUI.2;1^!!!!nsj`ebub`p<!!!!!!!!
!!pvuqvu!\aEBUBXJEUI075,2;1^!nsj`cf`p<!!!!!!!!!!
!!pvuqvu!!!!!!!!!!!!!!!!!!!!!nsj`tpg`p<!!!!!!!!!
!!pvuqvu!!!!!!!!!!!!!!!!!!!!!nsj`fpg`p<!!!!!!!!!
!!pvuqvu!\aDPSF`TUBUVT`XJEUI.2;1^!nsj`sytubuvt`p<!


!!joqvu!!!!!!!!!!!!ndj`wbm`j<!!!!!!
!!!!!!!!!!!!!!!!!!!!!!!!!!!!!!!!!!!
!!!!!!!!!!!!!!!!!!!!!!!!!!!!!!!!!!!
!!joqvu!!\24;1^!!!!ndj`bees`j<!!!!!
!!joqvu!!!!!!!!!!!!ndj`sexso`j<!!!!
!!!!!!!!!!!!!!!!!!!!!!!!!!!!!!!!!!!
!!!!!!!!!!!!!!!!!!!!!!!!!!!!!!!!!!!
!!joqvu!!\42;1^!!!!ndj`xebub`j<!!!!
!!joqvu!!\4;1^!!!!!ndj`cf`j<!!!!!!!
!!pvuqvu!!!!!!!!!!!ndj`bdl`p<!!!!!!
!!pvuqvu!\42;1^!!!!ndj`sebub`p<!!!!
!!
!!pvuqvu!!!!!!!!!!!ndj`jous`p<!!!!!!!
!!!!!!!!!!!!!!!!!!!!!!!!!!!!!!!!!!!!!
!!!!!!!!!!!!!!!!!!!!!!!!!!!!!!!!!!!!!
!!!!!!!!!!!!!!!!!!!!!!!!!!!!!!!!!!!!!
!!!!!!!!!!!!!!!!!!!!!!!!!!!!!!!!!!!!!
!!
!!pvuqvu!!!!!!!!!!!hnjj`ned`p<!!!!!!!
!!joqvu!!!!!!!!!!!!hnjj`nej`j<!!!!!!!
!!pvuqvu!!!!!!!!!!!hnjj`nep`p<!!!!!!!
!!pvuqvu!!!!!!!!!!!hnjj`nep`p`f<!!!!!
!!!!!!!!!!!!!!!!!!!!!!!!!!!!!!!!!!!

!!pvuqvu!!!!!!!!!!!nbd`qpsutfmfdu`p<!
!!!!!!!!!!!!!!!!!!!!!!!!!!!!!!!!!!!
!!!!!!!!!!!!!!!!!!!!!!!!!!!!!!!!!!!
!!!!!!!!!!!!!!!!!!!!!!!!!!!!!!!!!!!!!

!!
!!!!!!!!!!!!!!!!!!!!!!!!!!!!!!!!!!!!!!
!
!!
!!!!!!!!!!!!!!!!!!!!!!!!!!!!!!!!!!!!!!!!!!!
!!pvuqvu!!!!!!!!!!!qiz`uyfo`p<!!!!!!!!!!!
!!!!!!!!!!!!!!!!!!!!!!!!!!!!!!!!!!!!!!!!!
!!!!!!!!!!!!!!!!!!!!!!!!!!!!!!!!!!!!!!!!!
!!pvuqvu!!!!!!!!!!!qiz`uyfs`p<!!!!!!!!!!!
!!!!!!!!!!!!!!!!!!!!!!!!!!!!!!!!!!!!!!!!!
!!!!!!!!!!!!!!!!!!!!!!!!!!!!!!!!!!!!!!!!!
!!pvuqvu!\aUYE`JPX.2;1^!!qiz`uye`p<!!!!!!
!!!!!!!!!!!!!!!!!!!!!!!!!!!!!!!!!!!!!!!!!
!!!!!!!!!!!!!!!!!!!!!!!!!!!!!!!!!!!!!!!!!
!!!!!!!!!!!!!!!!!!!!!!!!!!!!!!!!!!!!!!!!!
!!
!!joqvu!!!!!!!!!!!!qiz`syew`j<!!!!!!!!!!!!!
!!!!!!!!!!!!!!!!!!!!!!!!!!!!!!!!!!!!!!!!!!!
!!!!!!!!!!!!!!!!!!!!!!!!!!!!!!!!!!!!!!!!!!!
!!!!!!!!!!!!!!!!!!!!!!!!!!!!!!!!!!!!!!!!!!!
!!!!!!!!!!!!!!!!!!!!!!!!!!!!!!!!!!!!!!!!!!!
!!joqvu!!!!!!!!!!!!qiz`syfs`j<!!!!!!!!!!!!!
!!!!!!!!!!!!!!!!!!!!!!!!!!!!!!!!!!!!!!!!!!!
!!
!!joqvu!!\aSYE`JPX.2;1^!!qiz`sye`j<!!!!!!!!
!!!!!!!!!!!!!!!!!!!!!!!!!!!!!!!!!!!!!!!!!!!
!!!!!!!!!!!!!!!!!!!!!!!!!!!!!!!!!!!!!!!!!!!
!!!!!!!!!!!!!!!!!!!!!!!!!!!!!!!!!!!!!!!!!!!
!!joqvu!!!!!!!!!!!!qiz`dst`j<!!!!!!!!!!!!!!
!!
!!joqvu!!!!!!!!!!!!qiz`dpm`j<!!!!!!!!!!!!!!



!
!
!!
!!
!!
!!xjsf!!!!!!!!!!!!!!!!!!!!hnjj`uyfo`p<
!!xjsf!!!!!!!!!!!!!!!!!!!!hnjj`uyfs`p<
!!xjsf!!\aUYE`XJEUI.2;1^!!hnjj`uye`p<
!!xjsf!!!!!!!!!!!!!!!!!!!!nuf`uyfo<
!!xjsf!!!!!!!!!!!!!!!!!!!!nuf`uyfs<
!!xjsf!!\aUYE`XJEUI.2;1^!!nuf`uye<
!!
!!
!!xjsf!!\aSYE`XJEUI.2;1^!!hnjj`sye<
!!xjsf!!!!!!!!!!!!!!!!!!!!hnjj`syew<
!!xjsf!!!!!!!!!!!!!!!!!!!!hnjj`syfs<
!!xjsf!!!!!!!!!!!!!!!!!!!!hnjj`dst<
!!xjsf!!!!!!!!!!!!!!!!!!!!hnjj`dpm<
!
!!xjsf!!\3;1^!!!!!!qiz`tfmfdu<
!!
!!xjsf!!!!!!!!!!!!!stu`dml`uy`o<
!!xjsf!!!!!!!!!!!!!stu`dml`sy`o<
!!
!!xjsf!!!!!!!!!!!!!ugd`sfr<
!!xjsf!!\8;1^!!!!!!ugd`ebub<
!!xjsf!!!!!!!!!!!!!ugd`ebub`wbmje<
!!xjsf!!!!!!!!!!!!!ugd`tpg<
!!xjsf!!!!!!!!!!!!!ugd`fpg<
!!xjsf!!\42;1^!!!!!ugd`uytubuvt<
!!xjsf!!!!!!!!!!!!!ugd`uytubuvt`wbmje<
!!xjsf!!\2;1^!!!!!!ugd`gtn`tut<
!!xjsf!!!!!!!!!!!!!uqf`hou<
!!xjsf!!!!!!!!!!!!!uqf`bdl<
!!xjsf!!!!!!!!!!!!!uqf`bcpsu<
!!xjsf!!\42;1^!!!!!uqf`uytubuvt<
!!xjsf!!!!!!!!!!!!!uqf`uytubuvt`wbmje<
!!xjsf!!\2;1^!!!!!!nuf`ech`tut<
!!
!!xjsf!!!!!!!!!!!!!sqf`ebub`wbmje<
!!xjsf!!\8;1^!!!!!!sqf`ebub<
!!xjsf!!!!!!!!!!!!!sqf`tpg<
!!xjsf!!!!!!!!!!!!!sqf`fpg<
!!xjsf!!!!!!!!!!!!!sqf`qbzmpbe`tubsu<
!!xjsf!!!!!!!!!!!!!sqf`qbedsd`tusjq<
!!xjsf!!!!!!!!!!!!!sqf`tubuvt`wbmje<
!!xjsf!!\24;1^!!!!!sqf`sdwe`gsbnf`tj{f<
!!xjsf!!\34;1^!!!!!sqf`tubuvt<
!!xjsf!!!!!!!!!!!!!sqf`wmbo`gs`tut`wbmje<
!!xjsf!!!!!!!!!!!!!sqf`gtn`tut<
!!xjsf!!!!!!!!!!!!!gsy`mpbe`qbvtf`ujnf<
!!xjsf!!\26;1^!!!!!gsy`qbvtf`ujnf<
!!xjsf!!\2;1^!!!!!!sgd`gtn`tut<
!!xjsf!!\aDNF`HNBD`IBTI`JEY.2;1^!dsy`ebdsd<

!!xjsf!!!!!!!!!!!!!bgc`qfsgfdu`nbudi`eb<!!
!!xjsf!!!!!!!!!!!!!bgc`ebg`gjmufsgbjm<
!!xjsf!!!!!!!!!!!!!bgc`ebg`gjmufsgbjm`wbmje<
!!xjsf!!!!!!!!!!!!!bgc`tbg`gjmufsgbjm<
!!xjsf!!!!!!!!!!!!!bgc`tbg`gjmufsgbjm`wbmje<
!!xjsf!!!!!!!!!!!!!bgc`sdwcspbedbtu<
!!xjsf!!!!!!!!!!!!!bgc`sdwnvmujdbtu<
!!xjsf!\aEBG`TUT`XJEUI.2;1^!bgc`ebg`bees<!
!!xjsf!!!!!!!!!!!!!bgc`tb`tfmfdufe<
!!
!!xjsf!\38;1^!!!!!!ds`sfh1<
!!xjsf!!!!!!!!!!!!!ds`sfh1`czuf1`xs<
!!xjsf!!!!!!!!!!!!!ds`sfh1`czuf2`xs<
!!xjsf!!!!!!!!!!!!!ds`sfh1`czuf3`xs<
!!xjsf!\23;1^!!!!!!ds`sfh2<
!!xjsf!!!!!!!!!!!!!ds`sfh2`czuf1`xs<
!!xjsf!!!!!!!!!!!!!ds`sfh2`czuf2`xs<

!!xjsf!\26;1^!!!!!!ds`sfh7<
!!xjsf!!!!!!!!!!!!!ds`sfh7`czuf1`xs<
!!xjsf!\26;1^!!!!!!ds`qbvtfujnf<
!xjsf!\29;1^!!!!!!ds`wmboubh<
!!xjsf!\58;1^!!!!!!ds`nbdbees1<
!!



!
!!
!!xjsf!!!!!!!!!!!!!!tdu`dst<
!!xjsf!!!!!!!!!!!!!!tdu`dpm<
!!xjsf!!!!!!!!!!!!!!tds`dpm<
!!xjsf!!!!!!!!!!!!!!tdu`kbccfs`f<
!!xjsf!!!!!!!!!!!!!!tdu`kvncpgsbnf`f<
!!xjsf!\3;1^!!!!!!!!tdu`jgh<
!!xjsf!!!!!!!!!!!!!!tdu`qpsutfmfdu`p<
!!xjsf!!!!!!!!!!!!!!tds`qpsutfmfdu<
!!xjsf!!!!!!!!!!!!!!tdu`gsbnfcvstu`f<
!!xjsf!!!!!!!!!!!!!!tdu`evqmfynpef`p<
!!xjsf!!!!!!!!!!!!!!tds`evqmfynpef<
!!xjsf!!!!!!!!!!!!!!tdu`ejtsfusz<
!!xjsf!\2;1^!!!!!!!!tdu`cbdlpgg`mnu<
!!xjsf!!!!!!!!!!!!!!tdu`efgfssbm`dil<
!!xjsf!!!!!!!!!!!!!!tdu`usbotnju`f<
!!xjsf!\2;1^!!!!!!!!tdu`qsfncm`tj{<
!!xjsf!!!!!!!!!!!!!!tds`ejtsfdfjwfpxo<
!!xjsf!!!!!!!!!!!!!!tds`mppqcbdl`npef<
!!xjsf!!!!!!!!!!!!!!tds`uzqf`dsdtusjq`f<
!!xjsf!!!!!!!!!!!!!!tds`3l`qlu`f<
!!xjsf!\25;1^!!!!!!!ds`xeph`up<
!!xjsf!\25;1^!!!!!!!tds`xeph`up<
!!xjsf!!!!!!!!!!!!!!tdb`3l`qlu`f<
!!xjsf!!!!!!!!!!!!!!tds`xbudieph`f<
!!xjsf!!!!!!!!!!!!!!tds`kvncpgsbnf`f<
!!xjsf!!!!!!!!!!!!!!tds`bvupdsdqbetusjq<
!!xjsf!!!!!!!!!!!!!!tds`jqdiltvn`f<
!!xjsf!!!!!!!!!!!!!!tds`sfdfjwf`f<
!!xjsf!\26;1^!!!!!!!tdu`qbvtfujnf<
!!xjsf!!!!!!!!!!!!!!tdu`cbdlqsfttvsf<
!!xjsf!!!!!!!!!!!!!!tdu`uydusmgsbnf<
!!xjsf!!!!!!!!!!!!!!guy`uydusm`epof<
!!xjsf!!!!!!!!!!!!!!guy`ebub`wbmje<
!!xjsf!!!!!!!!!!!!!!tuy`qbvtf`rvboub<
!!xjsf!!!!!!!!!!!!!!tuy`syqbvtf`f<
!!xjsf!!!!!!!!!!!!!!tdu`uygmpxdusm`f<
!!xjsf!!!!!!!!!!!!!!tdu`ejtbcmf`{rqg<
!!xjsf!\2;1^!!!!!!!!tdu`gmpxuisfti<
!!xjsf!!!!!!!!!!!!!!tdu`mpbe`qbvtf`ujnf<
!!xjsf!!!!!!!!!!!!!!tdb`uydusm`epof<
!!xjsf!!!!!!!!!!!!!!tds`sygmpxdusm`f<
!!xjsf!!!!!!!!!!!!!!tds`vojdbtuefufdu<
!!xjsf!\2;1^!!!!!!!!tds`qbttdusmgsbnf<
!!xjsf!!!!!!!!!!!!!!tds`ejtcspbedbtu<
!!xjsf!!!!!!!!!!!!!!tds`qspnjtdpvtnpef<
!!xjsf!!!!!!!!!!!!!!tds`sfdfjwfbmm<
!!xjsf!!!!!!!!!!!!!!tds`tbgjmufs`f<
!!xjsf!!!!!!!!!!!!!!tds`wugjmufs`f<
!!xjsf!!!!!!!!!!!!!!tds`tbjowfstfgjmufs<
!!xjsf!!!!!!!!!!!!!!tds`ebjowfstfgjmufs<
!!xjsf!!!!!!!!!!!!!!tds`qbttbmmnvmujdbtu<
!!xjsf!!!!!!!!!!!!!!tds`ibtivojdbtu<
!!xjsf!!!!!!!!!!!!!!tds`ibtinvmujdbtu<
!!xjsf!!!!!!!!!!!!!!tds`ibtioqfsgfdu`f<
!xjsf!\29;1^!!!!!!!tds`wmboubh<!!!!!!!!!!!!
!!xjsf!!!!!!!!!!!!!!tdu`twmbo`fo<!!!!!!!!!!!
!!xjsf!\58;1^!!!!!!!tds`nbdbees1<
!!xjsf!\58;1^!!!!!!!tdu`nbdbees1<
!!xjsf!\7;1^!!!!!!!!tdb`nbd`ech`tut<

!!xjsf!!!!!!!!!!!!!!ndj`sexso<!

!!xjsf!!!!!!!!!!!!!ds`tnbdnewme<
!!xjsf!\5;1^!!!!!!!ds`tnbsfhbees<
!!xjsf!!!!!!!!!!!!!ds`se`xso<
!!xjsf!\5;1^!!!!!!!ds`tnbqizbees<
!!xjsf!\26;1^!!!!!!ds`tnbebub<
!!xjsf!!!!!!!!!!!!!sy`tnb`usbotepof`o<
!!xjsf!!\26;1^!!!!!sy`tnb`ebub<

!!xjsf!\4;1^!!!!!!!ds`bqqdmlsbohf<
!!xjsf!!!!!!!!!!!!!tnb`usbotepof`o<
!!xjsf!!\26;1^!!!!!tnb`ebub<
!!xjsf!!!!!!!!!!!!!tnb`nep`p<
!!xjsf!!!!!!!!!!!!!tnb`nep`fo`p<
!



!!

!!xjsf!\aUYE`XJEUI,2;1^!mqcl`ebub<!!!!!!!!!!!
!!xjsf!!!!!!!!!!!!!!stu`dml`sy`po<!!!!!!!!!!!
!!!!!!!!!!!!!!!!!!!!!!!!!!!!!!!!!!!!!!!!!!!!!
!!xjsf!!!!!!!!!!!!!!stu`dml`dts`po<!!!!!!!!!!
!!!!!!!!!!!!!!!!!!!!!!!!!!!!!!!!!!!!!!!!!!!!!

!!bttjho!stu`dml`sy`po!>!stu`dml`sy`o<
!!bttjho!stu`dml`dts`po!>!stu`dml`dts`o<


!!bttjho!nbd`qpsutfmfdu`p!>!ds`sfh1\26^<
!!bttjho!ndj`sexso!>!ndj`sexso`j<



!!bttjho!qiz`tfmfdu!>!aQIZ`TFMFDU`WBM<

!!bttjho!!hnjj`uyfo`p!>!nuf`uyfo<
!!bttjho!!hnjj`uyfs`p!>!nuf`uyfs<
!!bttjho!!hnjj`uye`p!!>!nuf`uye<
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
